IImasterII/mitk-rk-site/assets/photos/impeller-02.png

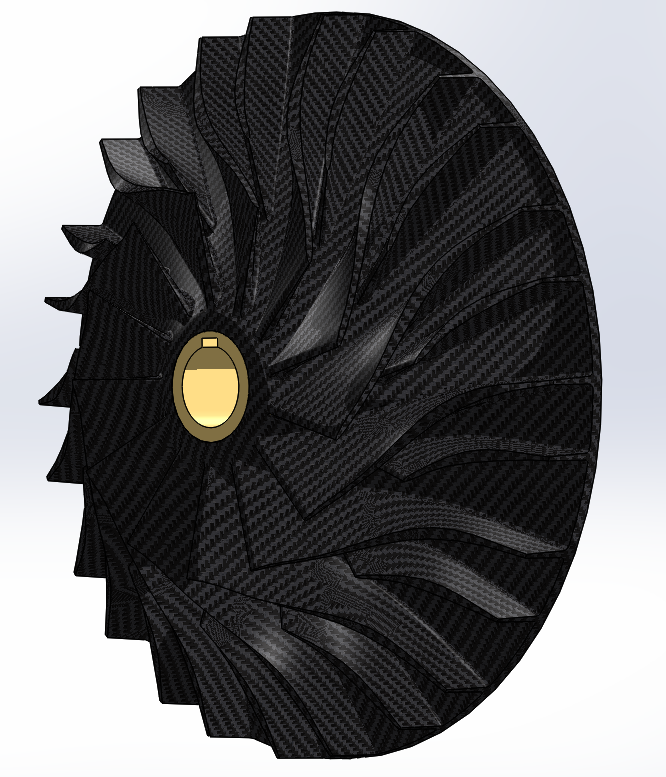
assets/photos/impeller-02.png
