IImasterII/mitk-rk-site/documents/0006_ps_d_.docx

Команда МИТК-РК

СОГЛАСОВАНО __________ | УТВЕРЖДАЮ __________

РАБОЧИЕ КОЛЁСА РК-200-Э И РК-200-Д ДИАМЕТРОМ 200 ММ

ПАСПОРТ РК-200-Д

EMTH.19.01.02.59.00.000.0006 ПС

2026

# 1 Идентификационные данные

Таблица 1 — Идентификация конкретного экземпляра

Поле | Значение
Обозначение | РК-200-Д
Критерий оптимизации | максимальное расчётное давление (одномерная модель)
Материальное исполнение | М1 / М2 (нужное отметить); М2 — 1 наружный слой ткани 0,2 мм (сухая)
Серийный номер
Дата изготовления
Файл модели/версия
Партия PA12-CF10
Ответственный изготовитель

# 2 Основные параметры

Таблица 2 — Номинальные геометрические параметры

Параметр | Значение
D2 | 200 мм
D1s | 105,075 мм
D1h | 40 мм
b2 | 14,242 мм
Основные/сплиттерные лопатки | 13/13
Угол назад от радиального | 5,000°
Задний диск | 3 мм
Втулка | Сталь 40Х; H49,5; Ø30/Ø22; паз 6×6 мм

# 3 Предварительные расчётные ориентиры

Таблица 3 — Предварительные расчётные ориентиры

n, мин⁻¹ | ηₜₜ, % | πₜₜ | Δpₜ, кПа | ṁ, кг/с | P, кВт | M, Н·м
3000 | — | ≈1,0072 | ≈0,727 | ≈0,062 | — | —
12000 | ≈71,23 | ≈1,1193 | ≈12,089 | ≈0,254 | ≈3,615 | ≈2,877

Статус значений. Таблица 3 содержит предварительные расчётные ориентиры, а не подтверждённые характеристики изделия. На 3 000 мин⁻¹ давление и расход оценены масштабированием; КПД, мощность и момент не назначены и определяются на стенде. Данные для 12 000 мин⁻¹ относятся только к расчётной точке и не разрешают разгон. Результаты CFD, FEA, модального анализа и стенда вносят в раздел 7 по подписанным отчётам.

# 4 Данные изготовления

Таблица 4 — Данные изготовления

Параметр | Запись | Параметр | Запись
Принтер/серийный номер | | Сопло
Слайсер/профиль | | Высота слоя | __________ мм
Сушка | 100 °C/10 ч; факт __________ | Отжиг | 100 °C/16 ч; факт __________
Масса после печати | __________ г | Масса готового | __________ г
Клей втулки | | Усилие запрессовки | __________ кН
Для М2 ткань | | Эпоксидная система

# 5 Результаты приёмки

Таблица 5 — Результаты приёмочного контроля

Контроль | Результат | Статус
Наружный диаметр D2 | __________ мм | годно / не годно (нужное отметить)
Радиальное биение | __________ мм | годно / не годно (нужное отметить)
Торцевое биение | __________ мм | годно / не годно (нужное отметить)
Визуальный контроль лопаток | | годно / не годно (нужное отметить)
Втулка и клеевое соединение | | годно / не годно (нужное отметить)
Остаточный дисбаланс | __________ г·мм | годно / не годно (нужное отметить)
Заключение | годно / доработка / брак (нужное отметить)

# 6 История испытаний и осмотров

Таблица 6 — История испытаний и осмотров

Дата | Режим | Наработка | Результат/дефекты | Подпись
| __________ мин⁻¹
| __________ мин⁻¹
| __________ мин⁻¹
| __________ мин⁻¹
| __________ мин⁻¹
| __________ мин⁻¹
| __________ мин⁻¹
| __________ мин⁻¹

# 7 Результаты CAE

Таблица 7 — Контролируемые результаты расчётов

Расчёт | Документ | Ключевые результаты | Статус
ANSYS CFD | № __________
ANSYS Mechanical | № __________
Modal | № __________

Ограничение. Незаполненный паспорт является только формой регистрационного документа и не подтверждает годность конкретного экземпляра. Режим 3 000 мин⁻¹ допускается после заполнения разделов изготовления и приёмки, балансировки и письменного допуска по ПМ. Разгон до 12 000 мин⁻¹ запрещён до закрытия CFD/FEA, модального анализа, проверки втулки и защитного корпуса и выпуска отдельного письменного допуска.

EMTH.19.01.02.59.00.000.0006 ПС Вер. Лист 01 3 Изм. Лист № докум. Подп. Дата Копировал Формат A4

Изм. Лист № докум. Подп. Дата Разраб. EMTH.19.01.02.59.00.000.0006 ПС 01 Пров. Т. контр. Рабочие колёса РК-200-Э и РК-200-Д диаметром 200 мм Лит. Лист Листов Н. контр. 2 1 Утв. Команда МИТК-РК Копировал Формат A4
