IImasterII/mitk-rk-site/documents/0009_tb.docx

Команда МИТК-РК

СОГЛАСОВАНО __________ | УТВЕРЖДАЮ __________

РАБОЧИЕ КОЛЁСА РК-200-Э И РК-200-Д ДИАМЕТРОМ 200 ММ

ТАБЛИЦА. МАТРИЦА ТРЕБОВАНИЙ И ПОДТВЕРЖДЕНИЙ

EMTH.19.01.02.59.00.000.0009 ТБ

2026

# 1 Правила статусов

Таблица 1 — Локальные коды статусов матрицы

Код | Статус | Смысл
П | Подтверждено | Есть объективное доказательство
З | Задано проектом | Требование зафиксировано, подтверждение предстоит
О | Открыто | Нужен расчёт, протокол или файл
Н/П | Не применяется | Не относится к выбранному исполнению

# 2 Матрица

Таблица 2 — Требования, методы и объективные доказательства

ID | Требование | Метод | Доказательство | Статус
G-01 | После удаления припуска заготовки Ø202 мм D2 готового колеса — 200 мм | STEP/чертёж | 0007 Д; размерный протокол | П для Э; О для Д
G-02 | Задний диск 3 мм | STEP/чертёж | 0007 Д | П для Э; О для Д
G-03 | Э: 10+10 лопаток | STEP | 0007 Д | П
G-04 | Д: 13+13 лопаток | STEP | 0007 Д | О до финального STEP
G-05 | Одно допустимое твёрдое тело | STEP-анализ | 0007 Д | П для Э; О для Д
G-06 | Корни лопаток соединены со ступицей | STEP/сечения | 0007 Д | П для Э; О для Д
M-01 | Материал Fiberon PA12-CF10 | Паспорт партии | 0005/0006 ПС | З
M-02 | Сушка 100 °C/10 ч | Журнал | 0004 МК; протокол | З
M-03 | Отжиг 100 °C/16 ч | Термограмма | 0004 МК; протокол | З
M-04 | М2: один наружный слой ткани 0,2 мм (сухая) | Паспорт/измерение | 0011 Д; протокол М2 | З
I-01 | Втулка из стали 40Х: H49,5; Ø30/Ø22 | Чертёж/контроль | 0002 ТУ; 0005/0006 ПС | З
I-02 | Шпоночный паз 6×6 | Калибр/контроль | 0005/0006 ПС | З
I-03 | Накатка, запрессовка и клей | Протокол сборки | 0004 МК; 0005/0006 ПС | З
A-01 | Допуск и безопасная работа на стенде при 3 000 мин⁻¹ | Стенд | 0003 ПМ; протокол | О
A-02 | Расчётная точка 12 000 мин⁻¹; эксплуатация запрещена без отдельного допуска | CFD/Mechanical | отчёты CFD/FEA/Modal; отдельный допуск | О
A-03 | Э: ηₜₜ≈74 % по предварительной одномерной модели | Одномерный расчёт | 0001 ПЗ; машинный протокол | О до протокола расчёта
A-04 | Д: ηₜₜ≈71 % по предварительной одномерной модели | Одномерный расчёт | 0001 ПЗ; машинный протокол | О до протокола расчёта
A-05 | Э: Δpₜ≈10,9 кПа при 12 000 мин⁻¹, предварительно | Одномерный расчёт | 0001 ПЗ; машинный протокол | О до протокола расчёта
A-06 | Д: Δpₜ≈12,1 кПа при 12 000 мин⁻¹, предварительно | Одномерный расчёт | 0001 ПЗ; машинный протокол | О до протокола расчёта
S-01 | Коэффициент запаса по Mechanical | ANSYS | отчёт FEA | О
S-02 | Отсутствие опасного резонанса | Modal/Campbell | отчёт Modal/Campbell | О
S-03 | Балансировка до стенда | Станок | протокол балансировки | З
Q-01 | Нет трещин и расслоений | 100 % контроль | 0011 Д; карта дефектов | З
Q-02 | Прослеживаемость партии и профиля | Журнал | 0005/0006 ПС | З
Q-03 | Повторяемость стенда не хуже 5 % | Два запуска | 0003 ПМ; протокол | О
DOC-01 | Пояснительная записка выпущена и проверена | Контроль документа | 0001 ПЗ | П
DOC-02 | Маршрутная карта выпущена и проверена | Контроль документа | 0004 МК | П
DOC-03 | ТУ и ПМ выпущены и проверены | Контроль документа | 0002 ТУ; 0003 ПМ | П
DOC-04 | Чертежи выпущены | Нормоконтроль | комплект КД | О
DOC-05 | ANSYS и стендовый отчёт выпущены | Контроль документа | отчёты | О
S-04 | Защитный корпус рассчитан и принят | Расчёт/осмотр | расчёт удержания; акт приёмки | О
S-05 | Блокировка и аварийный останов проверены | Функциональная проверка | 0011 Д; лист готовности | О

# 3 Управление открытыми пунктами

Коды П/З/О/Н/П являются локальными статусами матрицы и не обозначают виды документов ЕСКД. Открытый пункт переводят в статус «П» только после ссылки на конкретный файл, номер протокола, версию модели или отчёт. Матрицу обновляют при каждой значимой редакции CAD, материала, втулки, CAE или программы испытаний.

EMTH.19.01.02.59.00.000.0009 ТБ Вер. Лист 01 3 Изм. Лист № докум. Подп. Дата Копировал Формат A4

Изм. Лист № докум. Подп. Дата Разраб. EMTH.19.01.02.59.00.000.0009 ТБ 01 Пров. Т. контр. Рабочие колёса РК-200-Э и РК-200-Д диаметром 200 мм Лит. Лист Листов Н. контр. 2 1 Утв. Команда МИТК-РК Копировал Формат A4
