IImasterII/mitk-rk-site/documents/0010_sp.docx

Команда МИТК-РК

СОГЛАСОВАНО __________ | УТВЕРЖДАЮ __________

РАБОЧИЕ КОЛЁСА РК-200-Э И РК-200-Д ДИАМЕТРОМ 200 ММ

СПЕЦИФИКАЦИЯ

EMTH.19.01.02.59.00.000.0010 СП

2026

# 1 Правила применения

Спецификация устанавливает состав одного опытного рабочего колеса выбранного исполнения. Для полной матрицы Э/Д × М1/М2 таблицу 1 применяют к каждому из четырёх экземпляров; количество в таблице указано на одно колесо. Марка втулки зафиксирована — сталь 40Х. Внутренние обозначения тел колёс сохраняют предварительный статус до выпуска рабочих чертежей; длину шпонки, марки клея, ткани и смолы и нормы расхода вносят в следующую редакцию по утверждённым чертежам и закупочным данным.

Таблица 1 — Состав одного опытного рабочего колеса

Раздел | Обозначение | Наименование | Кол. на исполнение | Применение
Документация | EMTH.19.01.02.59.00.000.0001 ПЗ | Пояснительная записка | 1 | Общая
Документация | EMTH.19.01.02.59.00.000.0002 ТУ | Технические условия | 1 | Общая
Документация | EMTH.19.01.02.59.00.000.0003 ПМ | Программа и методика испытаний | 1 | Общая
Документация | EMTH.19.01.02.59.00.000.0004 МК | Маршрутная карта изготовления | 1 | Общая
Детали | МИТК-РК.200.Э.001 | Тело колеса РК-200-Э | 1 | Только Э
Детали | МИТК-РК.200.Д.001 | Тело колеса РК-200-Д | 1 | Только Д
Детали | МИТК-РК.200.002 | Втулка из стали 40Х; H49,5; Ø30/Ø22; паз 6×6 мм | 1 | Все
Стандартные | ГОСТ 23360-78 | Шпонка 6×6×______ мм | 1 | Все
Материалы | Fiberon PA12-CF10 | Филамент Ø1,75 мм | по факту | Все
Материалы | ____________________________ | Конструкционный клей PA12-CF10—сталь 40Х | по норме | Все
Материалы | ____________________________ | Углеродная ткань: 1 наружный слой, толщина сухой ткани 0,2 мм | по карте | Только М2
Материалы | ____________________________ | Эпоксидная система | по карте | Только М2
Комплект | EMTH.19.01.02.59.00.000.0005 ПС / EMTH.19.01.02.59.00.000.0006 ПС | Паспорт экземпляра | 1 | Все

# 2 Матрица исполнений

Таблица 2 — Применяемость компонентов по исполнениям

Исполнение | Геометрия | Матрица | Втулка | Наружный слой
РК-200-Э-М1 | Э | PA12-CF10 | Сталь 40Х | Нет
РК-200-Д-М1 | Д | PA12-CF10 | Сталь 40Х | Нет
РК-200-Э-М2 | Э | PA12-CF10 | Сталь 40Х | 1 наружный слой, 0,2 мм (сухая)
РК-200-Д-М2 | Д | PA12-CF10 | Сталь 40Х | 1 наружный слой, 0,2 мм (сухая)

# 3 Данные для заполнения

- состояние поставки и термообработка втулки из стали 40Х — по рабочему чертежу;
- длина и материал шпонки;
- марка клея и норма расхода;
- марка, переплетение и поверхностная плотность углеродной ткани;
- марка эпоксидной системы и массовое соотношение компонентов;
- фактическая масса PA12-CF10 по отчёту слайсера и взвешиванию;
- обозначения выпущенных чертежей.

EMTH.19.01.02.59.00.000.0010 СП Вер. Лист 01 3 Изм. Лист № докум. Подп. Дата Копировал Формат A4

Изм. Лист № докум. Подп. Дата Разраб. EMTH.19.01.02.59.00.000.0010 СП 01 Пров. Т. контр. Рабочие колёса РК-200-Э и РК-200-Д диаметром 200 мм Лит. Лист Листов Н. контр. 2 1 Утв. Команда МИТК-РК Копировал Формат A4
