IImasterII/mitk-rk-site/documents/0011_d_forms.docx

Команда МИТК-РК

СОГЛАСОВАНО __________ | УТВЕРЖДАЮ __________

РАБОЧИЕ КОЛЁСА РК-200-Э И РК-200-Д ДИАМЕТРОМ 200 ММ

ФОРМЫ ПРОТОКОЛОВ

EMTH.19.01.02.59.00.000.0011 Д

2026

Формы являются контролируемыми приложениями к EMTH.19.01.02.59.00.000.0003 ПМ. Их распечатывают, заполняют фактическими данными без исправления установленных требований, подписывают и связывают с серийным номером образца и файлами измерений.

# 1 Протокол входного контроля

Таблица 1 — Входной контроль экземпляра

Контроль | Запись
Модель/исполнение | ________________
STEP/версия/SHA-256 | ________________
Партия PA12-CF10 | ________________
Состояние упаковки | ________________
Втулка/марка/партия | ________________
Клей/срок годности | ________________
Ткань и смола М2 | ________________
Заключение | годно / не годно (нужное отметить)

# 2 Журнал печати и отжига

Таблица 2 — Журнал печати и отжига

Параметр | Запись | Параметр | Запись
Принтер/сопло | ________________ | Слайсер/профиль | ________________
Сушка | 100 °C/10 ч; факт __________ | RH подачи | ________________ %
Сопло | ________________ °C | Стол | ________________ °C
Обдув | ________________ % | Заполнение | ________________ %
Начало/конец печати | ________________/________________ | Масса | ________________ г
Отжиг | 100 °C/16 ч; факт __________ | Термограмма | ____________________________
Дефекты | ____________________________ | Решение | ________________

# 3 Протокол геометрического контроля

Таблица 3 — Геометрический контроль

Параметр | Требование | Факт | Средство | Статус
D2 | 200 мм; допуск по чертежу | ________________ | ________________ | ________________
Полная высота | по рабочему чертежу | ________________ | ________________ | ________________
Ø отверстия | Ø30 мм | ________________ | ________________ | ________________
Плоскостность диска | по рабочему чертежу | ________________ | ________________ | ________________
Радиальное биение | по рабочему чертежу/ПМ | ________________ | ________________ | ________________
Торцевое биение | по рабочему чертежу/ПМ | ________________ | ________________ | ________________
Количество лопаток | Э: 10+10; Д: 13+13 | ________________ | ________________ | ________________
Минимальная толщина кромки | по рабочему чертежу | ________________ | ________________ | ________________
Целостность корней | трещины и щели не допускаются | ________________ | ________________ | ________________

# 4 Протокол сборки втулки

Таблица 4 — Сборка втулки из стали 40Х

Параметр втулки из стали 40Х, H49,5 мм | Запись
Ø отверстия после отжига | __________ мм
Ø втулки по накатке | __________ мм
Фактический натяг | __________ мм
Клей/партия | ________________
Подготовка поверхности | ____________________________
Максимальное усилие запрессовки | __________ кН
Осевое положение втулки | по сборочному чертежу; факт __________ мм
Режим отверждения | ________________
Осмотр ступицы | ________________
Заключение | годно / не годно (нужное отметить)

# 5 Протокол армирования М2

Таблица 5 — Армирование исполнения М2

Параметр | Запись
Ткань/партия/поверхностная плотность | ________________
Число слоёв и сухая толщина | 1 наружный слой; 0,2 мм
Масса сухого раскроя | __________ г
Эпоксидная система/партия | ________________
Масса смолы/отвердителя | __________ г / __________ г
Вакуум/давление | ________________
Цикл отверждения | ________________
Прирост массы | __________ г
Дефекты слоя | ________________
Заключение | годно / не годно (нужное отметить)

# 6 Протокол балансировки

Таблица 6 — Балансировка

Параметр | Запись
Модель/серийный номер | ________________
Масса | __________ г
Оправка/станок | ________________
Частота балансировки | __________ мин⁻¹
Исходный дисбаланс, плоскость 1 | __________ г·мм / __________ °
Плоскость 2 | __________ г·мм / __________ °
Способ коррекции | ________________
Остаточный дисбаланс | __________ г·мм
Критерий | ________________
Заключение | годно / не годно (нужное отметить)

# 7 Протокол стендового испытания

Модель __________; исполнение __________; серийный номер __________; дата __________; оператор __________; приборы/каналы ______________________________.

Таблица 7 — Ступенчатый разгон до 3 000 мин⁻¹

nзад, мин⁻¹ | nфакт, мин⁻¹ | Δpₜ, Па | Q, м³/с | T, °C | Вибрация RMS/1× | Примечание
500 | ________________ | ________________ | ________________ | ________________ | ________________ | ________________
1000 | ________________ | ________________ | ________________ | ________________ | ________________ | ________________
1500 | ________________ | ________________ | ________________ | ________________ | ________________ | ________________
2000 | ________________ | ________________ | ________________ | ________________ | ________________ | ________________
2500 | ________________ | ________________ | ________________ | ________________ | ________________ | ________________
3000 | ________________ | ________________ | ________________ | ________________ | ________________ | ________________

Таблица 8 — Повторяемость на режиме 3 000 мин⁻¹

Серия | Δpₜ при 3 000, Па | Q, м³/с | ηₜₜ при наличии Pвала | Вибрация RMS/1×
Запуск 1 | ________________ | ________________ | ________________ | ________________
Запуск 2 | ________________ | ________________ | ________________ | ________________
Среднее | ________________ | ________________ | ________________ | ________________

# 8 Акт осмотра после испытания

Таблица 9 — Осмотр до и после испытания

Объект | До | После | Изменение | Решение
Трещины/расслоения | ________________ | ________________ | ________________ | ________________
Кромки лопаток | ________________ | ________________ | ________________ | ________________
Корни лопаток | ________________ | ________________ | ________________ | ________________
Ступица | ________________ | ________________ | ________________ | ________________
Втулка/клей | ________________ | ________________ | ________________ | ________________
Наружный слой М2 | ________________ | ________________ | ________________ | ________________
Радиальное биение | ________________ | ________________ | ________________ | ________________
Торцевое биение | ________________ | ________________ | ________________ | ________________

Общее заключение: работоспособно / требуется доработка / испытания прекращены (нужное отметить). Подписи комиссии: ______________________________.

EMTH.19.01.02.59.00.000.0011 Д Вер. Лист 01 3 Изм. Лист № докум. Подп. Дата Копировал Формат A4

Изм. Лист № докум. Подп. Дата Разраб. EMTH.19.01.02.59.00.000.0011 Д 01 Пров. Т. контр. Рабочие колёса РК-200-Э и РК-200-Д диаметром 200 мм Лит. Лист Листов Н. контр. 2 1 Утв. Команда МИТК-РК Копировал Формат A4
