IImasterII/mitk-rk-site/documents/0012_tp.docx

Команда МИТК-РК

СОГЛАСОВАНО __________ | УТВЕРЖДАЮ __________

РАБОЧИЕ КОЛЁСА РК-200-Э И РК-200-Д ДИАМЕТРОМ 200 ММ

ВЕДОМОСТЬ ТЕХНИЧЕСКОГО ПРОЕКТА

EMTH.19.01.02.59.00.000.0012 ТП

2026

# 1 Назначение

Ведомость устанавливает фактический состав технической документации проекта гибридных полуоткрытых рабочих колёс РК-200-Э и РК-200-Д диаметром 200 мм. В перечень включены только файлы, находящиеся в комплекте на дату выпуска настоящей редакции.

Обозначения приведены в принятой системе проекта. Сокращение вида документа отделено от базового обозначения пробелом; латинские внутренние сокращения вместо видов документов ЕСКД не применяются.

Таблица 1 — Состав технической документации

№ | Обозначение | Документ | Статус
1 | EMTH.19.01.02.59.00.000.0001 ПЗ | Пояснительная записка | Проверен
2 | EMTH.19.01.02.59.00.000.0002 ТУ | Технические условия | Проверен
3 | EMTH.19.01.02.59.00.000.0003 ПМ | Программа и методика испытаний | Проверен
4 | EMTH.19.01.02.59.00.000.0004 МК | Маршрутная карта изготовления | Проверен
5 | EMTH.19.01.02.59.00.000.0005 ПС | Паспорт РК-200-Э | Проверен
6 | EMTH.19.01.02.59.00.000.0006 ПС | Паспорт РК-200-Д | Проверен
7 | EMTH.19.01.02.59.00.000.0007 Д | Отчёт верификации 3D-моделей | Проверен
8 | EMTH.19.01.02.59.00.000.0008 Д | Анализ видов и последствий отказов (FMEA) | Проверен
9 | EMTH.19.01.02.59.00.000.0009 ТБ | Таблица. Матрица требований и подтверждений | Проверен
10 | EMTH.19.01.02.59.00.000.0010 СП | Спецификация | Проверен
11 | EMTH.19.01.02.59.00.000.0011 Д | Формы протоколов | Проверен
12 | EMTH.19.01.02.59.00.000.0012 ТП | Ведомость технического проекта | Проверен
13 | EMTH.19.01.02.59.00.000.0013 Д | Отчёт о патентных исследованиях | Проверен
14 | EMTH.19.01.02.59.00.000.0014 ПЗ | Пояснительная записка. Технико-экономическое обоснование | Проверен
15 | EMTH.19.01.02.59.00.000.0015 ПЗ | Пояснительная записка. Обоснование выбора привода | Проверен
16 | EMTH.19.01.02.59.00.000.0016 Э3 | Схема электрическая принципиальная | Проверен
17 | EMTH.19.01.02.59.00.000.0017 С2 | Схема комбинированная функциональная стенда | Проверен

# 2 Управление версиями

— Статус «Проверен» означает, что содержание, обозначение и вёрстка текущей редакции прошли аудит.

— Статус «Аудит ожидается» означает наличие файла в комплекте без подтверждения его окончательной редакции.

— После исправления документа ведомость пересобирают, статус изменяют на «Проверен», а прежнюю редакцию сохраняют в архиве.

— Изменение геометрии, материала, втулки или режима испытаний требует проверки всех связанных документов.

EMTH.19.01.02.59.00.000.0012 ТП Вер. Лист 01 3 Изм. Лист № докум. Подп. Дата Копировал Формат A4

Изм. Лист № докум. Подп. Дата Разраб. EMTH.19.01.02.59.00.000.0012 ТП 01 Пров. Т. контр. Рабочие колёса РК-200-Э и РК-200-Д диаметром 200 мм Лит. Лист Листов Н. контр. 2 1 Утв. Команда МИТК-РК Копировал Формат A4
