IImasterII/mitk-rk-site/documents/presentation.pdf

# ГИБРИДНОЕ РАБОЧЕЕ КОЛЕСО

# Композитно-металлическая архитектура для высоконапорных центробежных компрессоров

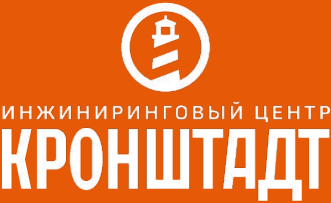
[picture p63: figure]
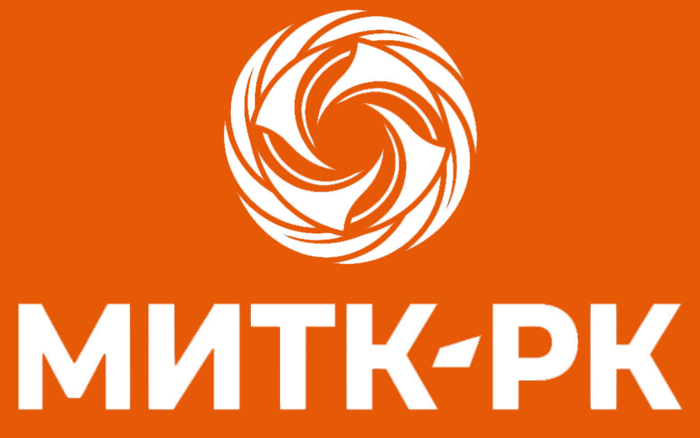
[picture p64: figure]

31.07.2026

# Эксперт: Неватус Иван Беседин Станислав

# Разработчики: Сивуда Максим Ягофаров Тимур Аюпов Камиль Бардашкин Даниил Котельников Игорь Фефелов Данил Ярушин Денис

# СОСТАВ КОМАНДЫ

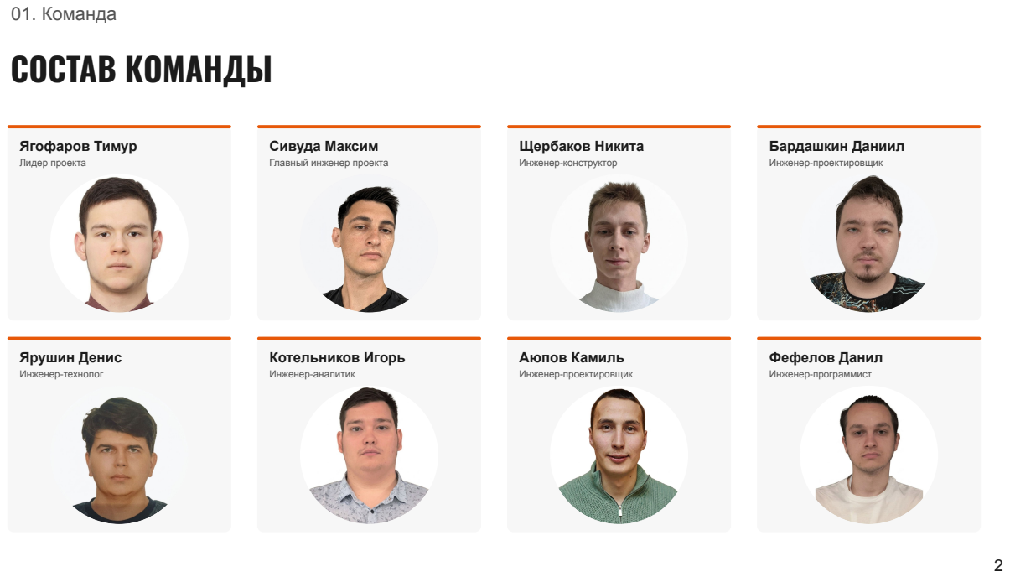
[picture p65: page 2]
Ягофаров Тимур; Лидер проекта; Сивуда Максим; Щербаков Никита; Инженер-конструктор; Бардашкин Даниил; Инженер-проектировщик; Ярушин Денис; Инженер-технолог; Котельников Игорь; Инженер-аналитик; Аюпов Камиль; Фефелов Данил; Инженер-программист; 01. Команда

Главный инженер проекта

02. Постановка задачи

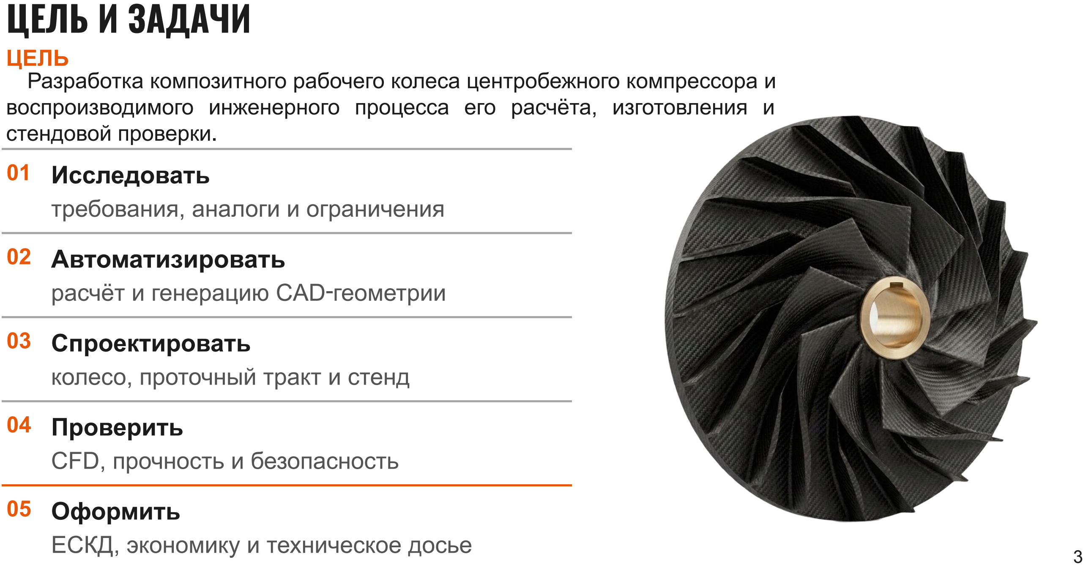
[picture p66: figure]
ЦЕЛЬ И ЗАДАЧИ; ЦЕЛЬ; 02 Автоматизировать расчёт и генерацию CAD‑геометрии; 03 Спроектировать; колесо, проточный тракт и стенд; 04 Проверить; CFD, прочность и безопасность; 05 Оформить; ЕСКД, экономику и техническое досье; 01 Исследовать; требования, аналоги и ограничения; стендовой проверки.

Разработка композитного рабочего колеса центробежного компрессора и воспроизводимого инженерного процесса его расчёта, изготовления и

# ИННОВАЦИОННОСТЬ И ТЕХНИЧЕСКИЕ РЕШЕНИЯ

02. Постановка задачи

# Автоматизация проектирования

Программный комплекс
Параметрическая генерация
CAD-геометрии. Автономная
создание модели рабочего
колеса с незначительной
доработкой в CAD системе.

# Доступность материалов

Рабочее колесо
Возможность быстро
разработать и протестировать рабочее колесо

# Импортозамещение

Независимость проекта
Полная | независимость | от
зарубежных игроков.
01 | 02 | 03

# ОРГАНИЗАЦИЯ ПРОЦЕССА РАЗРАБОТКИ

### 8 участников · 5 инженерных направлений · единый комплект результатов

01
Требования

02
Цифровая модель

03
Конструкция

04
Проверка

05
Выпуск

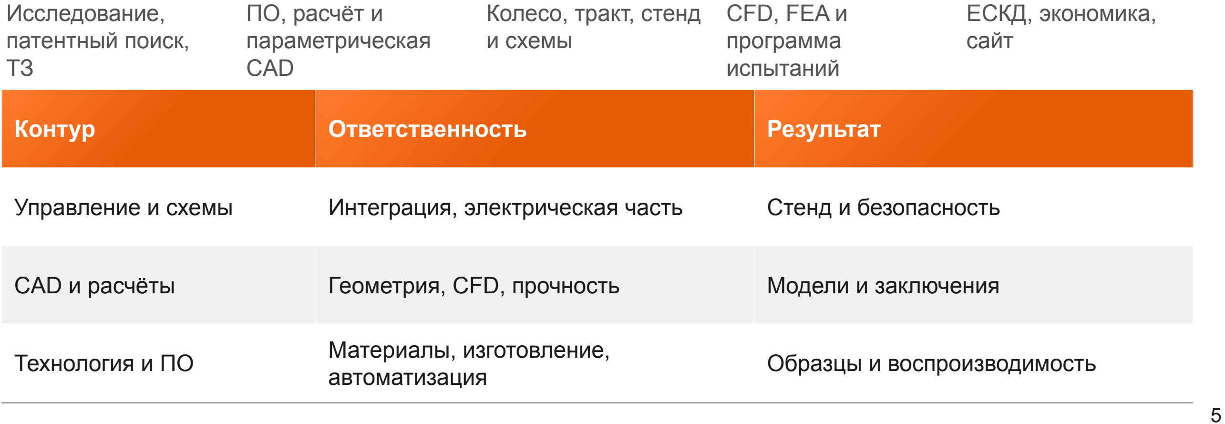
[picture p67: figure]
Исследование, патентный поиск, ТЗ; ПО, расчёт и параметрическая CAD; Колесо, тракт, стенд и схемы; CFD, FEA и программа испытаний; ЕСКД, экономика, сайт; Контур; Ответственность; Результат; автоматизация; Образцы и воспроизводимость

Управление и схемы | Интеграция, электрическая часть | Стенд и безопасность
CAD и расчёты | Геометрия, CFD, прочность | Модели и заключения
Технология и ПО | Материалы, изготовление,
03. Организация работ

# ДОРОЖНАЯ КАРТА

04. Планирование
Этап | 22-28 июня | 29 июня - 5 июля | 6 - 12 июля | 13 - 19 июля | 20 -26 июля | 27 - 31 июля

Исследование

Программное обеспечение

Разработка рабочего колеса

Разработка воздуховода

Разработка стэнда

Документация

Сборка стэнда

Проверка работоспособности

Создание сайта

Презентация

# РАЗРАБОТКА ИЗДЕЛИЯ И СТЕНДА

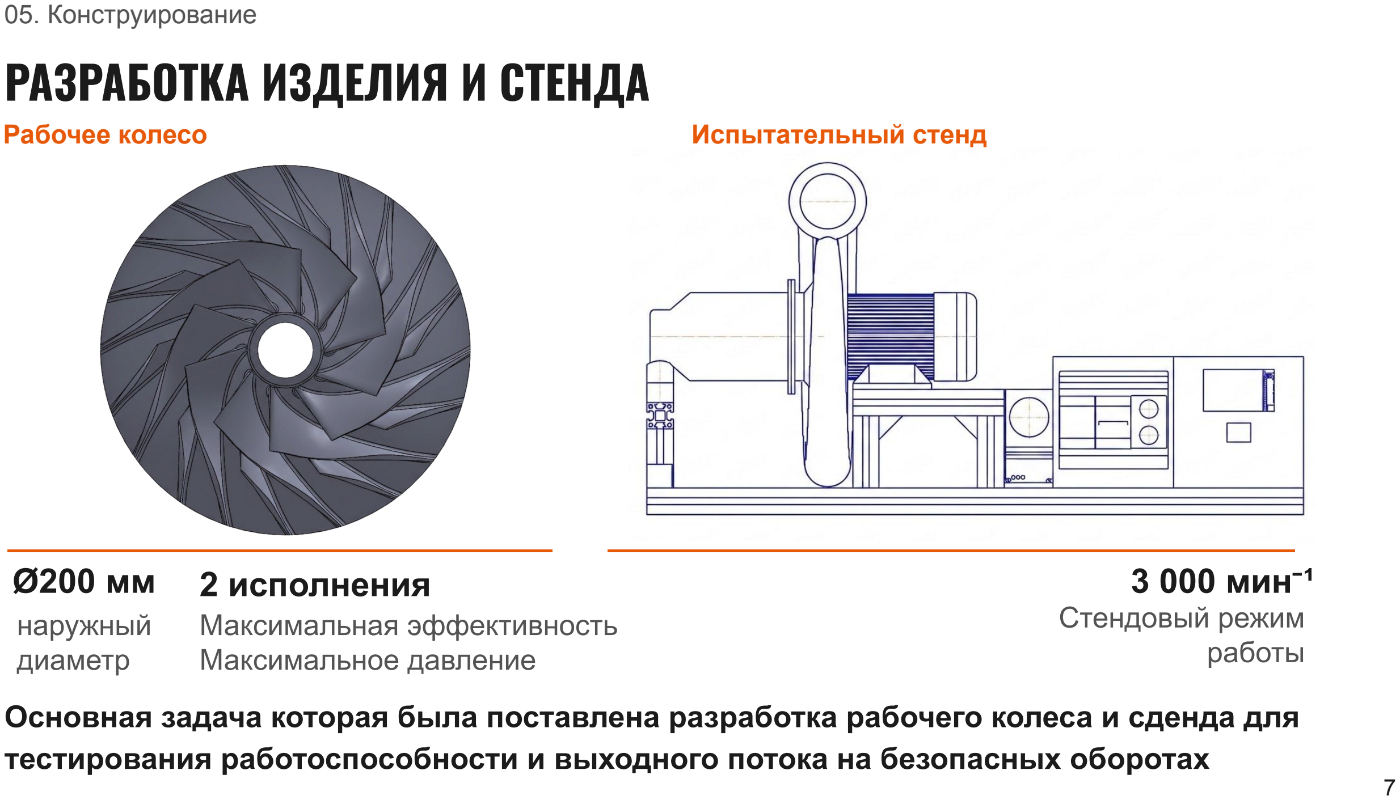
[picture p68: page 7]

Рабочее колесо

## Ø200 мм

наружный
диаметр

## 2 исполнения

Максимальная эффективность Максимальное давление

Испытательный стенд

## 3 000 мин⁻¹

Стендовый режим
работы

Основная задача которая была поставлена разработка рабочего колеса и сденда для тестирования работоспособности и выходного потока на безопасных оборотах

05. Конструирование

# ПРОГРАММНЫЙ КОМПЛЕКС АВТОМАТИЗИРОВАННОГО СОЗДАНИЯ КОЛЕСА

06. Программный комплекс

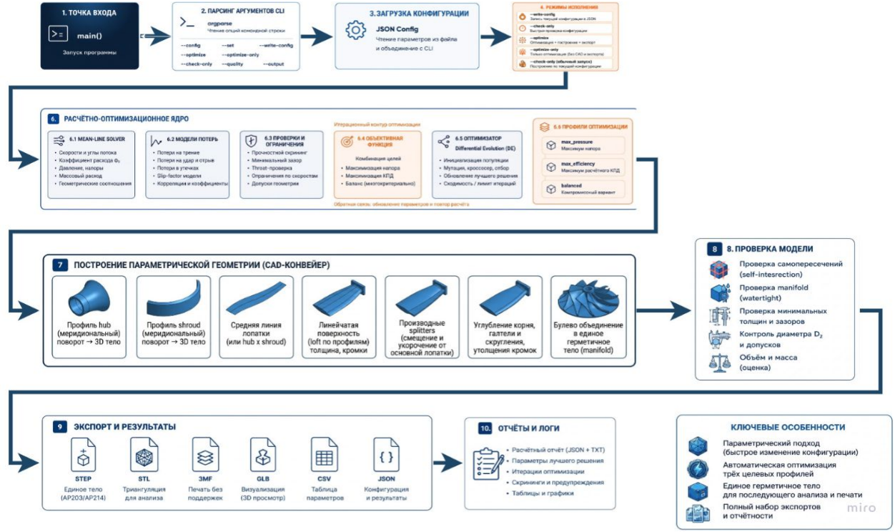
[picture p69: figure]

# ГЕОМЕТРИЯ И ВЫПУСК ЧЕРТЕЖЕЙ

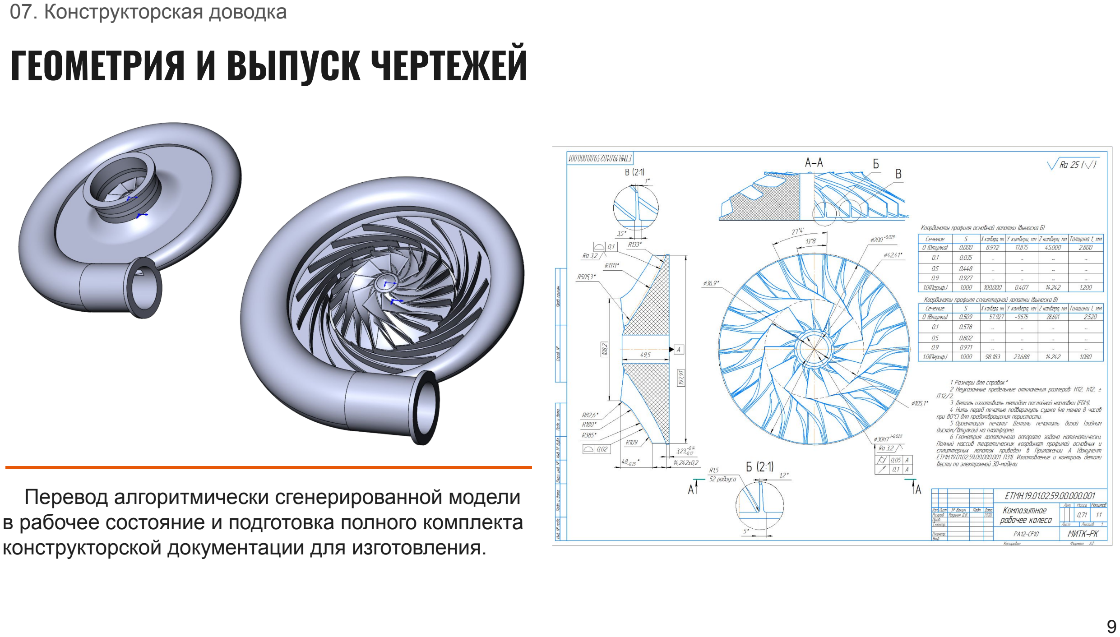
[picture p70: page 9]

07. Конструкторская доводка

Перевод алгоритмически сгенерированной модели в рабочее состояние и подготовка полного комплекта конструкторской документации для изготовления.

# ПРОФИЛИРОВАНИЕ ДИФФУЗОРА И ВОЗДУХОВОДА

01

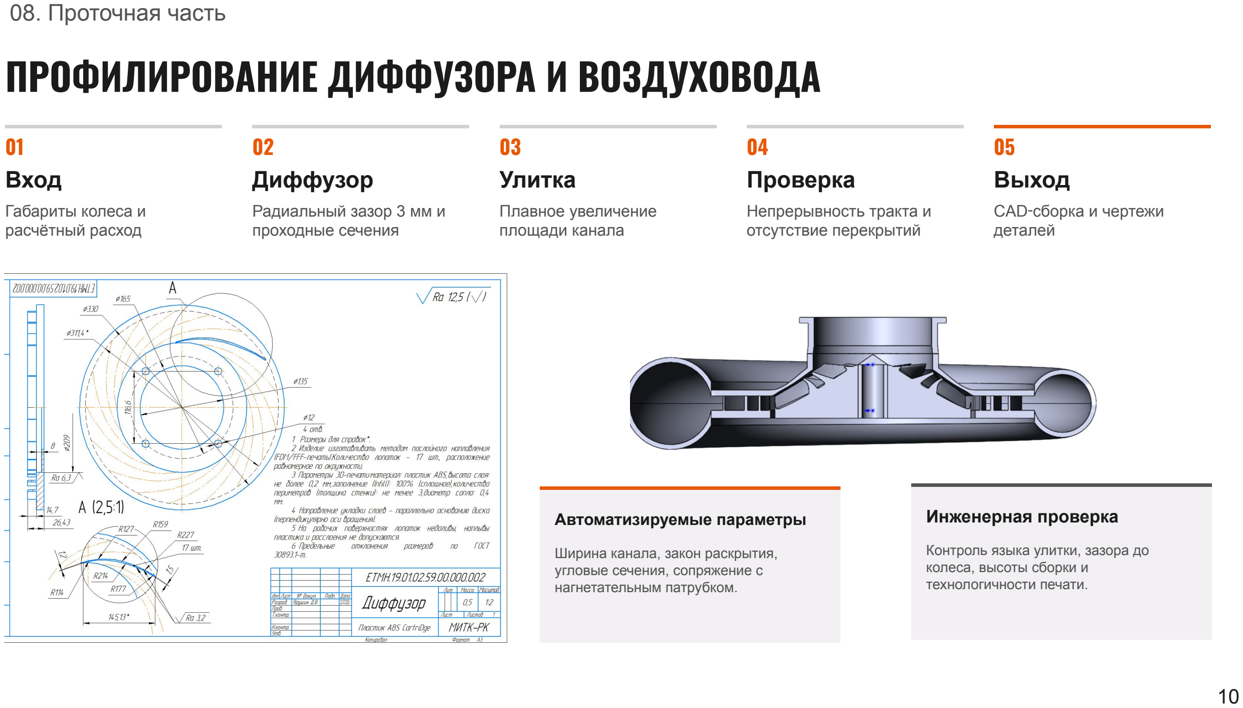
[picture p71: page 10]

08. Проточная часть

Вход

Габариты колеса и
расчётный расход

02

Диффузор

Радиальный зазор 3 мм и
проходные сечения

03

Улитка

Плавное увеличение
площади канала

04

Проверка

Непрерывность тракта и
отсутствие перекрытий

05

Выход

CAD‑сборка и чертежи
деталей

Автоматизируемые параметры

Ширина канала, закон раскрытия, угловые сечения, сопряжение с нагнетательным патрубком.

Инженерная проверка

Контроль языка улитки, зазора до колеса, высоты сборки и
технологичности печати.

09. Испытательный стенд

# ПОДБОР КОМПОНЕНТОВ

Подсистема | Выбранные элементы | Основание выбора
Привод | 5АИ80А2 · 1,5 кВт · 3 000 мин⁻¹ | Стендовый режим и доступный момент
Регулирование | ПЧ STV050U22M2 · 2,2 кВт | Плавный разгон и ограничение частоты
Измерения | | Расход, давление, температура, вибрация, обороты
Управление | STM32F411CEU6 · Raspberry Pi 4 | Сбор каналов, логика допуска и регистрация
Механика | Профиль 40×40 · виброопоры · кожух | Жёсткость, монтаж и безопасность

FT, PT, TT, VT, ST.

09. Испытательный стенд

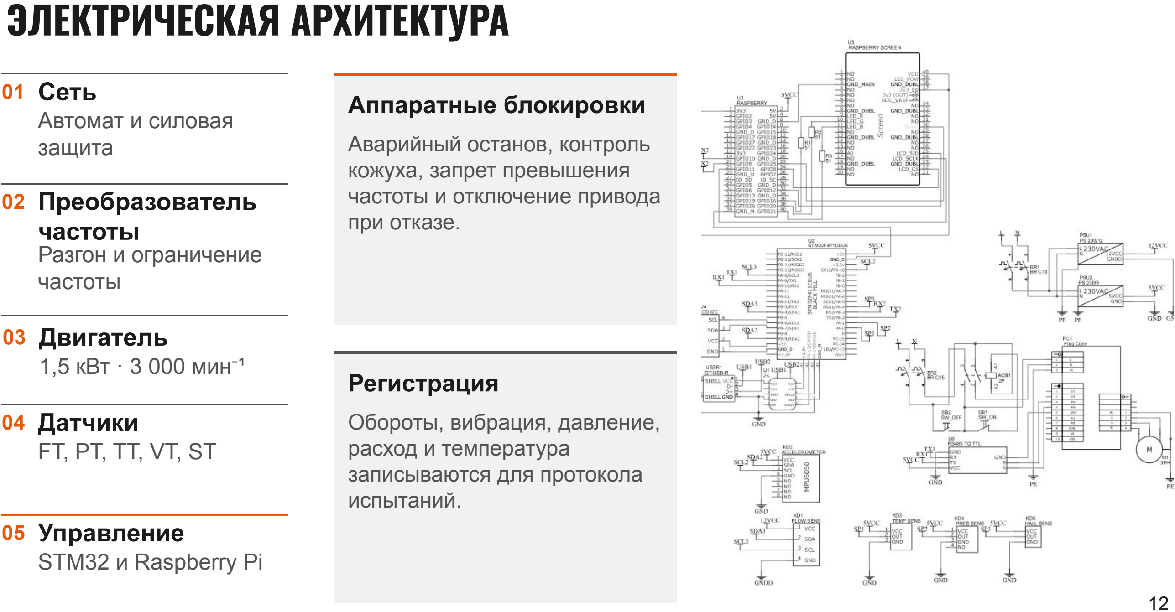
[picture p72: figure]
ЭЛЕКТРИЧЕСКАЯ АРХИТЕКТУРА; 01 Сеть Автомат и силовая защита; 02 Преобразователь частоты Разгон и ограничение частоты; 03 Двигатель 1,5 кВт · 3 000 мин; 04 Датчики FT, PT, TT, VT, ST; 05 Управление STM32 и Raspberry Pi; Аппаратные блокировки; Аварийный останов, контроль кожуха, запрет превышения частоты и отключение привода при отказе.; Регистрация; Обороты, вибрация, давление, расход и температура записываются для протокола испытаний.

# ЧЕРТЁЖ КОМПОНОВКИ СТЕНДА

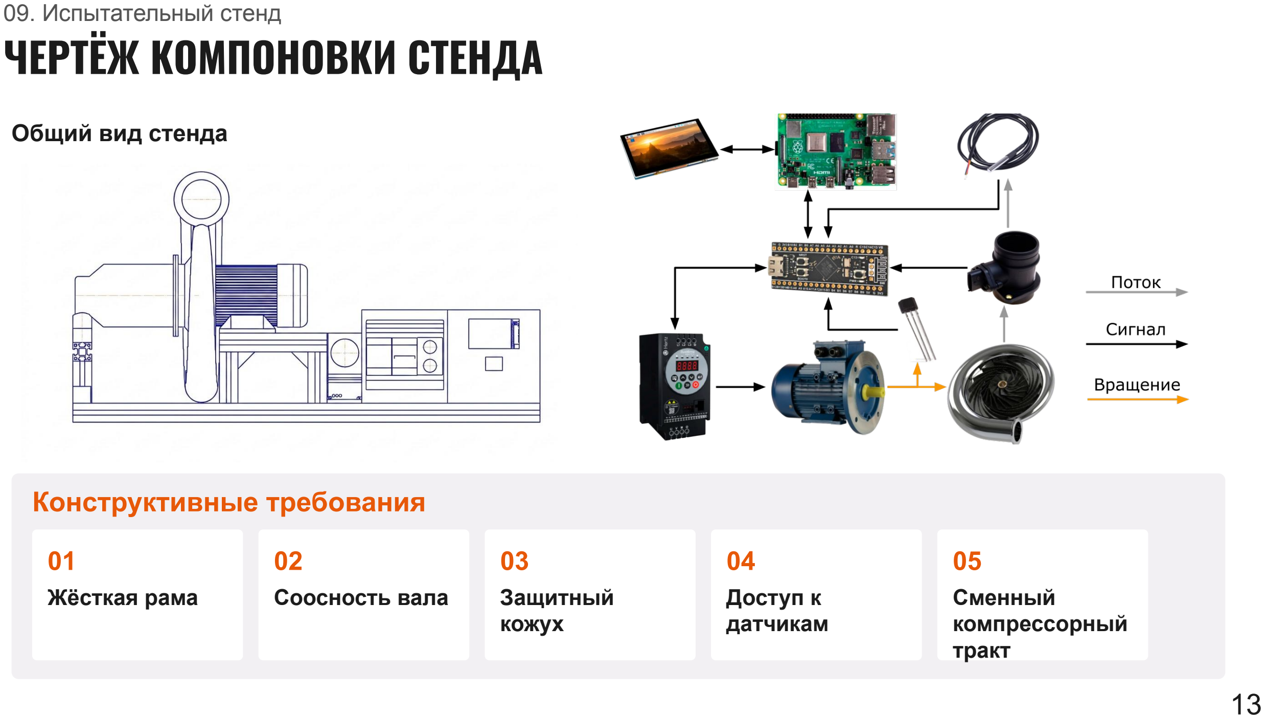
[picture p73: page 13]

09. Испытательный стенд

Общий вид стенда

Конструктивные требования

01

Жёсткая рама

02

Соосность вала

03

Защитный
кожух

04

Доступ к
датчикам

05

Сменный
компрессорный
тракт

# ПРОЧНОСТНОЙ ДОПУСК

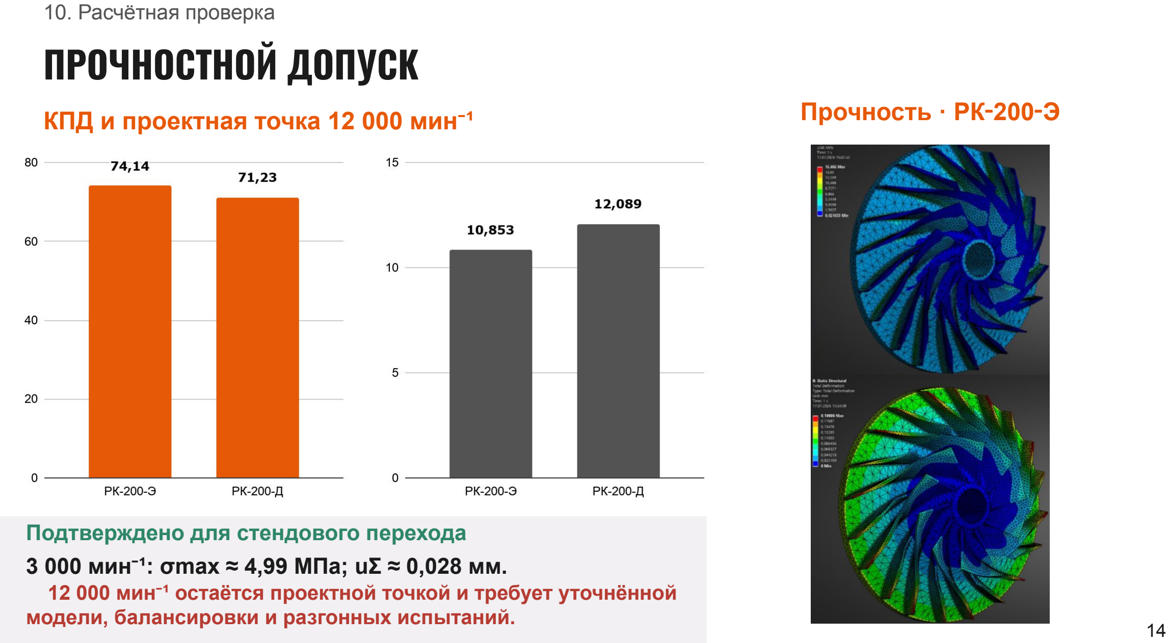
[picture p74: page 14]

10. Расчётная проверка
КПД и проектная точка 12 000 мин⁻¹ | Прочность · РК‑200‑Э

Подтверждено для стендового перехода
3 000 мин⁻¹: σmax ≈ 4,99 МПа; uΣ ≈ 0,028 мм.
12 000 мин⁻¹ остаётся проектной точкой и требует уточнённой
модели, балансировки и разгонных испытаний. | 14

11. Материалы и технология

# ВЫБОР МАТЕРИАЛОВ

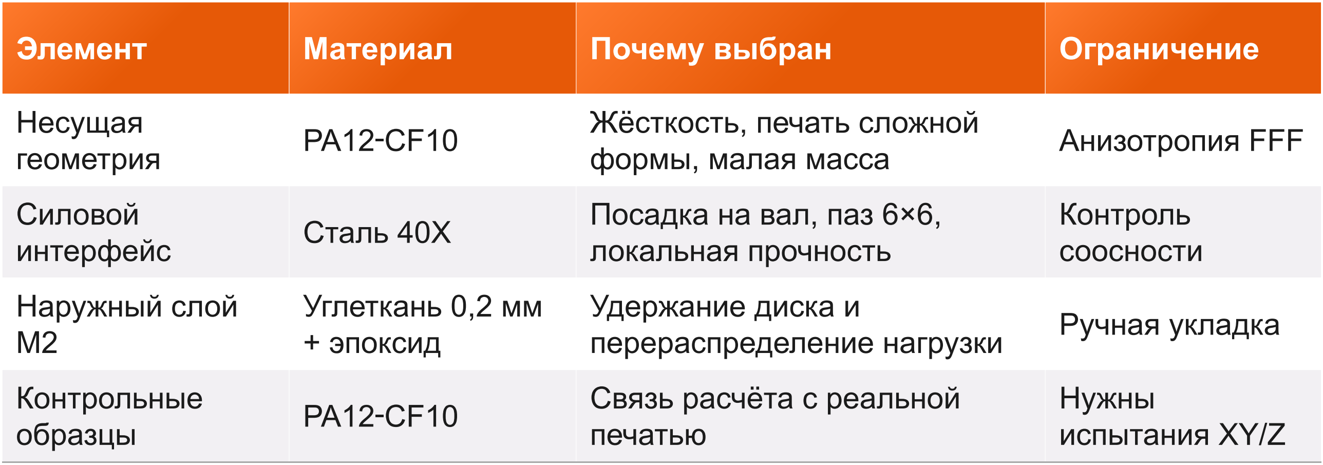
[picture p75: figure]
Несущая геометрия; Жёсткость, печать сложной; формы, малая масса; Анизотропия FFF; Силовой; локальная прочность; Контроль соосности; Наружный слой М2; Углеткань 0,2 мм + эпоксид; Удержание диска и перераспределение нагрузки; Ручная укладка; Контрольные; печатью; Нужны испытания XY/Z

Элемент | Материал | Почему выбран | Ограничение
интерфейс | Сталь 40Х | Посадка на вал, паз 6×6,
образцы | PA12‑CF10 | Связь расчёта с реальной

## Исполнение М1

PA12‑CF10 + металлическая втулка. Базовый стендовый образец.

## Исполнение М2

М1 + наружное углеродное армирование. Опытная доводка несущей способности.

11. Материалы и технология

# УГЛЕРОДНЫЙ СЛОЙ

+22,2%

расчётный прирост несущей способности армированного участка

≈ +9,5%

теоретический прирост частоты при неизменной схеме нагружения

### Расчёт совмещённого сечения

Karm = 1 + (150 МПа × 0,2 мм) /

### / (45 МПа × 3 мм) = 1,222

Для консервативного проектного вывода в отчёте принят
округлённый коэффициент 1,20.

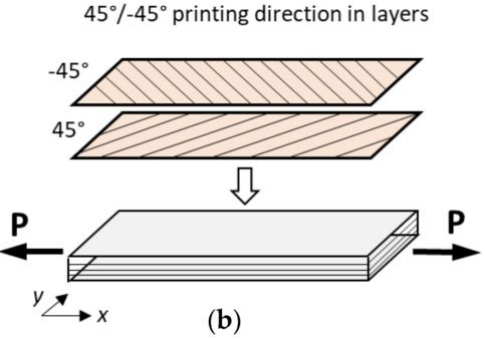
[picture p76: figure]

### Статус показателя

### Проектная расчётная гипотеза. Эффект подтверждается контрольными образцами, адгезионной проверкой и

разгонным испытанием.

12. Экономика

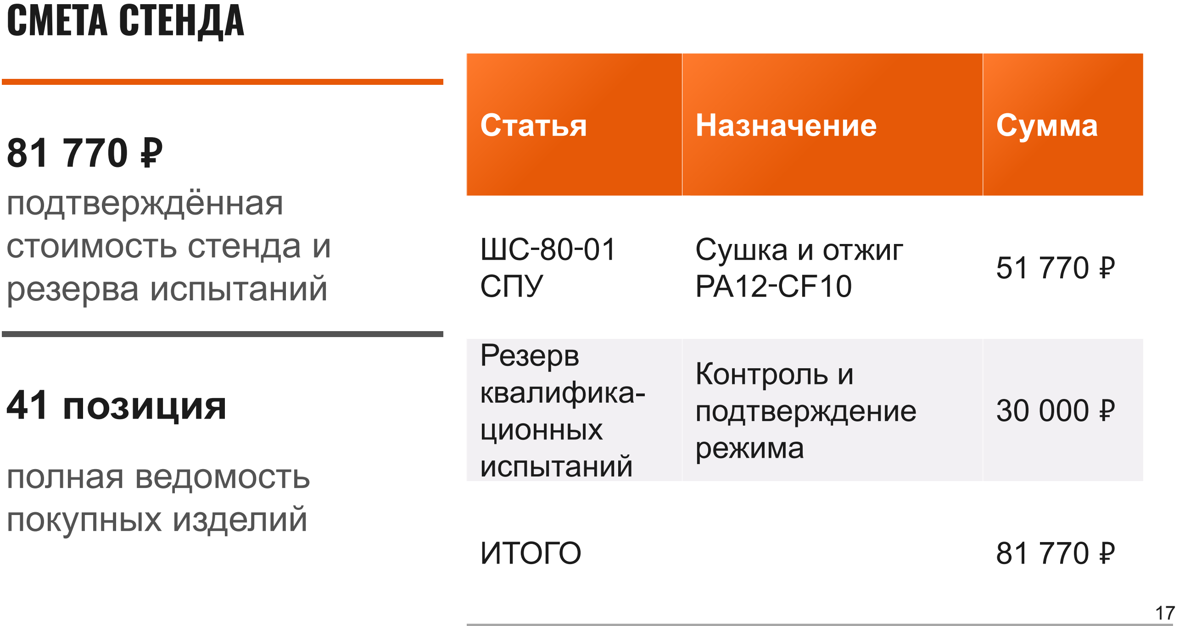
[picture p77: figure]
СМЕТА СТЕНДА; подтверждённая стоимость стенда и резерва испытаний; 41 позиция; полная ведомость покупных изделий; Статья; Назначение; Сумма; ШС‑80‑01 СПУ; Сушка и отжиг PA12‑CF10; Резерв квалифика- ционных испытаний; Контроль и подтверждение режима; ИТОГО

12. Экономика

# ЭКОНОМИКА ПРОЕКТА

Показатель | М1 | М2
Полная себестоимость изделия | 18 105 ₽ | 26 124 ₽
Цена единичного НИОКР‑заказа | 150 000 ₽ | 165 000 ₽
Полные затраты заказа | 58 105 ₽ | 67 324 ₽
Прибыль до налогов | 91 895 ₽ | 97 676 ₽
Маржа | 61,3% | 59,2%

120 → 40 ч

снижение трудоёмкости за
счёт программного
комплекса

88 458 ₽

| себестоимость конкурсной партии: 2×М1 + 2×М2

## 4 заказа

| | управленческий рубеж окупаемости программы

13. Документация

# ОФОРМЛЕНИЕ ЕСКД

## 18 документов

### Этапы оформления

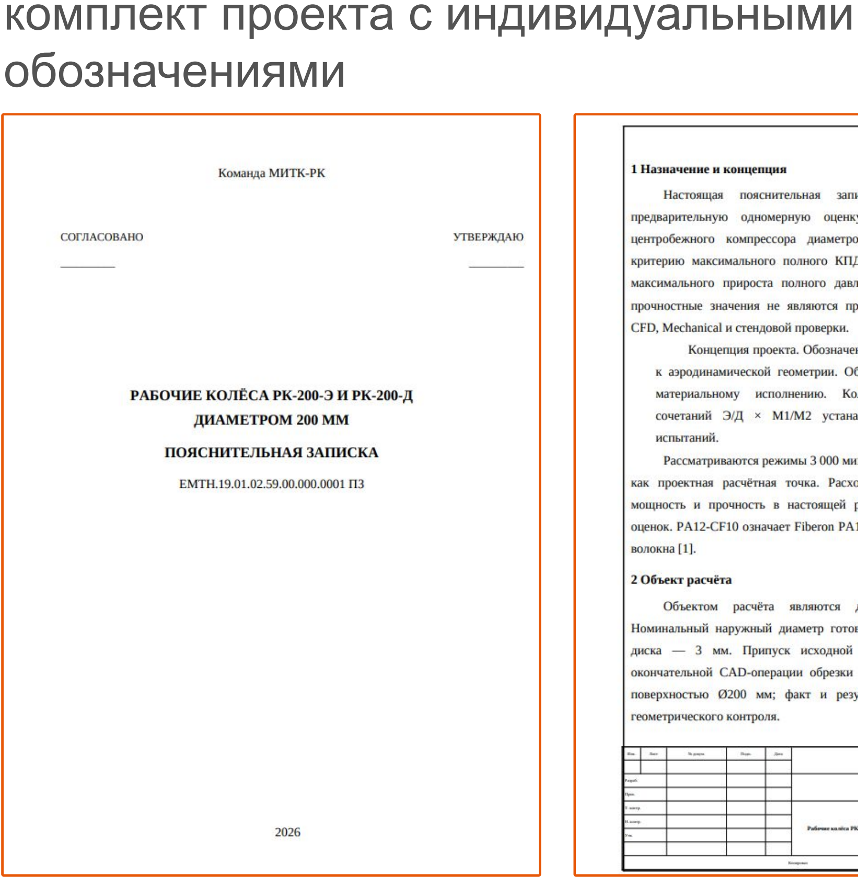
[picture p78: figure]
комплект проекта с индивидуальными обозначениями

### 01 Данные

Название, обозначение и реквизиты

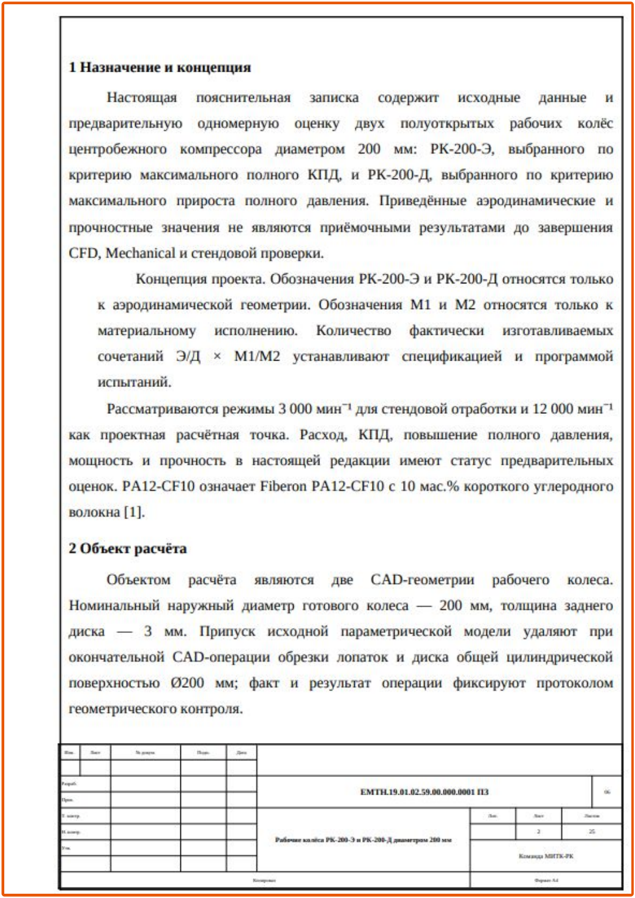
[picture p79: figure]

### 02 Вёрстка

Times New Roman, поля и разделы

### 03 ЕСКД

Рамка, основная надпись, листы

### 04 Экспорт

DOCX и PDF

### 05 QA

Размер страницы, рамка и комплектность

14. Представление проекта

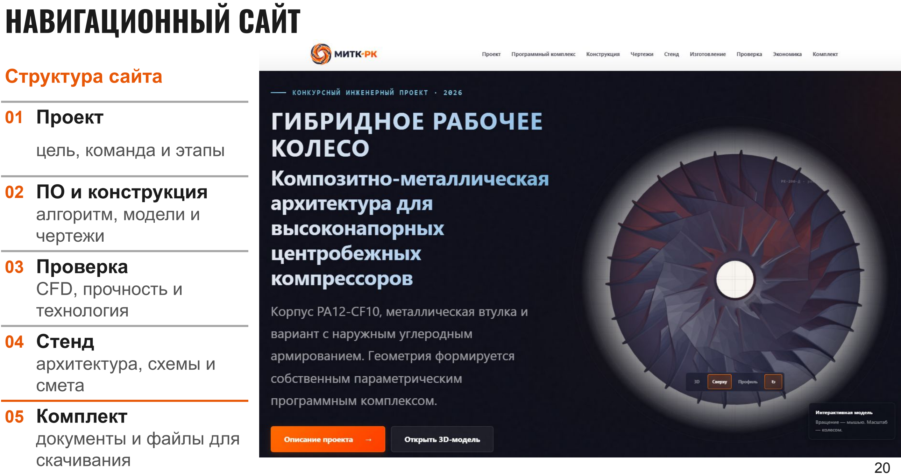
[picture p80: figure]
НАВИГАЦИОННЫЙ САЙТ; Структура сайта; 01 Проект; цель, команда и этапы; 02 ПО и конструкция алгоритм, модели и чертежи; 03 Проверка CFD, прочность и технология; 04 Стенд архитектура, схемы и смета; 05 Комплект документы и файлы для; скачивания

# САЙТ — ЭЛЕКТРОННОЕ ТЕХНИЧЕСКОЕ ДОСЬЕ

### На сайте доступны

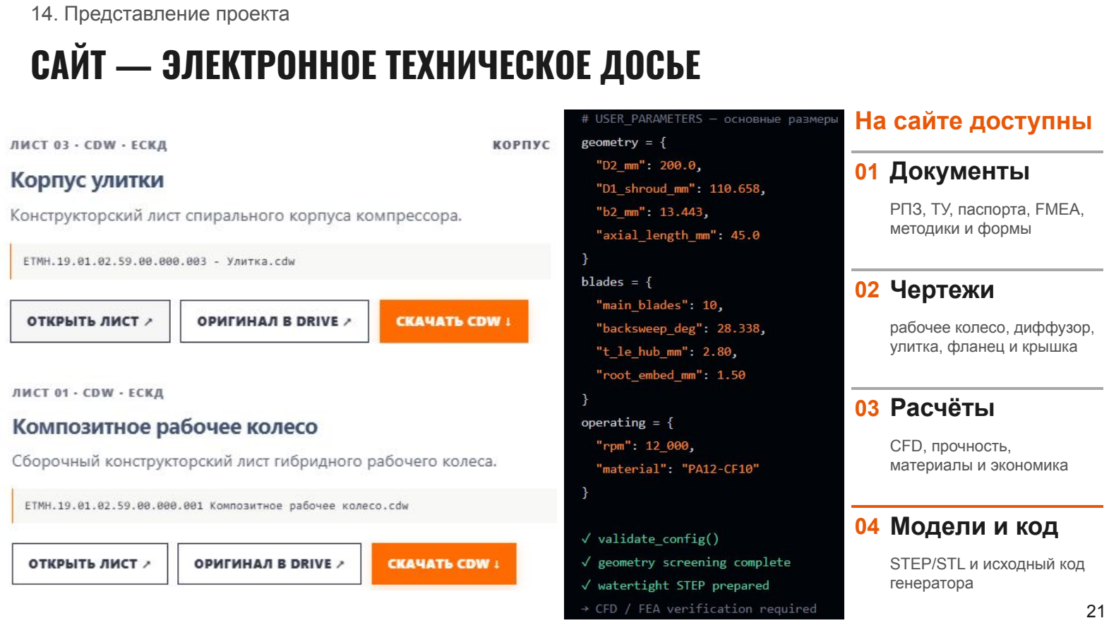
[picture p81: page 21]

14. Представление проекта

### 01 Документы

РПЗ, ТУ, паспорта, FMEA,
методики и формы

### 02 Чертежи

рабочее колесо, диффузор,
улитка, фланец и крышка

### 03 Расчёты

CFD, прочность,
материалы и экономика

### 04 Модели и код

STEP/STL и исходный код
генератора

15. Итоги

# РЕЗУЛЬТАТЫ

### 01 Программный комплекс

### параметрическая генерация, screening и STEP

### 02 Рабочие колёса

### две геометрии и два материальных исполнения

### 03 Расчётная проверка

### CFD, прочность и программа дальнейшей верификации

### 04 Испытательный стенд

конструкция, схемы,

### компоненты и смета

### 05 Технический комплект

18 документов,

### чертежи и электронное досье

Результат

### Команда разработала не отдельную деталь, а связанный процесс: от исходных

параметров до модели, испытания и передачи технического комплекта.

### Сайт МИТК-РК

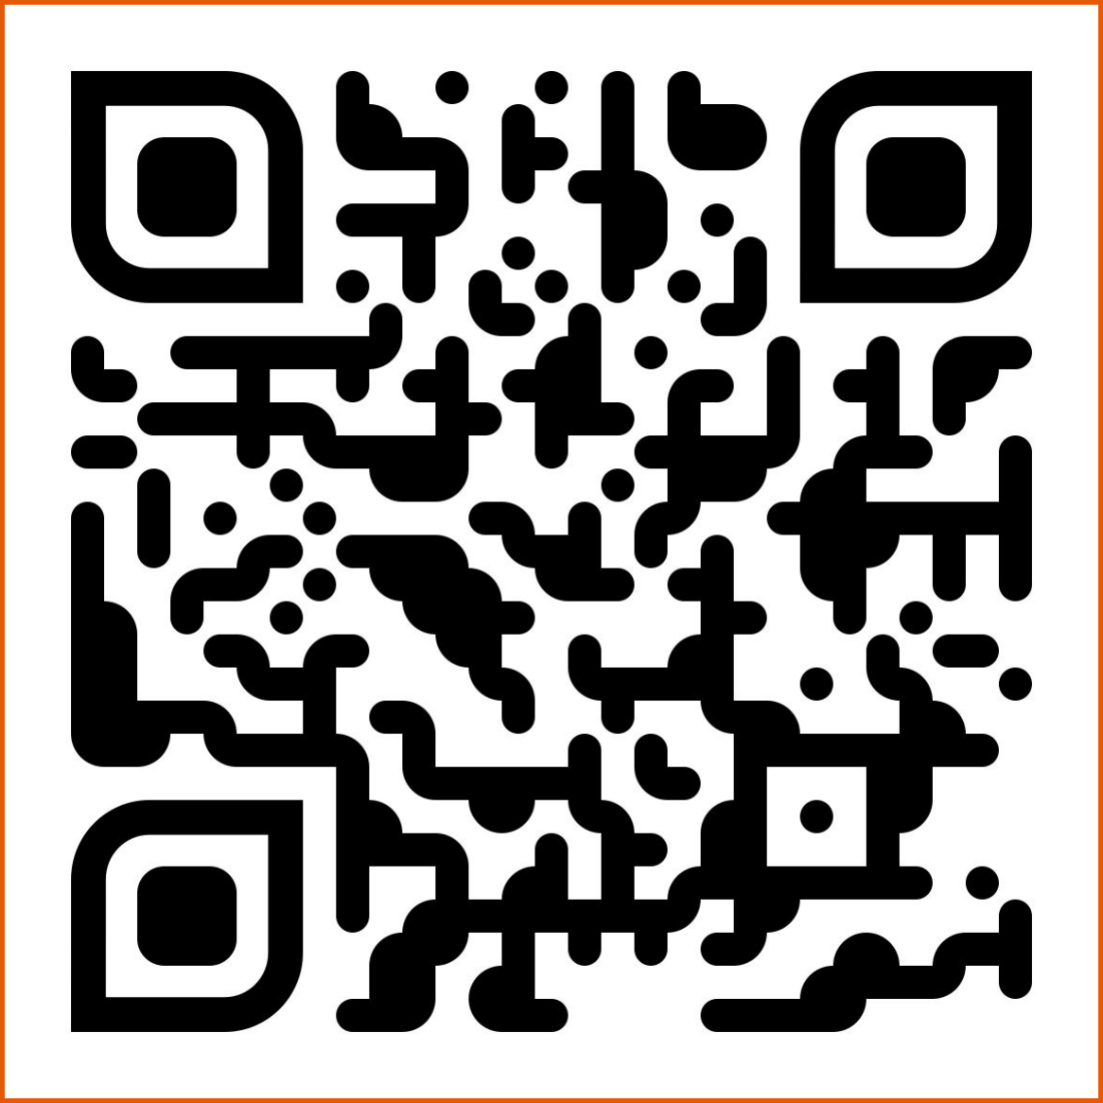
[picture p82: figure]

# Разработчики: Аюпов Камиль Бардашкин Даниил Сивуда Максим Котельников Игорь Фефелов Данил Ягофаров Тимур Ярушин Денис

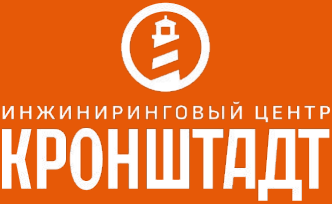
[picture p83: figure]
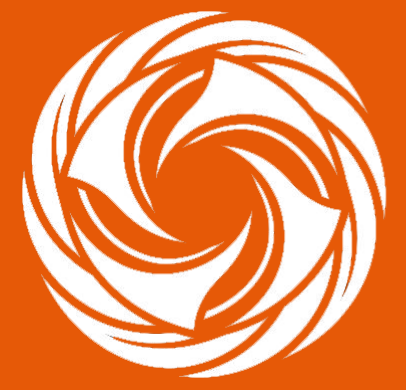
[picture p84: figure]
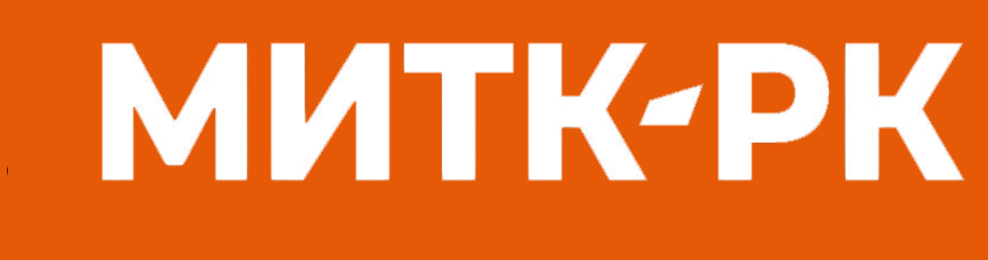
[picture p85: figure]
