IImasterII/mitk-rk-site/documents/0001_pz.pdf

2026

Команда МИТК-РК

СОГЛАСОВАНО

__________

УТВЕРЖДАЮ

__________

РАБОЧИЕ КОЛЁСА РК-200-Э И РК-200-Д ДИАМЕТРОМ 200 ММ

ПОЯСНИТЕЛЬНАЯ ЗАПИСКА

EMTH.19.01.02.59.00.000.0001 ПЗ

Изм. | Лист | № докум. | Подп. | Дата
Разраб. | EMTH.19.01.02.59.00.000.0001 ПЗ | 06

Пров.

Т. контр. | Рабочие колёса РК-200-Э и РК-200-Д диаметром 200 мм | Лит. | Лист | Листов
Н. контр. | | | 2 | 25
Утв. | | Команда МИТК-РК
Копировал | Формат A4

### 1 Назначение и концепция

Настоящая пояснительная записка содержит исходные данные и предварительную одномерную оценку двух полуоткрытых рабочих колёс центробежного компрессора диаметром 200 мм: РК-200-Э, выбранного по критерию максимального полного КПД, и РК-200-Д, выбранного по критерию максимального прироста полного давления. Приведённые аэродинамические и прочностные значения не являются приёмочными результатами до завершения CFD, Mechanical и стендовой проверки.
Концепция проекта. Обозначения РК-200-Э и РК-200-Д относятся только к аэродинамической геометрии. Обозначения М1 и М2 относятся только к материальному исполнению. Количество фактически изготавливаемых сочетаний Э/Д × М1/М2 устанавливают спецификацией и программой испытаний.
Рассматриваются режимы 3 000 мин ¹ для стендовой отработки и 12 000 мин ¹ ⁻ | ⁻
как проектная расчётная точка. Расход, КПД, повышение полного давления, мощность и прочность в настоящей редакции имеют статус предварительных оценок. PA12-CF10 означает Fiberon PA12-CF10 с 10 мас.% короткого углеродного волокна [1].

### 2 Объект расчёта

Объектом расчёта являются две CAD-геометрии рабочего колеса. Номинальный наружный диаметр готового колеса — 200 мм, толщина заднего диска — 3 мм. Припуск исходной параметрической модели удаляют при окончательной CAD-операции обрезки лопаток и диска общей цилиндрической поверхностью Ø200 мм; факт и результат операции фиксируют протоколом геометрического контроля.

EMTH.19.01.02.59.00.000.0001 ПЗ

Вер. | Лист
Изм. | Лист | № докум. | Подп. | Дата

РК-200-Э содержит 10 основных и 10 сплиттерных лопаток; финальная STEP-модель проверена как единое твёрдое тело. РК-200-Д содержит 13 основных и 13 сплиттерных лопаток и является конфигурацией второго печатного колеса. Проточная часть и диффузор относятся к последующему уровню расчёта компрессорной ступени и в настоящую записку не входят.
Гибридная архитектура реализует функциональное разделение: композитная часть формирует диск, ступицу и лопаточный аппарат; металлическая втулка обеспечивает посадку на вал и передачу момента. Материальное исполнение М1 — PA12-CF10 с металлической втулкой; М2 — PA12-CF10 с наружным слоем углеродной ткани в эпоксидной матрице и той же втулкой.

### 3 Система инженерной верификации

Таблица 1

Класс | Статус | Правило применения
И | Исходные данные | Параметр принят в CAD-модели или технологической схеме проекта
Р | Предварительны й расчёт | Значение получено по приведённой формуле либо импортировано из протокола [13]
П | Подтверждение | Значение подтверждено CFD, Mechanical, контролем изготовления или стендом

### 4 Исходные данные

Таблица 2
Параметр | РК-200-Э | РК-200-Д | Класс
Критерий оптимизации | максимум ηtt | максимум Δpt | И
D2, мм | 200 | 200 | И
D1s, мм | 110,658 | 105,075 | И
D1h, мм | 40 | 40 | И
b2, мм | 13,443 | 14,242 | И
Основные + сплиттерные лопатки | 10+10 | 13+13 | И
Угол назад от радиального, ° | 28,338 | 5,000 | И
β2 от касательной, ° | 61,662 | 85,000 | И
Начало сплиттера, доля длины | 0,350 | 0,350 | И
Смещение сплиттера, доля шага | 0,550 | 0,573 | И

Параметр | РК-200-Э | РК-200-Д | Класс
Задний диск, мм | 3 | 3 | И
Режимы, мин ¹⁻ | 3 000; 12 000 | 3 000; 12 000 | И

Таблица 3
Исполнение | Общая конструктивная база
М1 | PA12-CF10 + металлическая втулка
М2 | PA12-CF10 + углеродная ткань 0,2 мм/эпоксидная матрица + металлическая втулка
Втулка | Сталь 40Х; H = 49,5 мм; Ø30/Ø22 мм; сквозной паз 6×6 мм; запрессовка, накатка, клей

### 5 Допущения одномерного расчёта

1) рабочая среда — сухой воздух как идеальный газ при p01 = 101 325 Па и T01 = 293,15 К;
2) R = 287,05 Дж/(кг·К), γ = 1,4, cp = 1005 Дж/(кг·К), динамическая вязкость μ = 1,81·10 ⁵ Па·с; ⁻
3) на входе отсутствует предварительная закрутка: Cu1 = 0;
4) поток | на | расчётной | линии | считается | стационарным | и
осесимметричным;
5) коэффициент расхода φ2, коэффициент скольжения σ, открытая доля выхода kA2 и полный КПД ηtt рассчитываются отдельно для каждой геометрии;
6) механический КПД передачи ηm = 0,95 принят для определения мощности и момента.

Таблица 4
Модель | φ2, вход [13] | σ, вход [13] | kA2, вход [13] | ηtt, %, оценка [13]
РК-200-Э | 0,2169 | 0,8591 | 0,8800 | 74,14
РК-200-Д | 0,2093 | 0,8752 | 0,8800 | 71,23

Статус расчёта. Значения φ2, σ, kA2 и ηtt перенесены из внутренней программы [13]. До приложения версии программы, входного файла, диапазонов оптимизации, формул и машинного протокола они считаются исходными предположениями, а не независимо воспроизводимыми результатами. Сравнительный вывод подлежит подтверждению CFD и стендом [5], [6].

### 6 Геометрические параметры проточной части колеса

r2=

D2
2

(1)

где r2 — наружный радиус, м; D2 — наружный диаметр, м. Подстановка: r2 = 0,200 / 2
Результат. r2 = 0,100 м.

A1=

π ( D1 s
2 − D1h

2

)
4

(2)

где A1 — геометрическая площадь кольцевого входа, м². Подстановка: для РК-200-Э: A1 = π(0,110658² - 0,040²) / 4
Результат. A1 = 0,008361 м².
A2=2 π r2 b2 | (3)
где A2 — геометрическая площадь цилиндрического выхода колеса, м². Подстановка: для РК-200-Э: A2 = 2π·0,100·0,013443
Результат. A2 = 0,008447 м².
A2, e f f =k A 2 A2 | (4)
где A2,eff — эффективная площадь выхода; kA2 — коэффициент блокировки. Подстановка: A2,eff = 0,880·0,008447
Результат. A2,eff = 0,007433 м².

Таблица 5
Модель | A1, м² | A2, м² | A2,eff, м² | Мин. проход CAD, мм*
РК-200-Э | 0,008361 | 0,008447 | 0,007433 | 10,692
РК-200-Д | 0,007415 | 0,008949 | 0,007875 | 7,142

Для РК-200-Э заявлен STEP-контроль наружного диаметра, толщины диска, единого твёрдого тела и периодичности 10+10 лопаток [11]. К записке следует приложить протокол измерений с именем и контрольной суммой файла. Для РК-200-Д аналогичный протокол обязателен до передачи модели в производство [12]. Значения минимального прохода подтверждают сечением CAD с указанием положения измерения.

### 7 Кинематика вращения

ω=

2 π n
60 | (5)

где ω — угловая скорость, рад/с; n — частота вращения, мин ¹. ⁻ Подстановка: для 12 000 мин ¹: ω = 2π·12 000 / 60 ⁻
Результат. ω = 1256,637 рад/с.

U2=ωr2=

π D2 n
60 | (6)

где U2 — окружная скорость наружной кромки, м/с. Подстановка: U2 = π·0,200·12 000 / 60
Результат. U2 = 125,664 м/с.

ar=ω

2
r2 | (7)
где ar — центростремительное ускорение на наружном радиусе, м/с². Подстановка: ar = 1256,637²·0,100
Результат. ar/g = 16103.
a=√γ RT01 | (8)
где a — скорость звука во входных условиях, м/с. Подстановка: a = √(1,4·287,05·293,15) Результат. a = 343,232 м/с.

Mt i p=

U2
a

(9)

где Mtip — окружное число Маха. Подстановка: Mtip = 125,664 / 343,232 Результат. Mtip = 0,366.

Таблица 6
n, мин ¹⁻ | ω, рад/с | U2, м/с | Mtip | ar/g
3000 | 314,159 | 31,416 | 0,092 | 1006
12000 | 1256,637 | 125,664 | 0,366 | 16103

### 8 Входной треугольник скоростей

ρ01=

p01
RT01

(10)

где ρ01 — плотность воздуха во входных условиях, кг/м³. Подстановка: ρ01 = 101 325 / (287,05·293,15)
Результат. ρ01 = 1,204 кг/м³.

Cm1=

m˙

ρ01 k A 1 A1

(11)

где Cm1 — средняя меридиональная скорость на входе; kA1 = 0,95. Подстановка: для 12 000 мин ¹: Cm1 = 0,250/(1,204·0,95·0,008361) ⁻ Результат. Cm1 = 26,200 м/с.

W1=√Cm1
2
+U1

2
(12)
где W1 — относительная скорость при Cu1 = 0. Подстановка: по покрывающей: W1s = √(26,200² + 69,528²) Результат. W1s = 74,301 м/с; Mrel,1s = 0,216.

β1, f l ow =arctan(
Cm1
U1 ) | (13)

где β1,flow — угол относительного потока от касательного направления. Подстановка: β1s = arctan(26,200/69,528); β1h = arctan(26,200/25,133) Результат. β1s = 20,647°; β1h = 46,191°.

Таблица 7
Модель | n | Cm1 | U1s | W1s | Mrel,1s | β1s | β1h
РК-200-Э | 3000 | 6,387 | 17,382 | 18,518 | 0,054 | 20,176 | 45,469
РК-200-Э | 12000 | 26,200 | 69,528 | 74,301 | 0,216 | 20,647 | 46,191
РК-200-Д | 3000 | 7,361 | 16,505 | 18,072 | 0,053 | 24,036 | 49,517
РК-200-Д | 12000 | 30,039 | 66,021 | 72,533 | 0,211 | 24,465 | 50,082

Интерпретация. Полученные β1s и β1h задают расчётное направление относительного потока. Их сопоставление с контрольными сечениями CAD и полем скоростей CFD является частью аэродинамической верификации профиля.

### 9 Расход через колесо

Cm2=φ2U2 | (14)
где Cm2 — меридиональная скорость на выходе; φ2 рассчитывается для каждой геометрии.
Подстановка: для РК-200-Э: Cm2 = 0,2169·125,664
Результат. Cm2 = 27,255 м/с.
A2, e f f =k A 2 2 π r2 b2 | (15)
где A2,eff — эффективная площадь цилиндрического выхода. Подстановка: для РК-200-Э: A2,eff = 0,8800·2π·0,100·0,013443
Результат. A2,eff = 0,007433 м².
m˙ = ρ2 A2, e f f Cm2 | (16)
где ρ2 — статическая плотность на выходе. Для воспроизводимого расчёта должны быть приведены уравнения связи p2, T2, C2 и ρ2, порядок итерации и критерий сходимости [3], [4].
Подстановка: для РК-200-Э при 12 000 мин ¹: ṁ = ρ2·0,007433·27,255. В ⁻ текущем наборе данных ρ2 отдельно не приведена, поэтому результат не воспроизводится независимо от программы [13].
Результат. ṁ = 0,250 кг/с; Q01 = 0,207 м³/с.

Таблица 8
Модель | n, мин ¹⁻ | Cm2, м/с | Q01, м³/с | ṁ, кг/с
РК-200-Э | 3000 | 6,814 | 0,051 | 0,061
РК-200-Э | 12000 | 27,255 | 0,207 | 0,250
РК-200-Д | 3000 | 6,576 | 0,052 | 0,062
РК-200-Д | 12000 | 26,305 | 0,211 | 0,254

Приведённый расход является предварительной расчётной точкой, зависящей от φ2, kA2 и замыкания по ρ2. Использовать его как производительность изделия допускается только после приложения протокола расчёта и построения характеристики CFD или стенда.

### 10 Удельная работа и повышение давления

Δh0 , E =U2Cu2−U1Cu1 | (17)
где Δh0,E — работа Эйлера на единицу массы; Cu — окружная составляющая абсолютной скорости.
При отсутствии предварительной закрутки Cu1 = 0. Для выходного треугольника с учётом конечного числа лопаток используется коэффициент скольжения.

Cu2=σ U2−Cm2

cot β2 | (18)
где σ — коэффициент скольжения; β2 — угол лопатки от касательной. Подстановка: для РК-200-Э: Cu2 = 0,8591·125,664 - 27,255·cot61,662° Результат. Cu2 = 93,255 м/с.
Δh0=U2Cu2 | (19)
где Δh0 — расчётная удельная работа колеса, Дж/кг.
Подстановка: Δh0 = 125,664·93,255
Результат. Δh0 = 11,719 кДж/кг.

ΔT0=

Δh0
c p

(20)

где ΔT0 — повышение полной температуры, К. Подстановка: ΔT0 = 11718,743/1005 Результат. ΔT0 = 11,664 К.

πt t =[
1+

ηt t Δh0

c pT01 )

γ
γ −1
(21)

где πtt — отношение полных давлений; ηtt — расчётный полный КПД. Подстановка: для РК-200-Э: πtt = [1 + 0,7414·11718,743/(1005·293,15)]^(1,4/0,4) [3], [4]

Результат. πtt = 1,1071.

Δ pt = p01 ( πt t−1) | (22)
где Δpt — прирост полного давления, Па. Подстановка: Δpt = 101 325·(1,1071 - 1)
Результат. Δpt = 10,853 кПа.

Таблица 9
Модель | n | η tt, % | Δh0, кДж/кг | πtt | Δp t, кПа, оценка | p02, кПа abs
РК-200-Э | 3000 | — | 0,732 | 1,0065 | 0,655 | 101,980
РК-200-Э | 12000 | 74,14 | 11,719 | 1,1071 | 10,853 | 112,178
РК-200-Д | 3000 | — | 0,846 | 1,0072 | 0,727 | 102,052
РК-200-Д | 12000 | 71,23 | 13,532 | 1,1193 | 12,089 | 113,414

Предварительная оценка. При 12 000 мин ¹ расчёт [13] прогнозирует для ⁻ РК-200-Э ηtt ≈ 74 % и Δpt ≈ 10,9 кПа, для РК-200-Д — ηtt ≈ 71 % и Δpt ≈ 12,1 кПа. Значения при 3 000 мин ¹ получены масштабированием и не ⁻ подтверждают сохранение КПД при изменении числа Рейнольдса.

### 11 Мощность и крутящий момент

Pf l ui d =m˙ Δh0 | (23)
где Pfluid — мощность, переданная воздуху, Вт. Подстановка: Pfluid = 0,250·11718,743 Результат. Pfluid = 2,928 кВт.

Ps h a f t =

Pf l ui d
ηm

(24)

где Pshaft — оценка мощности на валу; ηm = 0,95. Подстановка: Pshaft = 2,928/0,95
Результат. Pshaft = 3,082 кВт.

Ms h a f t =

Ps h a f t
ω

(25)

где Mshaft — крутящий момент, Н·м.

Подстановка: Mshaft = 3081,913/1256,637
Результат. Mshaft = 2,453 Н·м.

Таблица 10
Модель | n, мин ¹⁻ | Pfluid, кВт | Pshaft, кВт | Mshaft, Н·м
РК-200-Э | 3000 | 0,045 | 0,047 | 0,150
РК-200-Э | 12000 | 2,928 | 3,082 | 2,453
РК-200-Д | 3000 | 0,053 | 0,056 | 0,177
РК-200-Д | 12000 | 3,435 | 3,615 | 2,877

На основном режиме РК-200-Э требует около 3,082 кВт и 2,453 Н·м; РК-200-Д — 3,615 кВт и 2,877 Н·м. Для привода и втулки определяющим является вариант максимального давления.

### 12 Законы подобия и интерпретация стенда

Q2
Q1

≈

n2
n1

(26)

где для геометрически подобной машины и сопоставимых коэффициентов режима.

Δ p2
Δ p1

≈(
n2

n1 )

2
(27)

где приближённый закон изменения давления.

P2
P1

≈(
n2

n1 )

3
(28)

где приближённый закон изменения мощности.
Переход от 3 000 к 12 000 мин ¹ означает увеличение частоты в 4 раза. Законы ⁻ подобия дают только первое приближение: Q ~ n, Δp ~ n², P ~ n³. Из-за изменения числа Рейнольдса, утечек, зазоров и шероховатости печати нельзя переносить КПД между режимами без отдельного расчёта или испытания.
Роль стенда. Режим 3 000 мин ¹ демонстрирует устойчивое вращение, ⁻ балансируемость и измеримый компрессорный эффект. Режим 12 000 мин ¹⁻

является основной расчётной точкой архитектуры и верифицируется полной связкой CFD и Mechanical.

### 13 Числа Маха и Рейнольдса

R eb 2=

ρ2Cm2 b2
μ

(29)

где Reb2 — число Рейнольдса по ширине выхода.
Подстановка: для РК-200-Э: Reb2 = ρ2·27,255·0,013443/(1,81·10 ⁵) ⁻ Результат. Reb2 = 24964.

Таблица 11
Модель | n, мин ¹⁻ | Mtip | Mrel,1s | Reb2
РК-200-Э | 3000 | 0,092 | 0,054 | 6103
РК-200-Э | 12000 | 0,366 | 0,216 | 24964
РК-200-Д | 3000 | 0,092 | 0,053 | 6237
РК-200-Д | 12000 | 0,366 | 0,211 | 25361

При 12 000 мин ¹ окружное число Маха составляет около 0,366; течение на ⁻ наружном диаметре остаётся дозвуковым. На стендовом режиме относительное влияние вязкости и шероховатости выше, что учитывается при сопоставлении результатов.

### 14 Чувствительность оценки давления

Таблица 12
Модель | Сценарий | σ | ηtt, % | πtt | Δpt, кПа
РК-200-Э | Нижняя оценка σ | 0,809 | 74,1 | 1,0997 | 10,097
РК-200-Э | Базовая | 0,859 | 74,1 | 1,1071 | 10,853
РК-200-Э | Верхняя оценка σ | 0,909 | 74,1 | 1,1146 | 11,613
РК-200-Э | Нижняя оценка ηtt | 0,859 | 68,1 | 1,0982 | 9,945
РК-200-Э | Верхняя оценка ηtt | 0,859 | 78,1 | 1,1131 | 11,461
РК-200-Д | Нижняя оценка σ | 0,825 | 71,2 | 1,1121 | 11,357
РК-200-Д | Базовая | 0,875 | 71,2 | 1,1193 | 12,089
РК-200-Д | Верхняя оценка σ | 0,925 | 71,2 | 1,1266 | 12,825
РК-200-Д | Нижняя оценка ηtt | 0,875 | 65,2 | 1,1089 | 11,033
РК-200-Д | Верхняя оценка ηtt | 0,875 | 75,2 | 1,1263 | 12,797

Чувствительность приведена для обеих моделей при 12 000 мин ¹. Основными ⁻ значениями для сравнения являются базовые строки; диапазоны показывают влияние неопределённости коэффициента скольжения и полного КПД до CFD-верификации.

### 15 Аналитическая оценка прочности при вращении

Ниже приведена скрининговая оценка характерного уровня центробежных напряжений. Формула изотропного кольца/диска не описывает анизотропию FFF, корни лопаток, ступицу, отверстие, натяг втулки, дефекты, ползучесть, усталость и влияние влаги. Она не является расчётом допуска к вращению.

σc al c=max {
ρ ω

2

((3+ ν )r2
2
+(1−ν )rb

2

)
4
1
2

ρ Kt ω

2

(r2
2−rh

2

) )
(30)

где ρ = 1060 кг/м³; ν = 0,35 и Kt = 2,0 — принятые для скрининга величины; rb и rh должны быть определены по CAD. До обоснования геометрии и Kt результат имеет только справочный статус.
Подстановка: при 12 000 мин ¹: σcalc = max(14,080; 16,069) ⁻
Результат. σcalc = 16,069 МПа.

Ss c r e e n=

Rall ow

σc al c

(31)

где Sscreen — отношение типового значения прочности TDS к скрининговому напряжению; это не допускаемый коэффициент запаса.
Подстановка: для типового значения wet Z из TDS: Sscreen = 42,1/16,069 [1] Результат. Sscreen = 2,620; для допуска к эксплуатации не применять.

Таблица 13
n | σ, МПа | S dry XY | S dry Z | S wet XY | S wet Z
3000 | 1,004 | 77,066 | 51,975 | 71,391 | 41,918
12000 | 16,069 | 4,817 | 3,248 | 4,462 | 2,620

Fb=mbω

2
r c | (32)
где Fb — центробежная сила одной лопатки; mb и rc должны быть взяты из CAD.
Прочностной вывод. Скрининговая модель даёт 16,1 МПа и отношение Sscreen = 2,62 к типовому значению wet Z. TDS запрещает использовать типовые значения как проектную спецификацию [1]. Допуск к вращению оформляют только после Mechanical с ортотропией и испытаний образцов одной партии; балансировка и защитный кожух обязательны.

### 16 Частоты возбуждения и балансировка

f

1×=

n
60 | (33)

где f1× — частота вращательного возбуждения, Гц.

f B P F =

z n
60 | (34)

где fBPF — частота прохождения венца; z принимается отдельно для основных лопаток и полного числа элементов.

Таблица 14
Модель | n, мин ¹⁻ | 1×, Гц | Основной венец, Гц | Все элементы, Гц
РК-200-Э | 3000 | 50 | 500 | 1000
РК-200-Э | 12000 | 200 | 2000 | 4000
РК-200-Д | 3000 | 50 | 650 | 1300
РК-200-Д | 12000 | 200 | 2600 | 5200

Для РК-200-Э контролируются порядки 10× и 20×, для РК-200-Д — 13× и 26×, а также их гармоники. Класс балансировки и допустимый остаточный дисбаланс назначаются после определения массы, рабочих опор и требований ISO 21940-11.

### 17 Композит PA12-CF10

Матрицей обоих исполнений является Fiberon PA12-CF10 — материал для FFF с 10 мас.% короткого углеродного волокна [1], [2]. Значения TDS являются типовыми справочными данными; расчётные допускаемые характеристики назначают по результатам испытаний образцов той же партии, напечатанных и кондиционированных вместе с колесом.

Таблица 15
Свойство | Типовое значение TDS [1] | Метод | Примечание
Плотность | 1,06 г/см³ | ISO 1183 | Физическое свойство
Модуль Юнга dry XY | 3311,2 ± 134,9 МПа | ISO 527 | После отжига
Модуль Юнга dry Z | 1806,6 ± 145,7 МПа | ISO 527 | После отжига
Прочность dry XY | 77,4 ± 1,1 МПа | ISO 527 | После отжига
Прочность dry Z | 52,2 ± 0,8 МПа | ISO 527 | После отжига
Прочность wet XY | 71,7 ± 0,7 МПа | ISO 527 | TDS: после отжига и кондиционирования
Прочность wet Z | 42,1 ± 1,8 МПа | ISO 527 | Типовое; не допускаемое значение
HDT при 0,45 МПа | 131 °C | ISO 75 | Температурная характеристика
HDT при 1,8 МПа | 105 °C | ISO 75 | Температурная характеристика
Равновесное водопоглощение | около 1,5 % | TDS | Контролировать кондиционирование

### 18 Технология печати PA12-CF10

Таблица 16

Параметр | Требование | Инженерное пояснение
Температура сопла | 280–300 °C | Официальный диапазон; профиль квалифицировать
Температура стола | 40–50 °C | Официальный диапазон
Камера | комнатная температура допускается производителем | Для детали Ø200 обеспечить стабильную среду
Обдув | выключен | По TDS
Сушка перед печатью | 100 °C, 10 ч | Хранить и печатать при RH менее 20 %
Отжиг | 100 °C, 16 ч | После отжига повторно измерить геометрию
Сопло | износостойкое | Закалённая сталь или рубин; латунь быстро изнашивается
Заполнение | 100 % для опытного ротора | Единый плотный силовой объём
Скорость печати | 60 мм/с, базовый профиль проекта | Стабильность экструзии приоритетна
Диаметр сопла | 0,4 мм | Износостойкое сопло
Высота слоя | 0,2 мм | Фиксировать в журнале печати

Параметр | Требование | Инженерное пояснение
Ширина линии | 0,4 мм | Фиксировать в журнале печати
Поддержки | не применять | Подтвердить контрольной нарезкой

Предпочтительная базовая ориентация — ось колеса перпендикулярна столу, диск лежит в плоскости XY. Тогда основные мембранные напряжения диска воспринимаются более прочным направлением XY. При этом корни лопаток и межслойное направление Z остаются критическими и должны быть проверены отдельно.
Для каждой печати регистрируют: производителя и партию, массу и состояние катушки, режим сушки, принтер, сопло и его наработку, высоту слоя, ширину экструзии, число периметров, заполнение, температуры, скорости, обдув, паузы, дефекты, параметры отжига, массу детали и результаты геометрического контроля.
— напечатать вместе с колесом контрольные образцы XY и Z из той же партии и тем же профилем;
— выполнить отжиг до окончательного контроля диаметра и биения;
— после отжига подтвердить готовый наружный диаметр 200 мм и отсутствие коробления;
— любую локальную обработку корней лопаток регистрировать в маршрутной карте;
— до вращения выполнить визуальный контроль, контроль массы, биения и балансировку.

### 19 Исполнение РК-200-М2 с наружным армированием

Материальное исполнение М2 предполагает сердечник PA12-CF10 и наружный слой углеродной ткани в эпоксидной матрице. Толщина 0,2 мм относится к сухой ткани и не задаёт толщину отверждённого ламината. Марка ткани, поверхностная плотность, система смолы и цикл отверждения в текущей редакции не назначены.

Предполагаемый эффект наружного слоя подлежит расчёту и испытанию. До разработки карты укладки нельзя утверждать усиление корней лопаток или распределение нагрузки. Необходимо определить доступные поверхности, раскрой, направления волокон, нахлёсты, баланс масс, подготовку PA12-CF10 и критерии качества интерфейса [7], [8].

ml am = Al am ( μf + μr) | (35)
где mlam — добавленная масса; Alam — площадь укладки; μf и μr — поверхностные массы сухой ткани и отверждённой смолы.

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
(36)

где Ni — доля мембранной нагрузки слоя i при совместной деформации; E и t — модуль и толщина слоя.
В Mechanical сердечник моделируют объёмными элементами, ткань — ортотропными оболочками, интерфейс — контактной или когезионной моделью по подтверждённым данным. Способ обеспечения Ø200 мм после отверждения, допустимость механической обработки и контроль аэродинамического профиля должны быть заданы технологической документацией.

Таблица 17
Параметр | Что определить | Статус
Материал ткани | углеродная ткань, сухая толщина 0,2 мм | Требует задания и подтверждения
Эпоксидная система | структурная смола с контролируемым циклом отверждения | Требует задания и подтверждения
Карта укладки | диск, ступица, переходы и доступные поверхности лопаток | Требует задания и подтверждения
Симметрия | равная масса и одинаковое направление секторов | Требует задания и подтверждения
Адгезия | подготовка PA12-CF10, пропитка и прикатка | Требует задания и подтверждения
Геометрия | готовый D2 = 200 мм с учётом отверждённого слоя | Требует задания и подтверждения
Качество слоя | сплошность, отсутствие складок и воздушных включений | Требует задания и подтверждения

Статус М2: проектное предложение. Его применение допускается после выпуска спецификации материалов, карты укладки, технологического образца, контроля адгезии, расчёта и балансировки. До этого подтверждённой базой остаётся только геометрия сердечника М1.

### 20 Металлическая посадочная втулка

Предусмотрена втулка из стали 40Х высотой 49,5 мм, Ø30/Ø22 мм со сквозным шпоночным пазом 6×6 мм [10]. До выпуска чертежа необходимо назначить длину шпонки, посадку и допуски, шероховатость, параметры накатки, марку клея, подготовку поверхности и осевую фиксацию. Высоту 49,5 мм сверяют с осевым габаритом финальной CAD-модели.
При диаметре ступицы 40 мм вокруг втулки сохраняется радиальная толщина PA12-CF10 5 мм. Номинальная металлическая стенка втулки без учёта шпоночного паза составляет 4 мм. Втулка расположена близко к оси, поэтому её вклад в центробежную нагрузку наружного венца ограничен.

t

s=

D−d
2

(37)

где ts — номинальная радиальная толщина металлической втулки; D = 30 мм; d = 22 мм.
Подстановка: ts = (30 - 22)/2
Результат. ts = 4 мм без учёта зоны шпоночного паза.
Md e si g n=k M Ms h a f t ,ma x | (38)
где Mdesign — проектный момент; kM = 2 — коэффициент пуска и динамики; Mshaft,max выбирается из двух геометрий.
Подстановка: Mdesign = 2·2,877
Результат. Mdesign = 5,754 Н·м; определяет РК-200-Д.

τ a v g=

2 Md e si g n
π D

2
L

(39)

где D = 0,030 м — наружный диаметр втулки; L = 0,0495 м — длина цилиндрического интерфейса.
Подстановка: τavg = 2·5,754/(π·0,030²·0,0495)

Результат. τavg = 0,082 МПа.
τavg характеризует только среднее напряжение условного цилиндрического интерфейса и не подтверждает соединение. Требуются расчёты шпонки на срез и смятие, втулки по ослабленному сечению, натяга и кольцевых напряжений PA12-CF10, контактного давления, пиковых напряжений клея и осевого удержания [8], [10].

### 21 Программа расчёта ANSYS CFD

— выполнить отдельные расчёты РК-200-Э и РК-200-Д при одинаковых граничных условиях;
— использовать финальные геометрии D2 = 200 мм после SolidWorks-обрезки; — построить расчётные области входа, колеса, зазора, безлопаточного/лопаточного диффузора и выхода;
— выполнить расчёты на 3 000 и 12 000 мин ¹ по нескольким значениям ⁻ массового расхода;
— получить характеристику давления и КПД серией расчётных точек по массовому расходу;
— контролировать y+, сеточную сходимость и независимость от длины входа/выхода;
— вывести полные и статические давления, температуру, момент, массовый расход, КПД, Мах, зоны отрыва и энтропию;
— отдельно оценить влияние сплиттеров, радиального зазора и шероховатости печати;
— сопоставить момент CFD с формулой Эйлера и сформировать итоговую характеристику колеса.

### 22 Программа расчёта ANSYS Mechanical

— импортировать обе финальные геометрии без дефектов и нулевых толщин;
— задать ортотропные или экспериментально эквивалентные свойства PA12-CF10 для XY/Z и dry/wet;

— смоделировать металлическую втулку Ø30/Ø22, запрессовку, накатку и клеевой контакт;
— приложить вращение 3 000 и 12 000 мин ¹ с последовательным нагружением; ⁻ — проверить максимальные главные, эквивалентные и межслойные напряжения, особенно в корне основных лопаток;
— выполнить исследование сеточной сходимости в корнях и у отверстия;
— выполнить модальный анализ с учётом предварительного напряжения;
— сопоставить собственные частоты РК-200-Э с 1×, 10×, 20×, а РК-200-Д — с 1×, 13×, 26× и гармониками;
— для исполнения РК-200-М2 применить ортотропные оболочки и модель клеевого интерфейса;
— оформить таблицу коэффициентов запаса по выбранному критерию разрушения.

### 23 План стендовой валидации

Таблица 18
Этап | Измерения | Условие
Входной контроль | масса, D2, биение, лопатки, дефекты | До установки
Балансировка | остаточный дисбаланс и плоскости коррекции | До вращения
Холостой разгон | 500–3 000 мин ¹ ступенями ⁻ | В защитном кожухе
Аэродинамика | p01, p02, статические давления, T, расход | Стабилизированные точки
Вибрация | 1×, гармоники, тренд | Непрерывная запись
Останов | выбег, осмотр, повторное биение | После каждого режима

Ориентировочный прирост давления на 3 000 мин ¹ составляет около 0,66– ⁻ 0,73 кПа. Диапазон и класс точности датчика выбирают по требуемой неопределённости. До испытаний устанавливают поверку, частоту регистрации, число повторов, критерии стабилизации и аварийные пределы вибрации, температуры и биения.

### 24 Сводные результаты

Таблица 19
Предварительная оценка при 12 000 мин ¹⁻ | РК-200-Э | РК-200-Д | Сравнение
Критерий | максимум КПД | максимум давления | —
ηtt, % | ≈74 | ≈71 | Э: +2,91 п.п.
Δh0, кДж/кг | 11,719 | 13,532 | 15,5 % у Д
Δpt, кПа | 10,853 | 12,089 | 11,4 % у Д
πtt | 1,1071 | 1,1193 | —
p02, кПа abs | 112,178 | 113,414 | —
ṁ, кг/с | 0,250 | 0,254 | —
Pshaft, кВт | 3,082 | 3,615 | выше у Д
Mshaft, Н·м | 2,453 | 2,877 | определяет Д
Мин. проход CAD, мм* | 10,692 | 7,142 | больше у Э
σcalc, МПа | 16,069 | 16,069 | одинаковая база
Sscreen wet Z (не допуск) | 2,620 | 2,620 | одинаковая база

Таблица 20
Оценка при 3 000 мин ¹⁻ | РК-200-Э | РК-200-Д
ηtt, % | не определён | не определён
Δpt, кПа | ≈0,66 | ≈0,73
ṁ, кг/с | 0,061 | 0,062
Pshaft, Вт | 47,086 | 55,570
Mshaft, Н·м | 0,150 | 0,177

Предварительное сравнение по программе [13] указывает на преимущество РК-200-Э по расчётному КПД и РК-200-Д по расчётному давлению. Разность не считается подтверждённой до расчёта обеих моделей при одинаковых граничных условиях и повторяемых стендовых испытаний.

### 25 Итоговое заключение

При одинаковых D2=200 мм и n=12 000 мин ¹ одномерная программа [13] ⁻ прогнозирует для РК-200-Э ηtt≈74 %, πtt≈1,107 и Δpt≈10,9 кПа, для РК-200-Д —

ηtt≈71 %, πtt≈1,119 и Δpt≈12,1 кПа. Это расчётная гипотеза, а не паспортная характеристика.
На режиме 3 000 мин ¹ масштабированная оценка даёт Δpt≈0,66 кПа для ⁻ РК-200-Э и ≈0,73 кПа для РК-200-Д. Фактические значения и КПД определяют
стендовым | испытанием; | состав | изготовленных | образцов | устанавливают
спецификацией.
Скрининговая кольцевая модель даёт характерное напряжение 16,1 МПа и отношение 2,62 к типовому значению wet Z. Этот показатель не является коэффициентом запаса. Допуск к вращению требует Mechanical, испытаний образцов партии, проверки втулки, балансировки и защитного кожуха. Обозначения Э/Д и М1/М2 сохраняют раздельно. Для прослеживаемости каждому изготовленному сочетанию присваивают серийный номер и связывают его с CAD-файлом, версией расчёта, партией материала, маршрутной картой и протоколом испытаний.

### 26 Программа расчётного подтверждения

Таблица 21
Источник | Необходимые результаты | Действие
CFD двух моделей | ṁ, πtt, Δpt, ηtt, момент, поля Маха | Сравнение Э/Д
Static Structural | напряжения, деформации, реакции втулки, коэффициенты | Прочностная карта
Modal | собственные частоты и формы | Частотное разделение
Контакт втулки | контактное давление и касательные реакции | Подтверждение запрессовки
Материал | образцы XY/Z dry/wet | Паспорт партии и печати
Стенд двух моделей | давление, расход, вибрация | Сравнение Э/Д при 3 000 мин ¹⁻

### 27 Перечень обозначений

Таблица 22
Символ | Определение | Единица
D, r | диаметр и радиус | м
b | ширина канала | м
n | частота вращения | мин ¹⁻

Символ | Определение | Единица
ω | угловая скорость | рад/с
U | окружная скорость | м/с
C, W | абсолютная и относительная скорости | м/с
Cm, Cu | меридиональная и окружная составляющие | м/с
Q, ṁ | объёмный и массовый расход | м³/с; кг/с
Δh0 | удельная работа колеса | Дж/кг
πtt | отношение полных давлений | —
ηtt, ηm | полный и механический КПД | —
σ | коэффициент скольжения | —
φ2 | коэффициент расхода | —
ρ, μ | плотность и динамическая вязкость | кг/м³; Па·с
Ma, Re | числа Маха и Рейнольдса | —
Sscreen | отношение типовой прочности к скрининговому напряжению | —

### 28 Нормативные ссылки и правила применения

Для документации рабочего колеса применён следующий нормативный каркас.

Таблица 23

Документ | Наименование / предмет | Применение
ГОСТ Р 2.001-2023 | ЕСКД. Общие положения | Общие принципы КД
ГОСТ Р 2.102-2023 | ЕСКД. Виды и комплектность конструкторских документов | Состав комплекта и коды документов
ГОСТ 2.103-2013 | ЕСКД. Стадии разработки | Статус технического проекта и опытного образца
ГОСТ Р 2.104-2023 | ЕСКД. Основные надписи | Рамки и основные надписи форм 2 и 2а
ГОСТ Р 2.105-2019 | ЕСКД. Общие требования к текстовым документам | Структура и оформление текста
ГОСТ Р 2.106-2019 | ЕСКД. Текстовые документы | Спецификация и текстовые КД
ГОСТ Р 2.109-2023 | ЕСКД. Основные требования к чертежам | Полнота данных изготовления и контроля
ГОСТ Р 2.201-2023 | ЕСКД. Обозначение изделий и конструкторских документов | Присвоение обозначений организацией
ГОСТ Р 2.051-2023 | ЕСКД. Электронные документы. Общие положения | Управление электронными КД

Документ | Наименование / предмет | Применение
ГОСТ 2.052-2015 | ЕСКД. Электронная модель изделия. Общие положения | Статус и атрибуты CAD-модели
ГОСТ Р 2.053-2023 | ЕСКД. Электронная структура изделия. Общие положения | Гибридная сборочная единица
ГОСТ Р 2.503-2023 | ЕСКД. Правила внесения изменений | Изменения моделей и КД
ГОСТ 2.301-68; 2.302-68; 2.303-68; 2.304-81 | Форматы, масштабы, линии, шрифты | Будущие чертежи
ГОСТ 2.305-2008; 2.307-2011 | Изображения; размеры и предельные отклонения | Будущие чертежи
ГОСТ 2.308-2011; 2.309-73; 2.316-2008 | Геометрические допуски; шероховатость; технические требования | Будущие чертежи
ГОСТ 8.417-2002 | Единицы величин | Единицы СИ
ГОСТ 11262-2017 | Пластмассы. Метод испытания на растяжение | Образцы-свидетели PA12-CF10
ГОСТ Р 57558-2017 | Аддитивные технологические процессы. Базовые принципы. Часть 1. Термины и определения | Терминология аддитивного изготовления
ISO/ASTM 52900:2021 | Additive manufacturing — Fundamentals and vocabulary | Актуальная международная терминология
ISO 21940-11:2016 | Mechanical vibration — Rotor balancing — Part 11 | Процедуры и допуски балансировки жёстких роторов
ГОСТ 15.309-98 | Испытания и приёмка выпускаемой продукции | Принципы приёмки; применить в согласованном объёме

Важно. Ссылки на стандарты не заменяют нормоконтроль. Стандарты
применяются | в | той | части, | которая | относится | к | опытному
машиностроительному | изделию | и | не | противоречит | утверждённому
техническому заданию.

### 29 Источники расчётных данных

[1] Fiberon / Polymaker. TDS Fiberon PA12-CF10, version 1.1: https://fiberon.polymaker.com/wp-content/uploads/TDS_FIBERON-PA12-CF10_V1.1_EN.pdf
[2] Fiberon / Polymaker. PA12-CF10 product data and printing recommendations: https://fiberon.polymaker.com/product/pa12-cf10/
[3] NASA Glenn Research Center. Compressor Thermodynamics: https://www.grc.nasa.gov/www/k-12/airplane/compth.html
[4] NASA Glenn Research Center. Isentropic Flow Equations: https://www.grc.nasa.gov/www/k-12/airplane/isentrop.html
[5] Jansen W. Impeller Blade Design Method for Centrifugal Compressors, NASA, 1974: https://ntrs.nasa.gov/api/citations/19750003125/downloads/19750003125.pdf
[6] Galvas M.R. Fortran Program for Predicting Off-Design Performance of Centrifugal Compressors, NASA, 1972: https://ntrs.nasa.gov/api/citations/19720020344/downloads/19720020344.pdf

[7] Hexcel. Carbon Fiber Reinforcements: https://www.hexcel.com/Products/Fabrics-Reinforcements/Carbon-Fiber-Reinforcements/
[8] 3M. Surface Preparation and Pretreatment for Structural Adhesives: https://multimedia.3m.com/mws/media/933332O/surface-prep-pretreatment-for-structural-adhesive-techbulletin.pdf
[9] ISO 21940-11:2016. Mechanical vibration — Rotor balancing — Part 11.
[10] ГОСТ 23360-78. Соединения шпоночные с призматическими шпонками. Размеры шпонок и сечений пазов. Допуски и посадки.
[11] Финальная CAD-модель РК-200-Э max_efficiency_ready_.STEP после обрезки в SolidWorks до D2 = 200 мм; геометрический аудит выполнен по STEP.
[12] Параметрическая конфигурация РК-200-Д max_pressure: D2 = 200 мм, D1s = 105,075 мм, b2 = 14,242 мм, 13 основных и 13 сплиттерных лопаток; перед печатью выпускается контрольный STEP.
[13] Программа параметрической оптимизации и одномерного расчёта МИТК-РК. Требуется приложить версию, контрольную сумму, входные данные, диапазоны оптимизации и машинный протокол расчёта РК-200-Э/Д.
