IImasterII/mitk-rk-site/documents/0016_e3.pdf

Разраб.

Пров.

Т.контр.

Н.контр.

Утв.

МИТК-РК | 22.07.26

## EMTH.19.01.02.59.00.000.0016 Э3

## Схема электрическая принципиальная стенда

Лит.

Лист 1 | Листов 1
| Формат A3

Инв. № подл. Подп. и дата Взам. инв. № Инв. № дубл.

# СТЕНД РК-200. СХЕМА ЭЛЕКТРИЧЕСКАЯ ПРИНЦИПИАЛЬНАЯ

X1

~230 В; PE

QF1

2P; по расчёту

K1

контактор ввода

A1

STV050U22M2

M1

5АИ80А2; Δ220 В

1×220 В → 3×220 В; Iвых.ном=9 А

вал Ø22; шпонка 6 мм; скорость ≤3 000 мин⁻¹

PE

## ЦЕПЬ РАЗРЕШЕНИЯ И АВАРИЙНОГО ОСТАНОВА, 24 В DC

PS1

230/24 В DC

S0

АВАР. СТОП NC

SQ1

кожух NC

K2

перескорость NC

S1

СТОП NC

S2

ПУСК/СБРОС NO

K1

катушка 24 В

PS2

24/5 В DC; SELV

A2

STM32 + Raspberry Pi

FT1

расход

PT1

давление вход

PT2

давление выход

TT1

температура

VT1

вибрация

ST1

тахометр

RS-485 / дискретные команды RUN-ENABLE

## ПРИМЕЧАНИЯ

1. QF1, K1, кабели и клеммы назначить расчётом и по руководству STV050.
2. Перед подключением подтвердить шильдик двигателя Δ220/Y380 В.
3. Нормальный останов выполняет ПЧ; K1 служит цепью разрешения/аварийного снятия питания.
4. Коммутация U-V-W при работающем или заряженном ПЧ запрещена.
5. Максимальная скорость 3 000 мин⁻¹ контролируется ST1 и независимым K2.
6. Пуск разрешён только при закрытом защитном корпусе и исправном аварийном останове.
7. Точка 12 000 мин⁻¹ данной схемой не допускается.

Статус: проект для выпуска рабочей КД. Монтаж — только квалифицированным персоналом.
