IImasterII/mitk-rk-site/documents/0017_c2.pdf

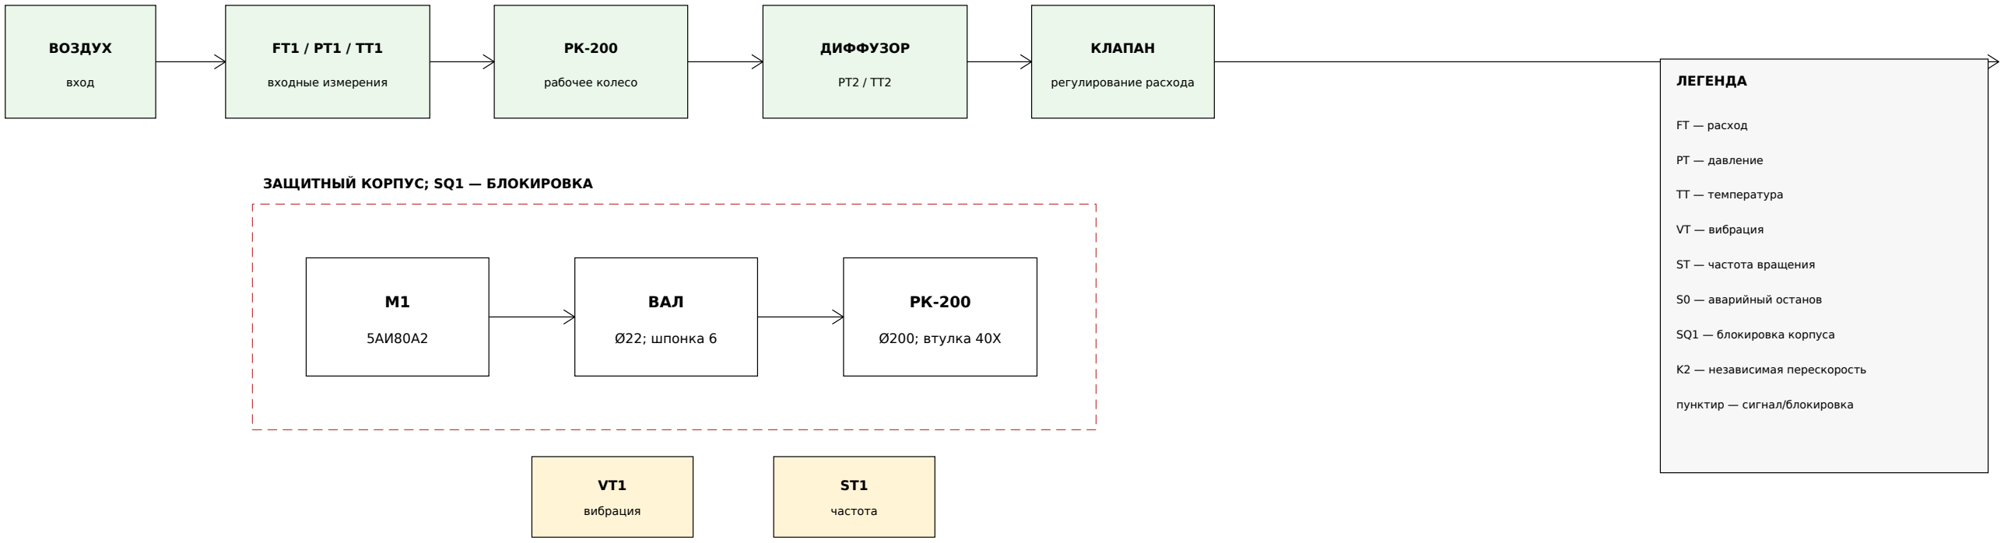
[picture p90: figure]
ВОЗДУХ; вход; входные измерения; рабочее колесо; ДИФФУЗОР; КЛАПАН; регулирование расхода; ВАЛ; Ø22; шпонка 6; Ø200; втулка 40Х; ЗАЩИТНЫЙ КОРПУС; SQ1 — БЛОКИРОВКА; вибрация; частота; ЛЕГЕНДА; FT — расход; PT — давление; TT — температура; VT — вибрация; ST — частота вращения; S0 — аварийный останов; SQ1 — блокировка корпуса; K2 — независимая перескорость; пунктир — сигнал/блокировка

| EMTH.19.01.02.59.00.000.0017 С2 | Лит.
Разраб. | МИТК-РК | 22.07.26 | Схема комбинированная функциональная стенда

Пров.

Т.контр.

Н.контр.
| | | | Лист 1 Листов 1 Формат A3

Утв.

Инв. № подл. Подп. и дата Взам. инв. № Инв. № дубл.

# СТЕНД РК-200. ФУНКЦИОНАЛЬНАЯ СХЕМА

QF1/K1

защита и разрешение

A1

STV050U22M2

M1

двигатель

A2

контроллер/регистратор

H1

экран/архив

ЦЕПЬ БЕЗОПАСНОСТИ:
S0

авар. стоп

SQ1

кожух

K2

>3 000 мин⁻¹

K1

снятие разрешения

Разрешённый режим: ≤3 000 мин⁻¹. Точка 12 000 мин⁻¹ данной схемой не допускается.
