IImasterII/mitk-rk-site/calculations/ReportANSYS_pressure_12000_bonded_without_vtulka(1).pdf

# Project*

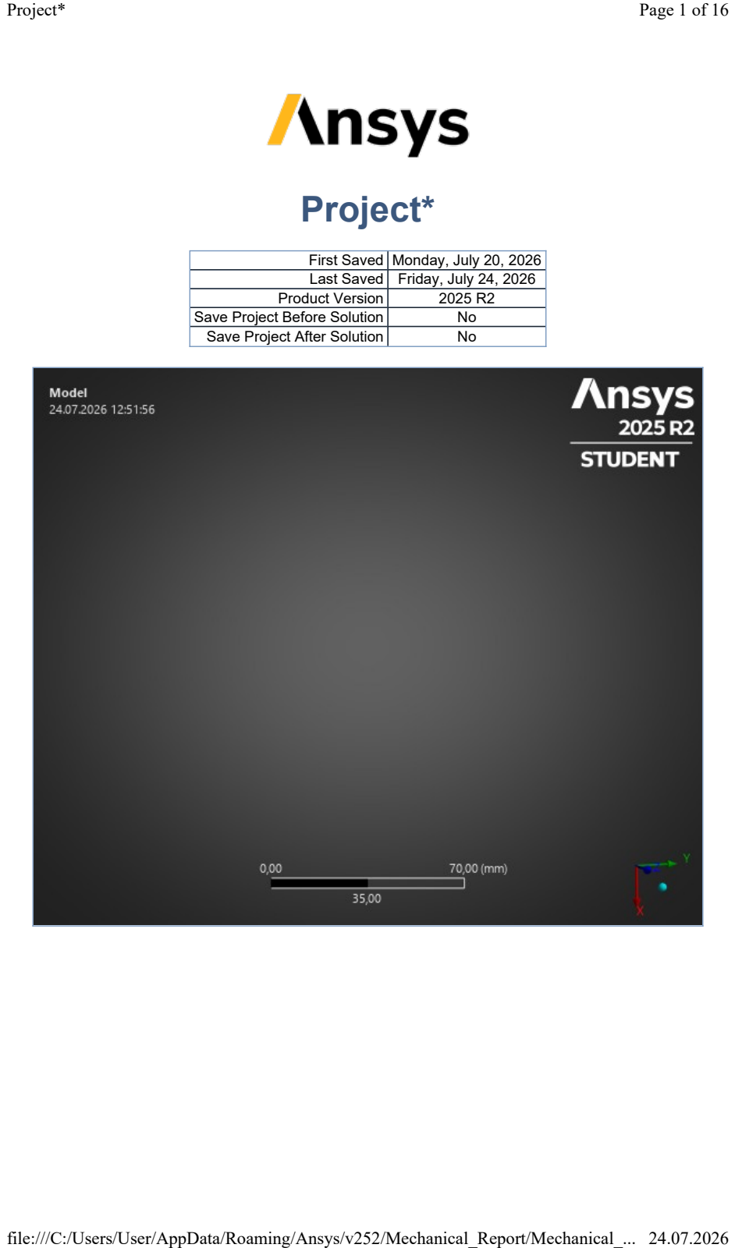
[picture p92: page 1]

First Saved | Monday, July 20, 2026
Last Saved | Friday, July 24, 2026
Product Version | 2025 R2
Save Project Before Solution | No
Save Project After Solution | No
Project* | Page 1 of 16

file:///C:/Users/User/AppData/Roaming/Ansys/v252/Mechanical_Report/Mechanical_... 24.07.2026

# Contents

l Units

l Model (B4)
¡ Geometry Imports
n Geometry Import (B3)
¡ Geometry
n max_pressure|Вырез-Вытянуть2 ¡ Materials
¡ Coordinate Systems
¡ Connections
¡ Mesh
n Face Sizing
¡ Named Selections
¡ Static Structural (B5)
n Analysis Settings
n Rotational Velocity
n Loads
n Solution (B6)
n Solution Information
n Results
n Stress Tool
n Safety Factor

l Material Data
¡ Steel 35L Gost

# Units

TABLE 1

# Model (B4)

TABLE 2
Model (B4) > Geometry Imports

TABLE 3
Model (B4) > Geometry Imports > Geometry Import (B3)
Unit System | Metric (mm, kg, N, s, mV, mA) Degrees rad/s Celsius
Angle | Degrees
Rotational Velocity | rad/s
Temperature | Celsius
Object Name | Geometry Imports
State | Solved
Object Name | Geometry Import (B3)
State | Solved
Definition
Source | C:\Users\User\Desktop\Прочностные характеристики\max_pressure\max_pressure.step
Type | Step
Basic Geometry Options
Solid Bodies | Yes
Surface Bodies | Yes
Project* | Page 2 of 16

Line Bodies | No
Parameters | Independent
Parameter Key | ANS;DS
Attributes | No
Named Selections | No
Material Properties | No
Advanced Geometry Options
Use Associativity | Yes
Coordinate Systems | No
Reader Mode Saves Updated File | No
Use Instances | Yes
Smart CAD Update | Yes
Compare Parts On Update | No
Analysis Type | 3-D
Mixed Import Resolution | None
Import Facet Quality | Source
Clean Bodies On Import | No
Stitch Surfaces On Import | None
Decompose Disjoint Geometry | Yes
Enclosure and Symmetry Processing | Yes

## Geometry

TABLE 4
Model (B4) > Geometry
Object Name | Geometry
State | Fully Defined
Definition
Source | C:\Users\User\Desktop\Прочностные характеристики\max_pressure\max_pressure.step
Type | Step
Length Unit | Millimeters
Element Control | Program Controlled
Display Style | Body Color
Bounding Box
Length X | 200, mm
Length Y | 200, mm
Length Z | 51,025 mm
Properties
Volume | 6,9549e+005 mm³
Mass | 5,4248 kg
Scale Factor Value | 1,
Statistics
Bodies | 1
Active Bodies | 1
Nodes | 127598
Elements | 72770
Mesh Metric | None
Update Options
Assign Default Material | No
Basic Geometry Options
Solid Bodies | Yes
Surface Bodies | Yes
Line Bodies | No
Project* | Page 3 of 16

TABLE 5
Model (B4) > Geometry > Parts
Parameters | Independent
Parameter Key | ANS;DS
Attributes | No
Named Selections | No
Material Properties | No
Advanced Geometry Options
Use Associativity | Yes
Coordinate Systems | No
Reader Mode Saves Updated File | No
Use Instances | Yes
Smart CAD Update | Yes
Compare Parts On Update | No
Analysis Type | 3-D
Mixed Import Resolution | None
Import Facet Quality | Source
Clean Bodies On Import | No
Stitch Surfaces On Import | None
Decompose Disjoint Geometry | Yes
ID_GeometryPrefProcessPhysicsDefinition | No
Enclosure and Symmetry Processing | Yes
Object Name | max_pressure|Вырез-Вытянуть2
State | Meshed
Graphics Properties
Visible | Yes
Transparency | 1
Definition
Suppressed | No
Stiffness Behavior | Flexible
Coordinate System | Default Coordinate System
Reference Temperature | By Environment
Treatment | None
Material
Assignment | Steel 35L Gost
Nonlinear Effects | Yes
Thermal Strain Effects | Yes
Bounding Box
Length X | 200, mm
Length Y | 200, mm
Length Z | 51,025 mm
Properties
Volume | 6,9549e+005 mm³
Mass | 5,4248 kg
Centroid X | -4,5014e-003 mm
Centroid Y | 9,8156e-004 mm
Centroid Z | 13,043 mm
Moment of Inertia Ip1 | 10211 kg·mm²
Moment of Inertia Ip2 | 10207 kg·mm²
Moment of Inertia Ip3 | 18849 kg·mm²
Statistics
Nodes | 127598
Elements | 72770
Mesh Metric | None
Project* | Page 4 of 16

TABLE 6
Model (B4) > Materials
Object Name | Materials
State | Fully Defined
Statistics
Materials | 5
Material Assignments | 0

## Coordinate Systems

TABLE 7
Model (B4) > Coordinate Systems > Coordinate System
Object Name | Global Coordinate System
State | Fully Defined
Definition
Type | Cartesian
Coordinate System ID | 0,
Origin
Origin X | 0, mm
Origin Y | 0, mm
Origin Z | 0, mm
Directional Vectors
X Axis Data | [ 1, 0, 0, ]
Y Axis Data | [ 0, 1, 0, ]
Z Axis Data | [ 0, 0, 1, ]
Transfer Properties
Source
Read Only | No

## Connections

TABLE 8
Model (B4) > Connections
Object Name | Connections
State | Fully Defined
Auto Detection
Generate Automatic Connection On Refresh Yes Transparency
Enabled Yes
Statistics
Contacts | 0
Active Contacts | 0
Joints | 0
Active Joints | 0
Beams | 0
Active Beams | 0
Bearings | 0
Active Bearings | 0
Springs | 0
Active Springs | 0
Body Interactions | 0
Active Body Interactions | 0

## Mesh

TABLE 9

Project* | Page 5 of 16

Model (B4) > Mesh

TABLE 10
Model (B4) > Mesh > Mesh Controls
Object Name | Mesh
State | Solved
Display
Display Style Use Geometry Setting Defaults
Physics Preference | Mechanical
Element Order | Program Controlled
Element Size | 3,39 mm
Sizing
Use Adaptive Sizing | Yes
Resolution | Default (2)
Mesh Defeaturing | Yes
Defeature Size | Default
Transition | Fast
Span Angle Center | Coarse
Initial Size Seed | Assembly
Bounding Box Diagonal | 287,41 mm
Average Surface Area | 531,5 mm²
Minimum Edge Length | 7,3636e-004 mm
Quality
Check Mesh Quality | Yes, Errors
Error Limits | Aggressive Mechanical
Target Element Quality | Default (5,e-002)
Smoothing | Medium
Mesh Metric | None
Inflation
Use Automatic Inflation | None
Inflation Option | Smooth Transition
Transition Ratio | 0,272
Maximum Layers | 5
Growth Rate | 1,2
Inflation Algorithm | Pre
Inflation Element Type | Wedges
View Advanced Options | No
Advanced
Number of CPUs for Parallel Part Meshing | Program Controlled
Straight Sided Elements | No
Rigid Body Behavior | Dimensionally Reduced
Triangle Surface Mesher | Program Controlled
Topology Checking | Yes
Pinch Tolerance | Please Define
Generate Pinch on Refresh | No
Auto-Map Fillets | No
Automatic Methods
Sheet Body Method | Prime Quad Dominant
Sweepable Body Method | Sweep
Statistics
Nodes | 127598
Elements | 72770
Show Detailed Statistics | No
Object Name | Face Sizing
State | Fully Defined
Scope
Project* | Page 6 of 16

Scoping Method | Geometry Selection
Geometry | 78 Faces
Definition
Suppressed | No
Type | Element Size
Element Size | 2,8 mm
Advanced
Defeature Size | Default
Influence Volume | No
Behavior | Soft

## Named Selections

# Static Structural (B5)

TABLE 11
Model (B4) > Analysis

TABLE 12
Model (B4) > Static Structural (B5) > Analysis Settings
Object Name | Static Structural (B5)
State | Solved
Definition
Physics Type | Structural
Analysis Type | Static Structural
Solver Target | Mechanical APDL
Options
Environment Temperature | 22, °C
Generate Input Only | No
Object Name | Analysis Settings
State | Fully Defined
Step Controls
Number Of Steps | 1,
Current Step Number | 1,
Step End Time | 1, s
Auto Time Stepping | On
Define By | Substeps
Initial Substeps | 20,
Minimum Substeps | 10,
Maximum Substeps | 100,
Solver Controls
Solver Type | Program Controlled
Weak Springs | Program Controlled
Solver Pivot Checking | Program Controlled
Large Deflection | On
Inertia Relief | Off
Quasi-Static Solution | On
Rotordynamics Controls
Coriolis Effect | Off
Restart Controls
Generate Restart Points | Program Controlled
Retain Files After Full Solve | No
Combine Restart Files | Program Controlled
Nonlinear Controls
Newton-Raphson Option | Program Controlled
Project* | Page 7 of 16

TABLE 13
Model (B4) > Static Structural (B5) > Rotations
Force Convergence | Program Controlled
Moment Convergence | Program Controlled
Displacement Convergence | Program Controlled
Rotation Convergence | Program Controlled
Line Search | Program Controlled
Stabilization | Constant
--Method | Energy
--Energy Dissipation Ratio | 1,e-004
--Activation For First Substep | No
--Stabilization Force Limit | 0,2

Advanced
Inverse Option | No
Contact Split (DMP) | Program Controlled
Output Controls
Output Selection | None
Stress | Yes
Back Stress | No
Strain | Yes
Contact Data | Yes
Nonlinear Data | No
Nodal Forces | No
Volume and Energy | Yes
Euler Angles | Yes
General Miscellaneous | No
Contact Miscellaneous | No
Store Results At | All Time Points
Result File Compression | Program Controlled
Analysis Data Management
Solver Files Directory | C:\Users\User\Desktop\Прочностные характеристики\All_work_pressure_files\dp0\SYS-1\MECH\
Future Analysis | None
Scratch Solver Files Directory
Save MAPDL db | No
Contact Summary | Program Controlled
Delete Unneeded Files | Yes
Nonlinear Solution | Yes
Solver Units | Active System
Solver Unit System | nmm
Object Name | Rotational Velocity
State | Fully Defined
Scope
Scoping Method | Geometry Selection
Geometry | All Bodies
Definition
Define By | Components
Coordinate System | Global Coordinate System
X Component | 0, rad/s (ramped)
Y Component | 0, rad/s (ramped)
Z Component | -1256,6 rad/s (ramped)
Project* | Page 8 of 16

FIGURE 1
Model (B4) > Static Structural (B5) > Rotational Velocity


TABLE 14
Model (B4) > Static Structural (B5) > Loads
X Coordinate | 5,e-004 mm
Y Coordinate | -6,1961e-004 mm
Z Coordinate | 4,65e-002 mm
Suppressed | No
Object Name | Condition Thermal | Pressure | Cylindrical Support | Remote Displacement
State | Fully Defined | | | Suppressed
Scope
Scoping Method | Geometry Selection
Geometry | 1 Body | 78 Faces | 2 Faces
Coordinate System | | Global Coordinate System
X Coordinate | | 2,7818e-016 mm
Y Coordinate | | 2,6427e-016 mm
Z Coordinate | | 21,75 mm
Location | | Defined
Definition
Type | Condition Thermal | Pressure | Cylindrical Support | Remote Displacement
Magnitude | 22, °C (ramped) | 0,10132 MPa (ramped)
Suppressed | No | | | Yes
Define By | | Normal To
Applied By | | Surface Effect
Loaded Area | | Deformed
Radial | | | Fixed
Axial | | | Fixed
Tangential | | | Free
Project* | Page 9 of 16

FIGURE 2
Model (B4) > Static Structural (B5) > Thermal Condition


FIGURE 3
Model (B4) > Static Structural (B5) > Pressure
X Component | 0, mm (ramped)
Y Component | 0, mm (ramped)
Z Component | 0, mm (ramped)
Rotation X | 0, ° (ramped)
Rotation Y | 0, ° (ramped)
Rotation Z | 0, ° (ramped)
Behavior | Deformable
Advanced
Pinball Region | All
Project* | Page 10 of 16


FIGURE 4
Model (B4) > Static Structural (B5) > Remote Displacement

## Solution (B6)

TABLE 15
Model (B4) > Static Structural (B5) > Solution
Object Name | Solution (B6)
State | Solved
Project* | Page 11 of 16

TABLE 16
Model (B4) > Static Structural (B5) > Solution (B6) > Solution Information

TABLE 17
Model (B4) > Static Structural (B5) > Solution (B6) > Results

Adaptive Mesh Refinement
Max Refinement Loops | 1,
Refinement Depth | 2,
Information
Status | Done
MAPDL Elapsed Time | 5 m 16 s
MAPDL Memory Used | 938, MB
MAPDL Result File Size | 580,56 MB
Post Processing
Beam Section Results | No
On Demand Stress/Strain | No
Object Name | Solution Information
State | Solved
Solution Information
Solution Output | Solver Output
Newton-Raphson Residuals | 0
Identify Element Violations | 5
Update Interval | 2,5 s
Display Points | All
FE Connection Visibility
Activate Visibility | Yes
Display | All FE Connectors
Draw Connections Attached To | All Nodes
Line Color | Connection Type
Visible on Results | No
Line Thickness | Single
Display Type | Lines
Object Name | Total Deformation | Equivalent Stress
State | Solved
Scope
Scoping Method | Geometry Selection
Geometry | All Bodies
Definition
Type | Total Deformation | Equivalent (von-Mises) Stress
By | Time
Display Time | Last
Separate Data by Entity | No
Calculate Time History | Yes
Identifier
Suppressed | No
Results
Minimum | 0,36838 mm | 8,2323e-002 MPa
Maximum | 2,4617 mm | 81,168 MPa
Average | 1,5583 mm | 16,88 MPa
Minimum Occurs On | max_pressure|Вырез-Вытянуть2
Maximum Occurs On | max_pressure|Вырез-Вытянуть2
Minimum Value Over Time
Minimum | 5,8514e-002 mm | 3,8595e-004 MPa
Maximum | 0,36838 mm | 8,2323e-002 MPa
Maximum Value Over Time
Project* | Page 12 of 16

FIGURE 5
Model (B4) > Static Structural (B5) > Solution (B6) > Total Deformation

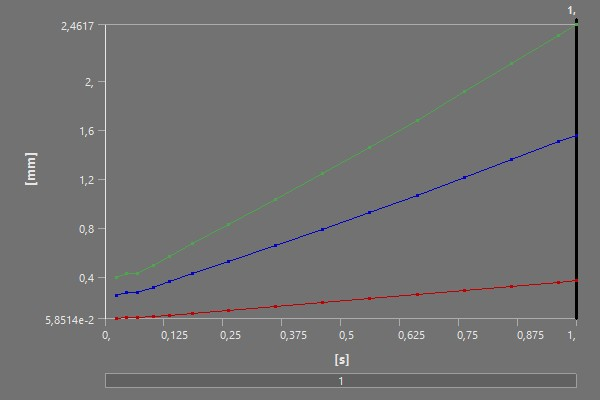
[picture p93: figure]

TABLE 18
Model (B4) > Static Structural (B5) > Solution (B6) > Total Deformation
Minimum | 0,3901 mm | 2,0461 MPa
Maximum | 2,4617 mm | 81,168 MPa
| Information
Time | 1, s
Load Step | 1
Substep | 15
Iteration Number | 30
Integration Point Results
Display Option | Averaged
Average Across Bodies | No
Time [s] | Minimum [mm] | Maximum [mm] | Average [mm]
2,25e-002 | 5,8514e-002 | 0,3901 | 0,24736
4,5e-002 | 6,3481e-002 | 0,42322 | 0,26836
6,75e-002 | 6,3422e-002 | 0,42285 | 0,26812
0,10125 | 7,366e-002 | 0,49114 | 0,3114
0,135 | 8,4601e-002 | 0,56413 | 0,35766
0,18563 | 0,10069 | 0,67147 | 0,42569
0,26156 | 0,1242 | 0,82841 | 0,52511
0,36156 | 0,15486 | 1,0333 | 0,65483
0,46156 | 0,18597 | 1,2411 | 0,78641
0,56156 | 0,21824 | 1,4568 | 0,92294
0,66156 | 0,25173 | 1,6809 | 1,0647
0,76156 | 0,28598 | 1,91 | 1,2096
0,86156 | 0,32049 | 2,141 | 1,3556
0,96156 | 0,35506 | 2,3725 | 1,5019
1, | 0,36838 | 2,4617 | 1,5583
Project* | Page 13 of 16

FIGURE 6
Model (B4) > Static Structural (B5) > Solution (B6) > Equivalent Stress

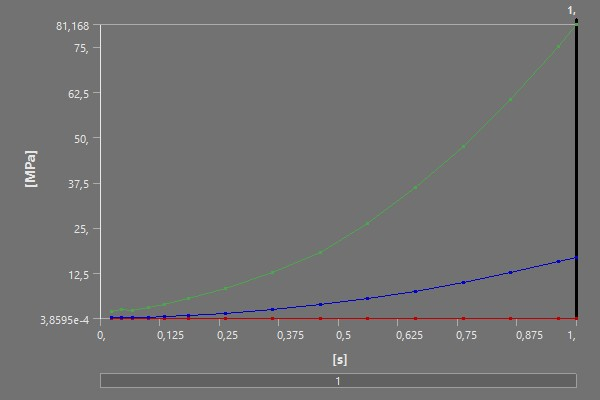
[picture p94: figure]

TABLE 19
Model (B4) > Static Structural (B5) > Solution (B6) > Equivalent Stress

TABLE 20
Model (B4) > Static Structural (B5) > Solution (B6) > Stress Safety Tools

TABLE 21
Model (B4) > Static Structural (B5) > Solution (B6) > Stress Tool > Results
Time [s] | Minimum [MPa] | Maximum [MPa] | Average [MPa]
2,25e-002 | 3,8595e-004 | 2,0461 | 0,15682
4,5e-002 | 4,5556e-004 | 2,3742 | 0,19489
6,75e-002 | 4,4095e-004 | 2,309 | 0,21756
0,10125 | 1,5921e-003 | 3,0506 | 0,33512
0,135 | 2,2727e-003 | 3,9765 | 0,49242
0,18563 | 3,498e-003 | 5,5485 | 0,7929
0,26156 | 6,3244e-003 | 8,2909 | 1,3877
0,36156 | 1,1324e-002 | 12,73 | 2,4393
0,46156 | 1,7945e-002 | 18,348 | 3,8049
0,56156 | 2,6339e-002 | 26,36 | 5,4995
0,66156 | 3,6346e-002 | 36,081 | 7,5321
0,76156 | 4,7937e-002 | 47,471 | 9,9012
0,86156 | 6,1223e-002 | 60,488 | 12,601
0,96156 | 7,6139e-002 | 75,114 | 15,628
1, | 8,2323e-002 | 81,168 | 16,88
Object Name | Stress Tool
State | Solved
Definition
Theory | Max Equivalent Stress
Stress Limit Type | Tensile Yield Per Material
Object Name | Safety Factor
State | Solved
Project* | Page 14 of 16

FIGURE 7
Model (B4) > Static Structural (B5) > Solution (B6) > Stress Tool > Safety Factor

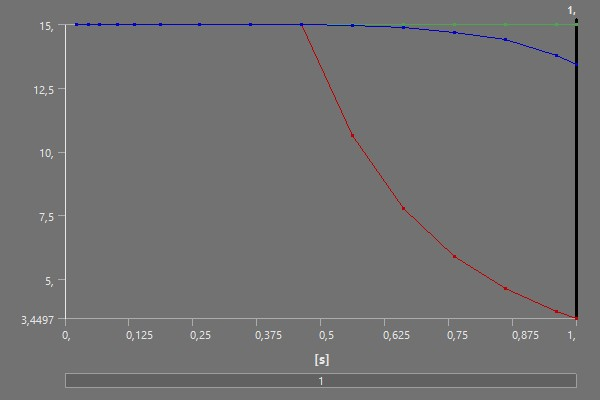
[picture p95: figure]

TABLE 22

Scope
Scoping Method | Geometry Selection
Geometry | All Bodies
Definition
Type | Safety Factor
By | Time
Display Time | Last
Separate Data by Entity | No
Calculate Time History | Yes
Identifier
Suppressed | No
Integration Point Results
Display Option | Averaged
Average Across Bodies | No
Results
Minimum | 3,4497
Minimum Occurs On | max_pressure|Вырез-Вытянуть2
Minimum Value Over Time
Minimum | 3,4497
Maximum | 15,
Maximum Value Over Time
Minimum | 15,
Maximum | 15,
Information
Time | 1, s
Load Step | 1
Substep | 15
Iteration Number | 30
Project* | Page 15 of 16

Model (B4) > Static Structural (B5) > Solution (B6) > Stress Tool > Safety Factor

# Material Data

Time [s] | Minimum | Maximum | Average
2,25e-002 | 15, | 15, | 15,
4,5e-002
6,75e-002
0,10125
0,135
0,18563
0,26156
0,36156
0,46156
0,56156 | 10,622 | 14,965
0,66156 | 7,7602 | 14,869
0,76156 | 5,8983 | 14,696
0,86156 | 4,629 | 14,409
0,96156 | 3,7277 | 13,786
1, | 3,4497 | 13,447

## Steel 35L Gost

TABLE 23
Steel 35L Gost > Constants

TABLE 24
Steel 35L Gost > Color

TABLE 25
Steel 35L Gost > Isotropic Elasticity

TABLE 26
Steel 35L Gost > Tensile Yield Strength

TABLE 27
Steel 35L Gost > Compressive Yield Strength

TABLE 28
Steel 35L Gost > Tensile Ultimate Strength
Density | 7,8e-006 kg mm^-3
Coefficient of Thermal Expansion | 1,2e-005 K^-1
Red | Green | Blue
109, | 157, | 209,
Young's Modulus MPa | Poisson's Ratio | Bulk Modulus MPa | Shear Modulus MPa | Temperature K
2,e+005 | 0,3 | 1,6667e+005 | 76923 | 295,15

Tensile Yield Strength MPa 280,

Compressive Yield Strength MPa 280,

Tensile Ultimate Strength MPa 500,

Project* | Page 16 of 16
