IImasterII/mitk-rk-site/assets/brand/МИТК-РК лого.png

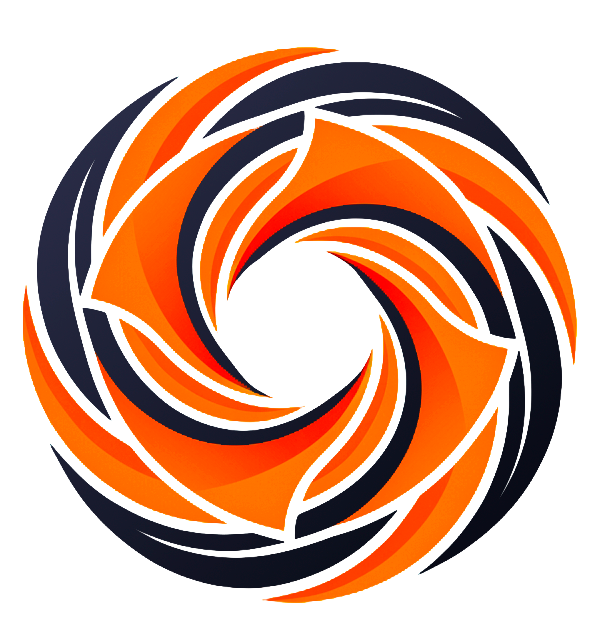
assets/brand/МИТК-РК лого.png
