IImasterII/mitk-rk-site/assets/business-cards/participant_01_back_preview.png

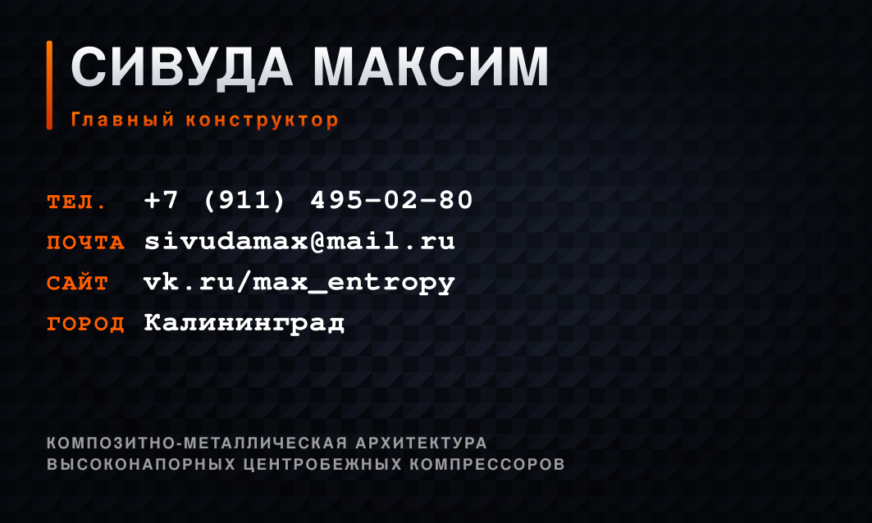
assets/business-cards/participant_01_back_preview.png
