IImasterII/mitk-rk-site/assets/business-cards/participant_02_back_preview.png

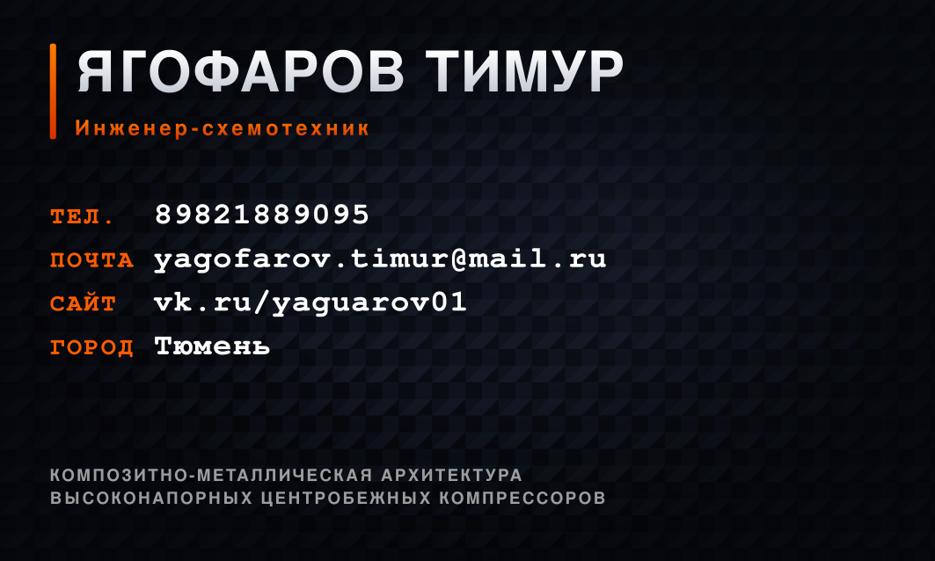
assets/business-cards/participant_02_back_preview.png
