IImasterII/mitk-rk-site/assets/business-cards/participant_03_back_preview.png

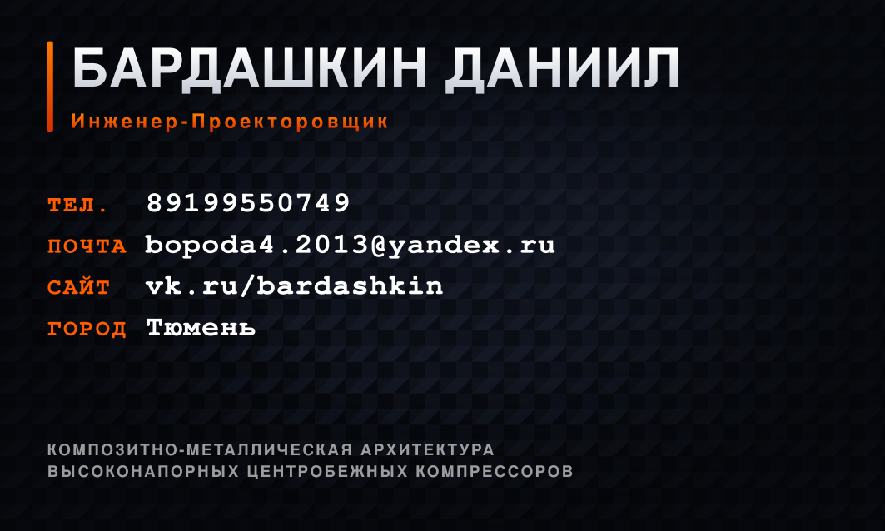
assets/business-cards/participant_03_back_preview.png
