IImasterII/mitk-rk-site/assets/business-cards/participant_04_back_preview.png

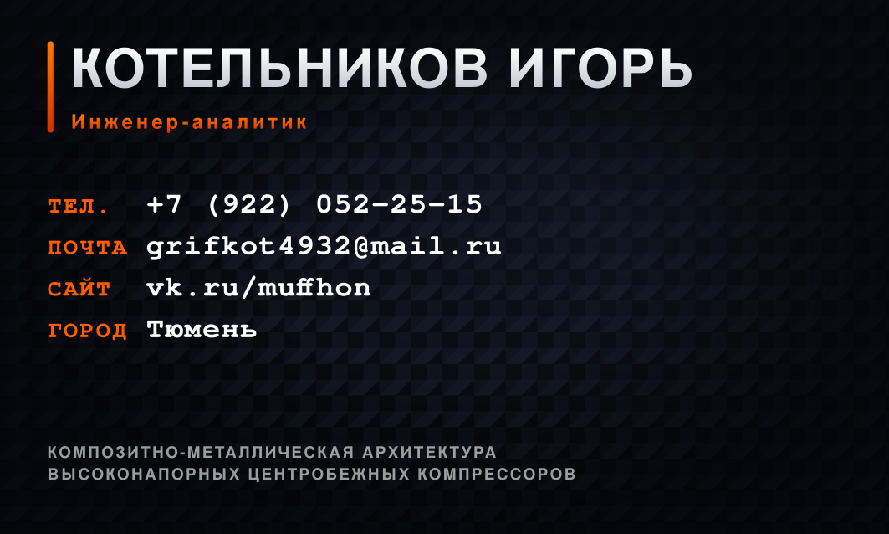
assets/business-cards/participant_04_back_preview.png
