IImasterII/mitk-rk-site/assets/business-cards/participant_05_back_preview.png

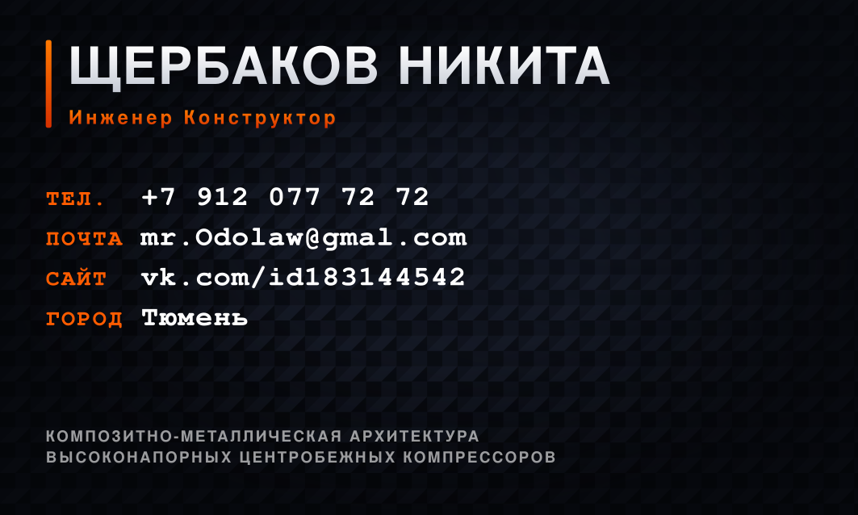
assets/business-cards/participant_05_back_preview.png
