IImasterII/mitk-rk-site/assets/business-cards/participant_07_back_preview.png

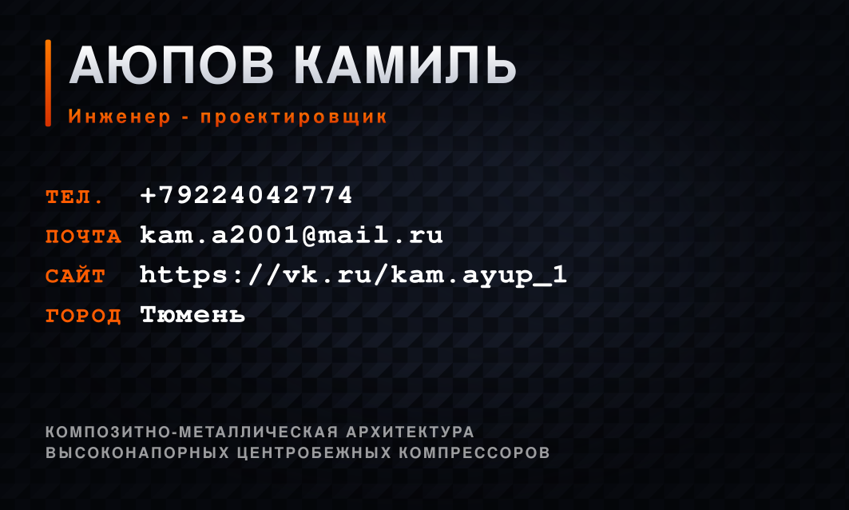
assets/business-cards/participant_07_back_preview.png
