IImasterII/mitk-rk-site/assets/business-cards/participant_08_back_preview.png

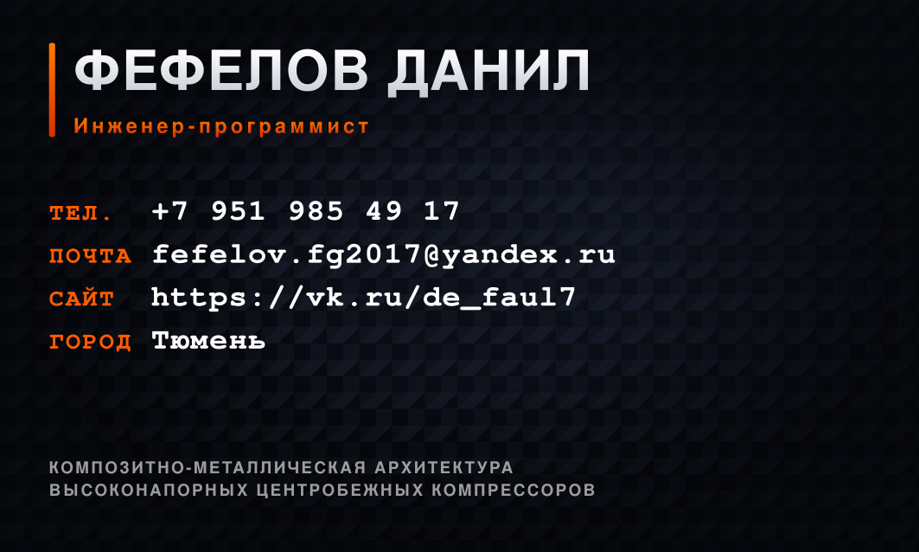
assets/business-cards/participant_08_back_preview.png
