IImasterII/mitk-rk-site/assets/business-cards/template_front_preview.png

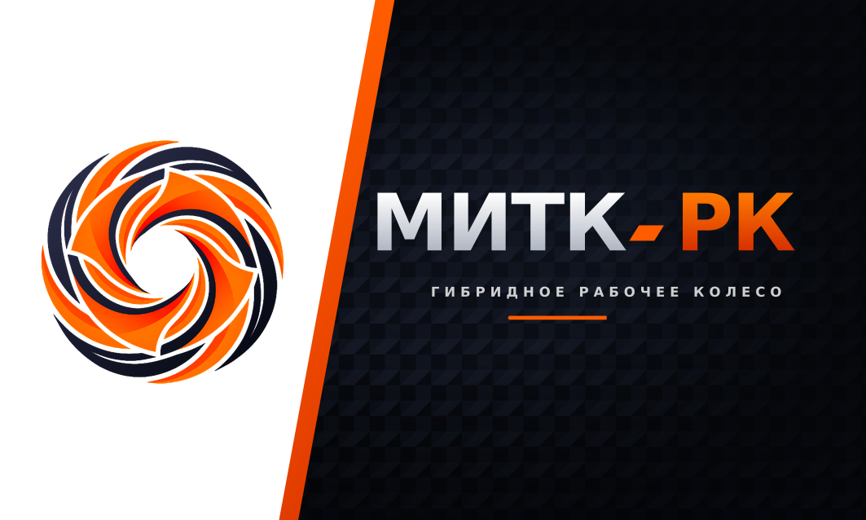
assets/business-cards/template_front_preview.png
