IImasterII/mitk-rk-site/assets/drawing-previews/cdw-cover.png

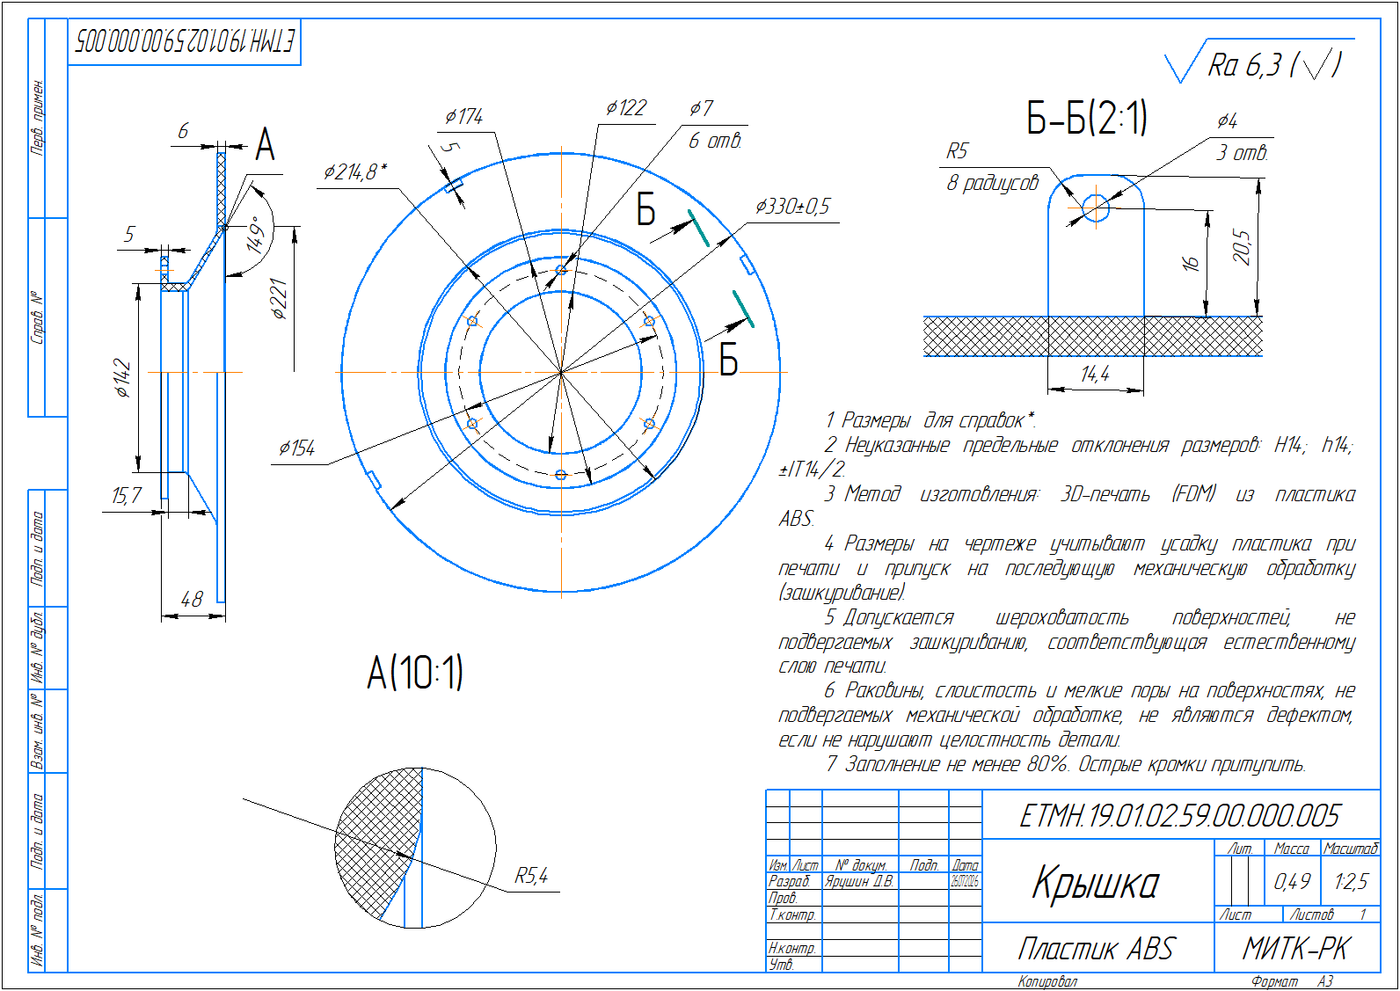
assets/drawing-previews/cdw-cover.png
