IImasterII/mitk-rk-site/assets/drawing-previews/cdw-flange.png

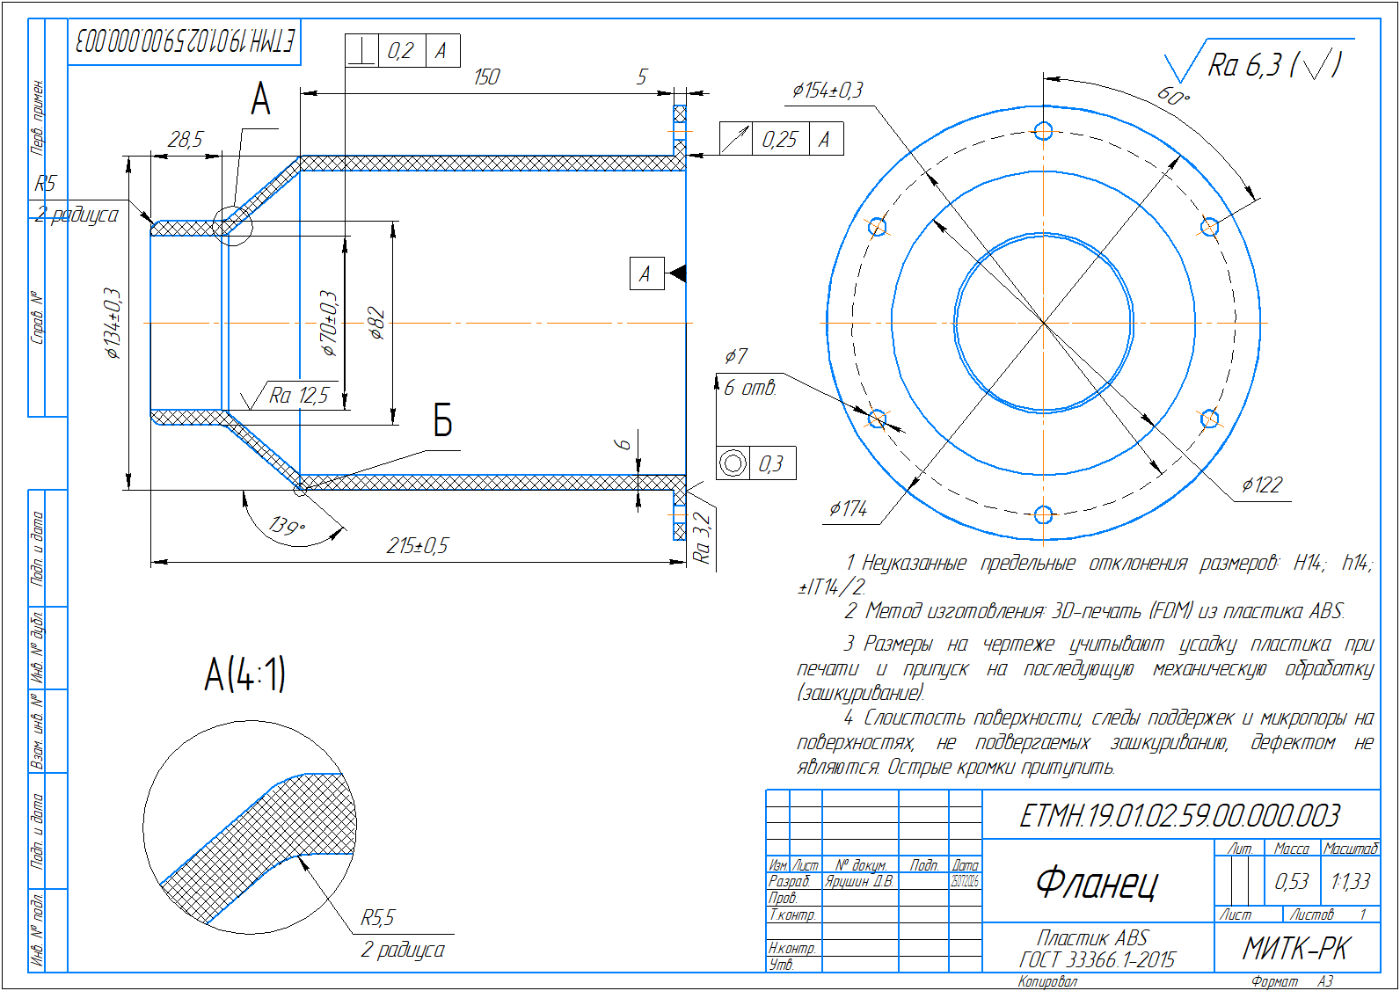
assets/drawing-previews/cdw-flange.png
