IImasterII/mitk-rk-site/assets/drawing-previews/cdw-functional-scheme.png

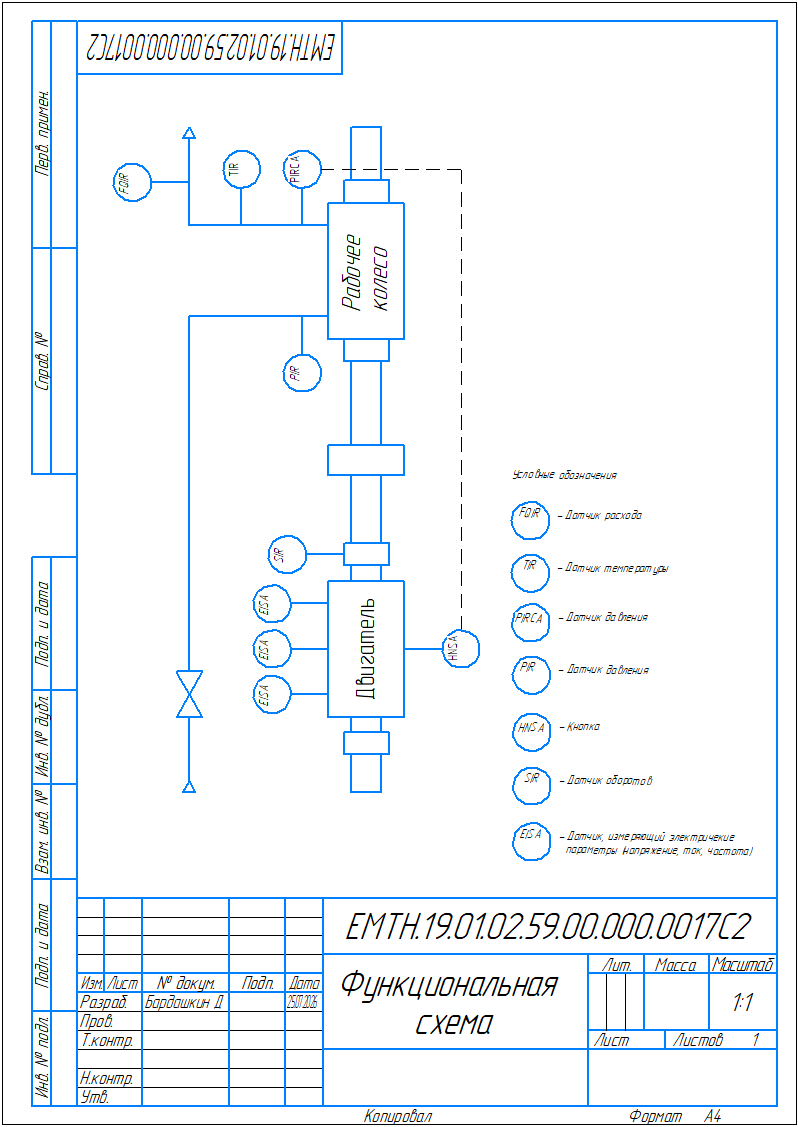
assets/drawing-previews/cdw-functional-scheme.png
