IImasterII/mitk-rk-site/assets/drawing-previews/cdw-impeller-2.png

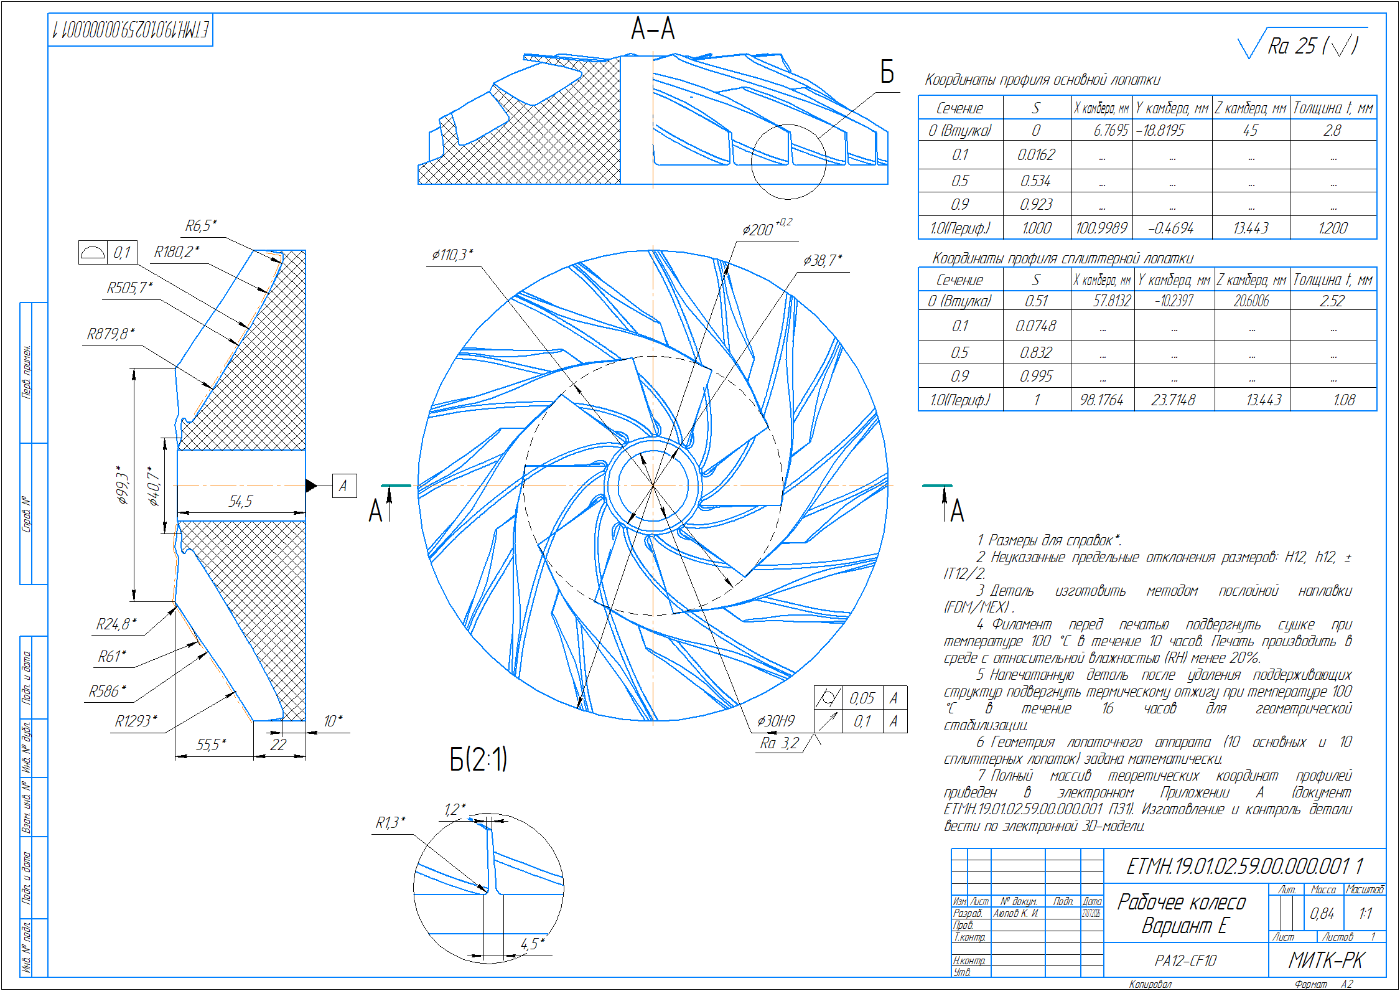
assets/drawing-previews/cdw-impeller-2.png
