IImasterII/mitk-rk-site/assets/drawing-previews/cdw-impeller.png

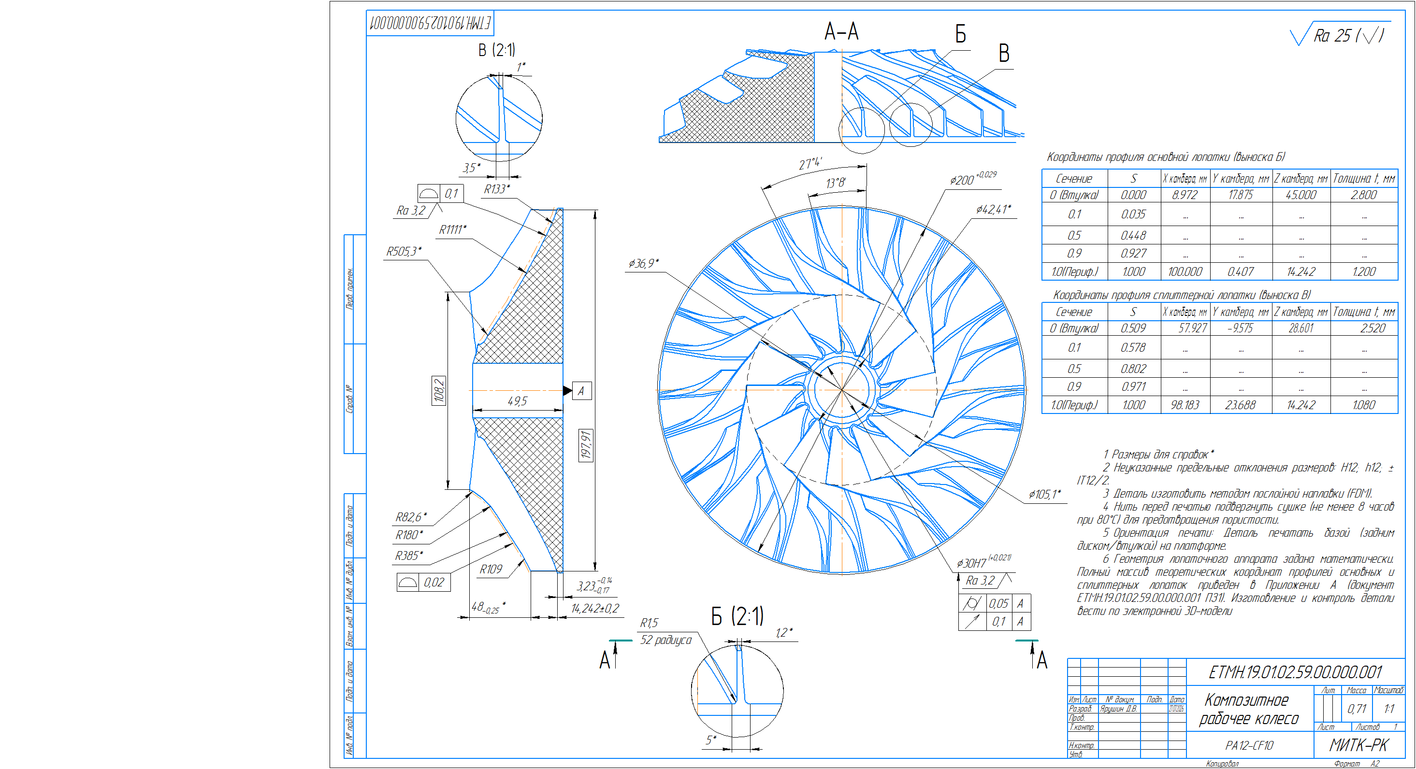
assets/drawing-previews/cdw-impeller.png
