IImasterII/mitk-rk-site/assets/drawing-previews/cdw-stand-1.png

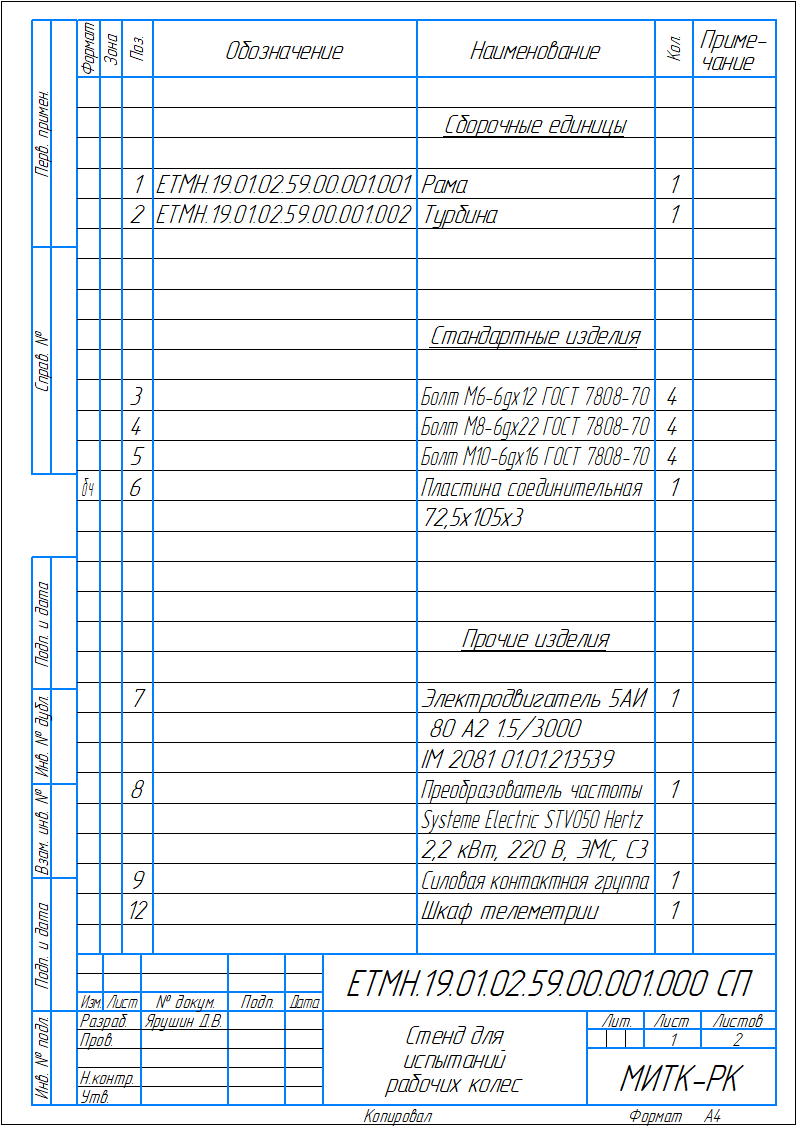
assets/drawing-previews/cdw-stand-1.png
