IImasterII/mitk-rk-site/assets/drawing-previews/cdw-stand-2.png

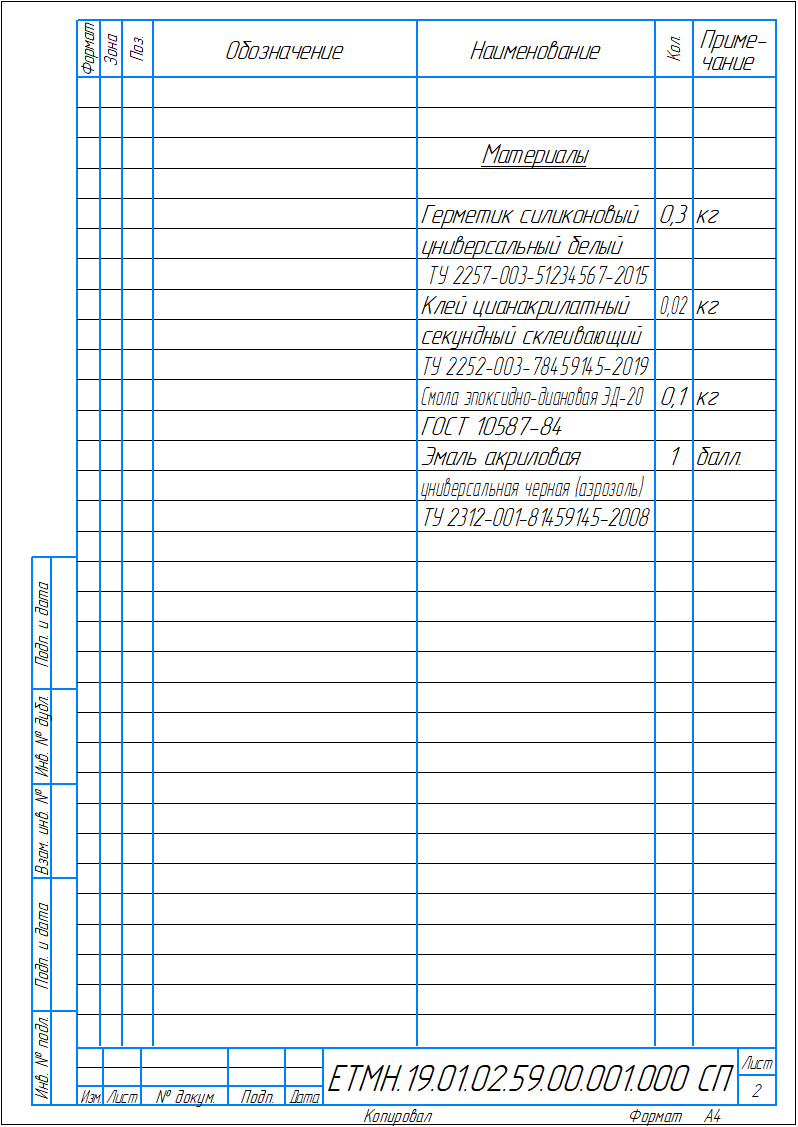
assets/drawing-previews/cdw-stand-2.png
