IImasterII/mitk-rk-site/assets/drawing-previews/cdw-stand.png

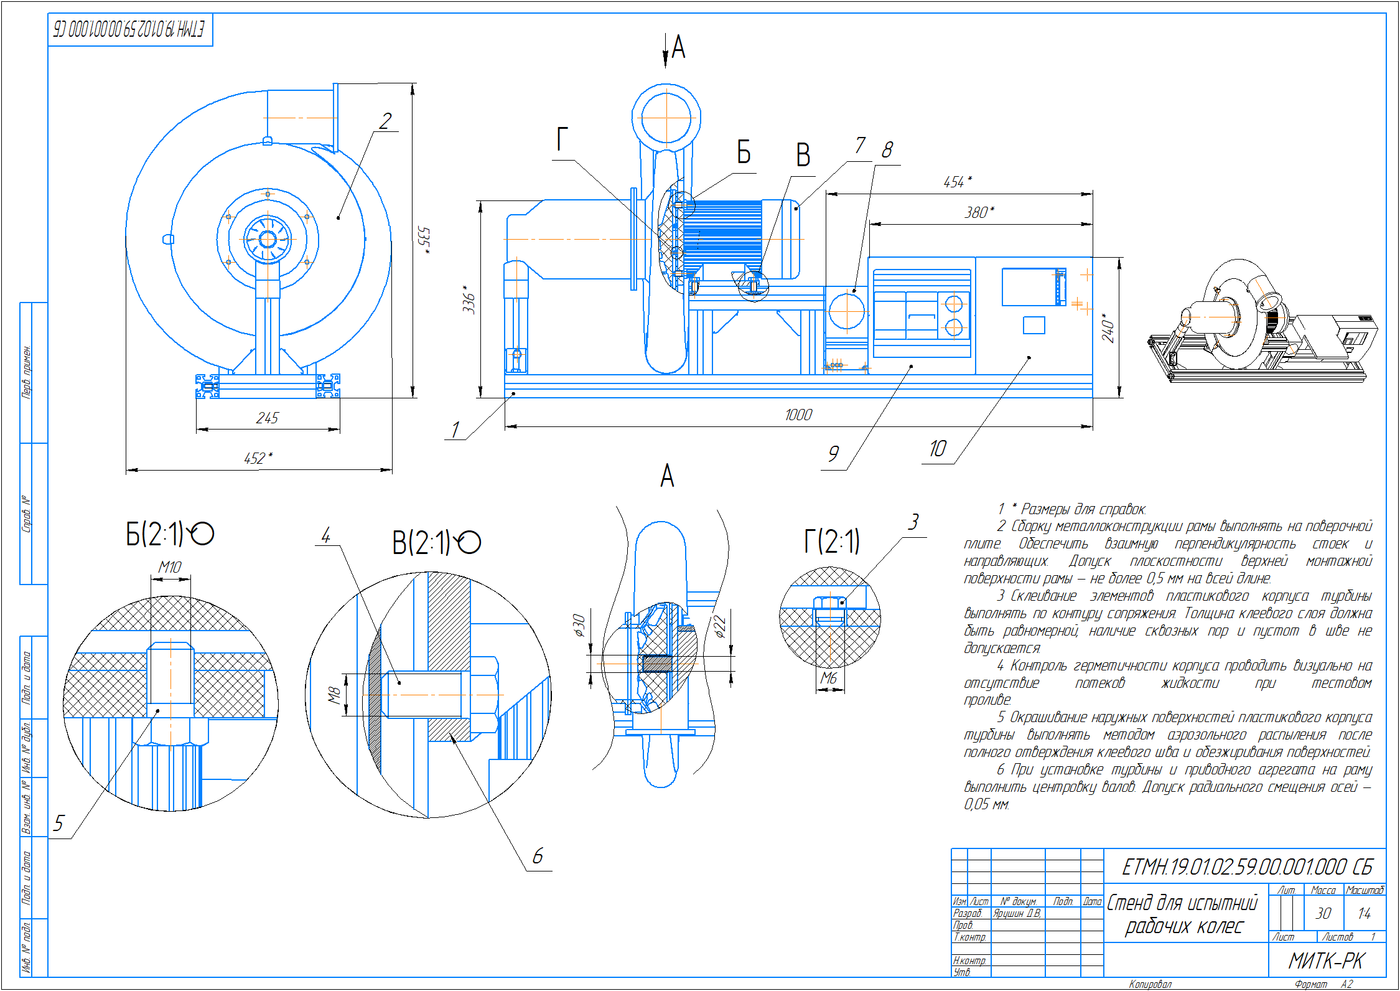
assets/drawing-previews/cdw-stand.png
