IImasterII/mitk-rk-site/assets/drawing-previews/cdw-turbine.png

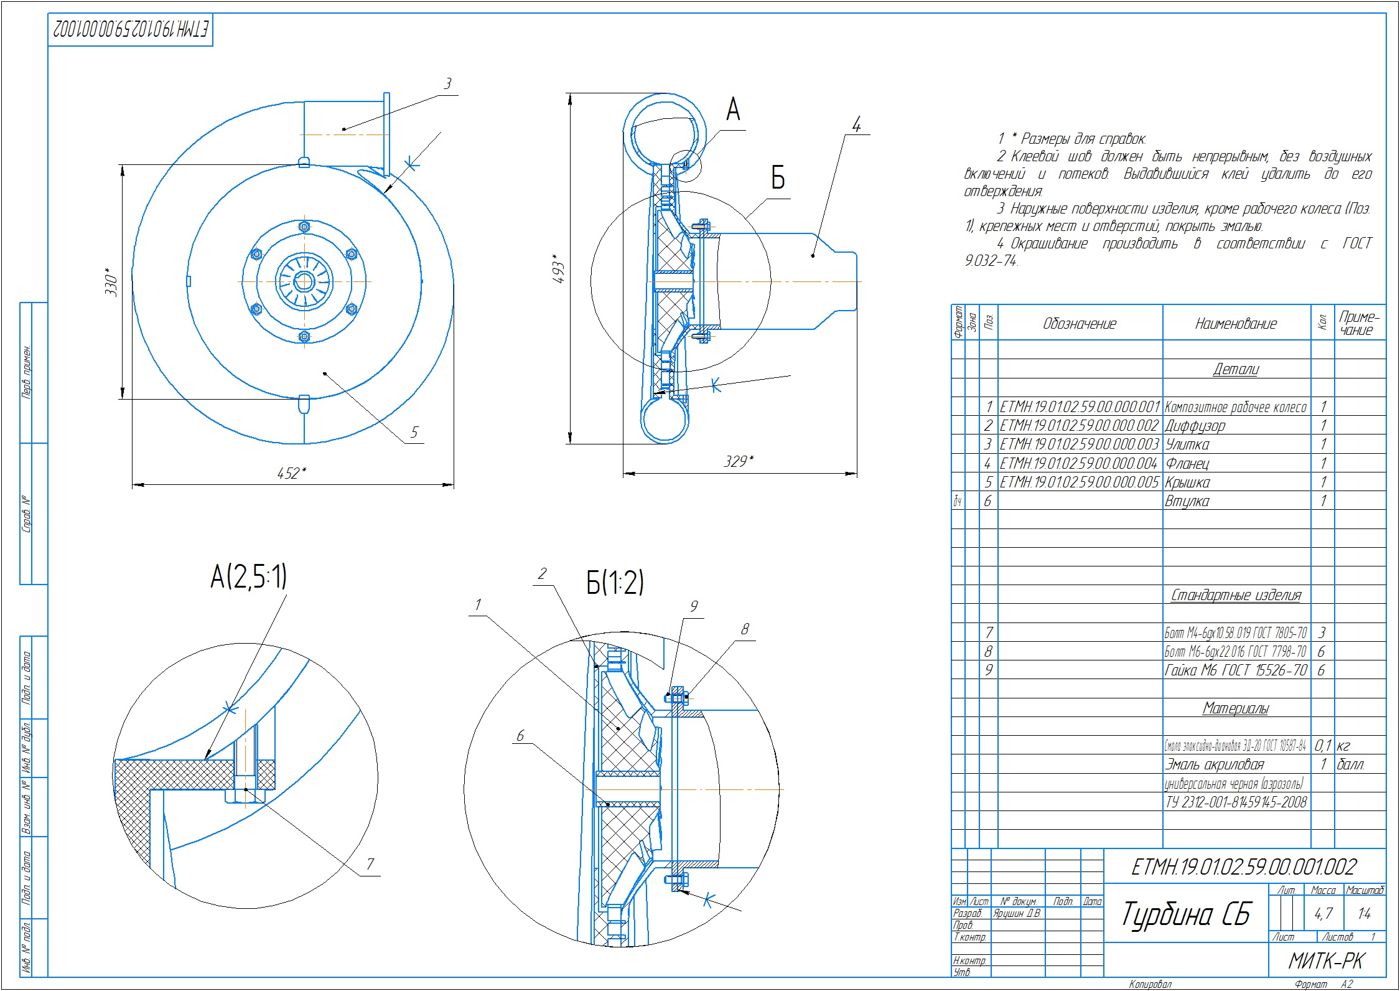
assets/drawing-previews/cdw-turbine.png
