IImasterII/mitk-rk-site/assets/photos/cfd-01.png

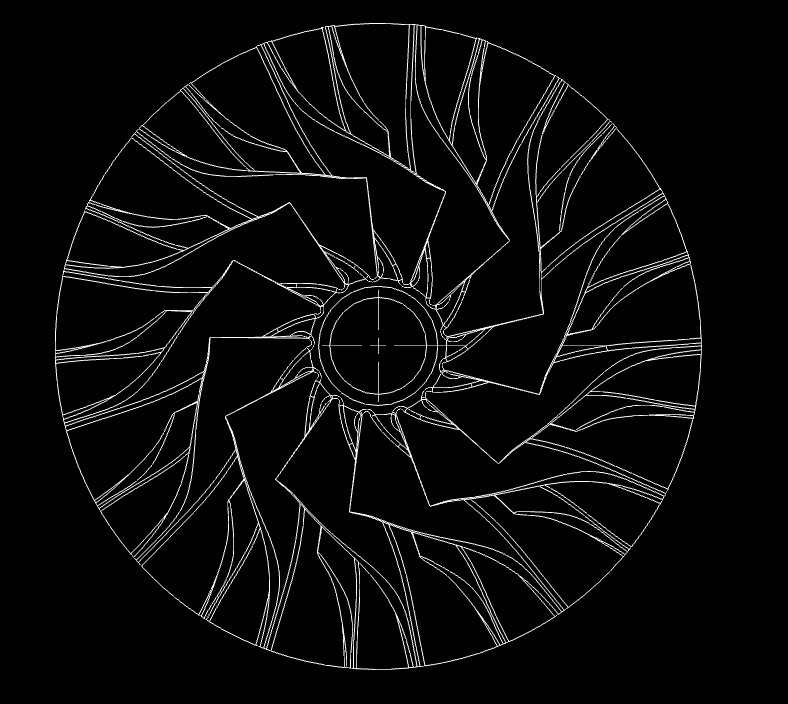
assets/photos/cfd-01.png
