IImasterII/mitk-rk-site/assets/photos/cfd-02.png

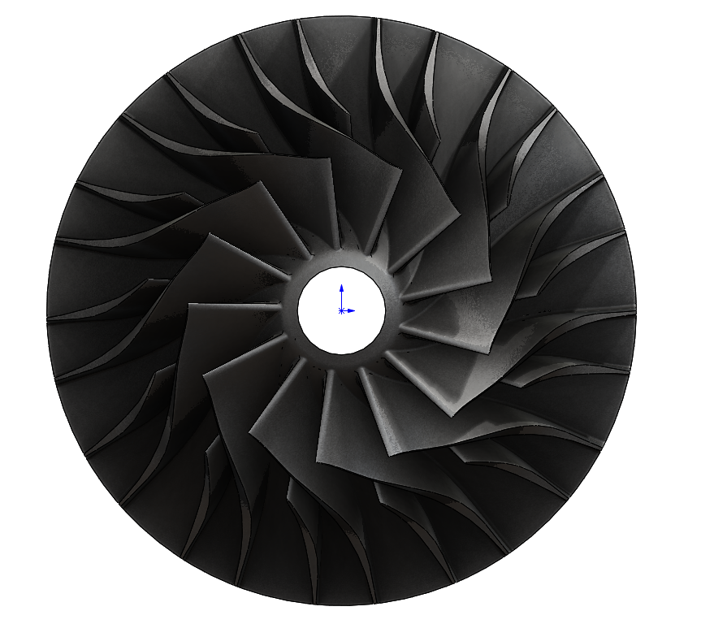
assets/photos/cfd-02.png
