IImasterII/mitk-rk-site/assets/photos/cfd-07.png

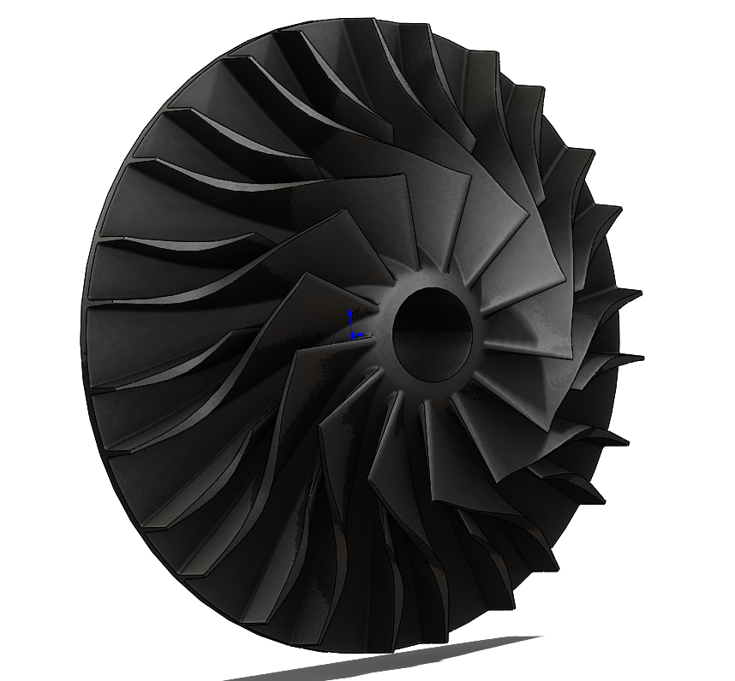
assets/photos/cfd-07.png
