IImasterII/mitk-rk-site/assets/photos/impeller-01.png

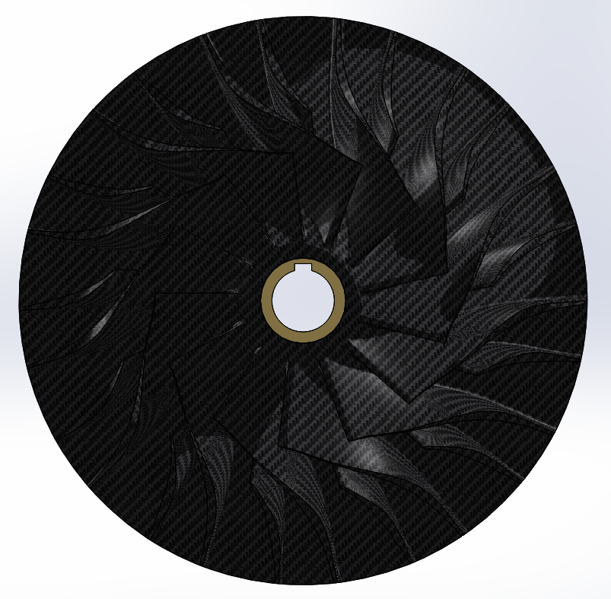
assets/photos/impeller-01.png
