IImasterII/mitk-rk-site/assets/photos/impeller-03.png

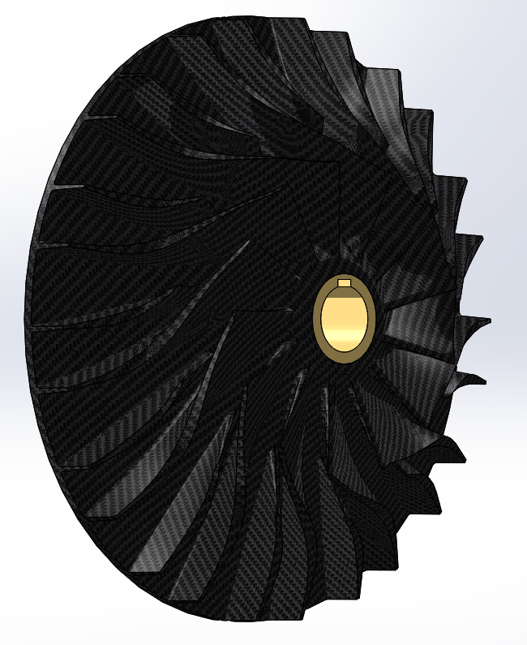
assets/photos/impeller-03.png
