IImasterII/mitk-rk-site/Дополнительное/Чертежи/Фото чертежи/ЕТМН.19.01.02.59.00.000.002 Диффузор.png

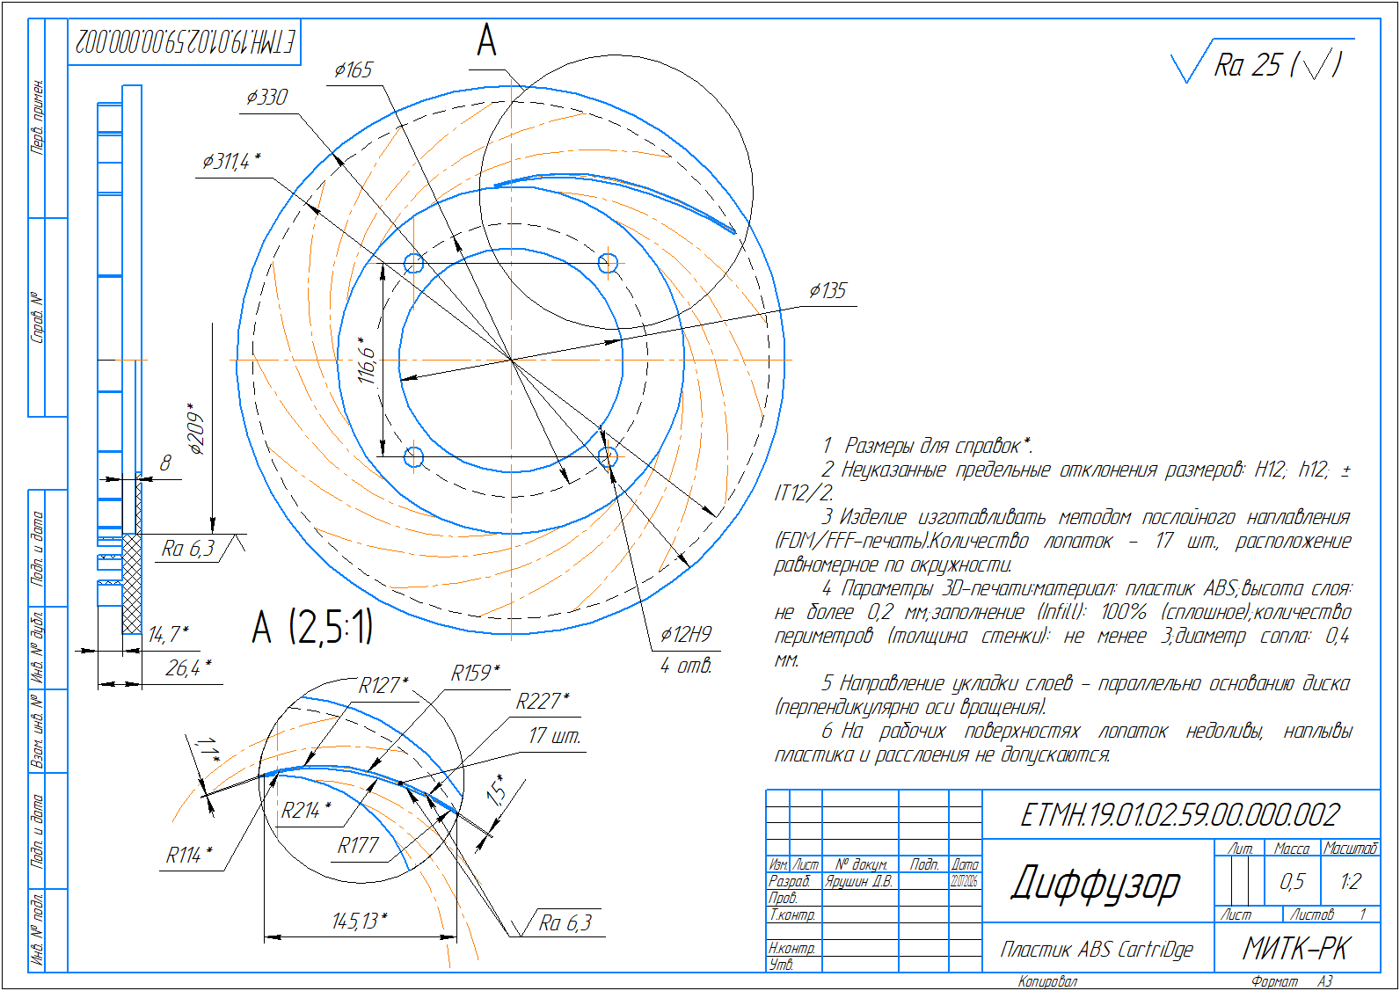
Дополнительное/Чертежи/Фото чертежи/ЕТМН.19.01.02.59.00.000.002 Диффузор.png
