IImasterII/mitk-rk-site/assets/stand/bom-preview.png

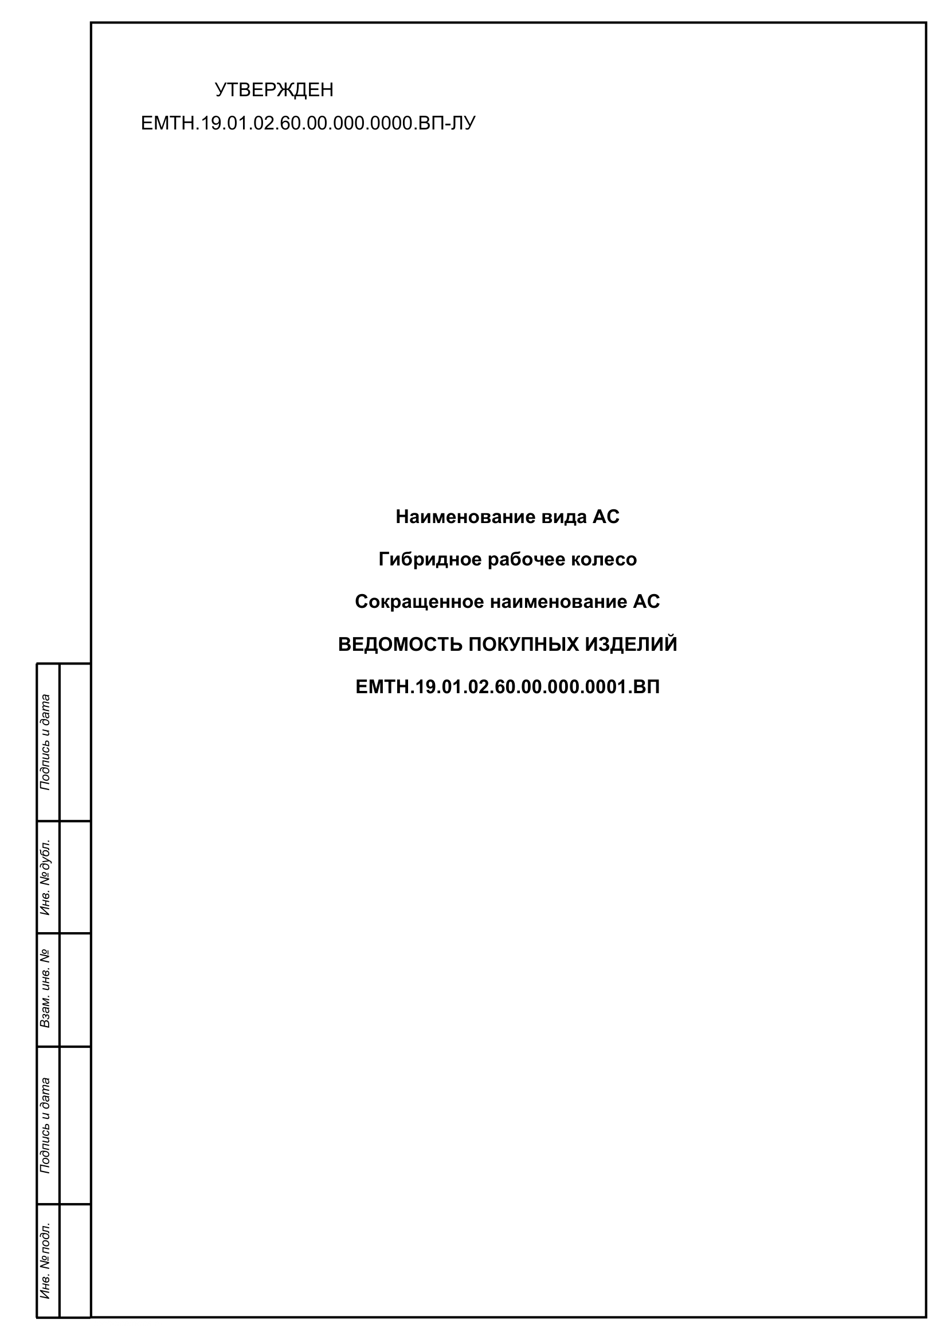
assets/stand/bom-preview.png
