IImasterII/mitk-rk-site/project-materials/Критерии%20оценивания.jpg

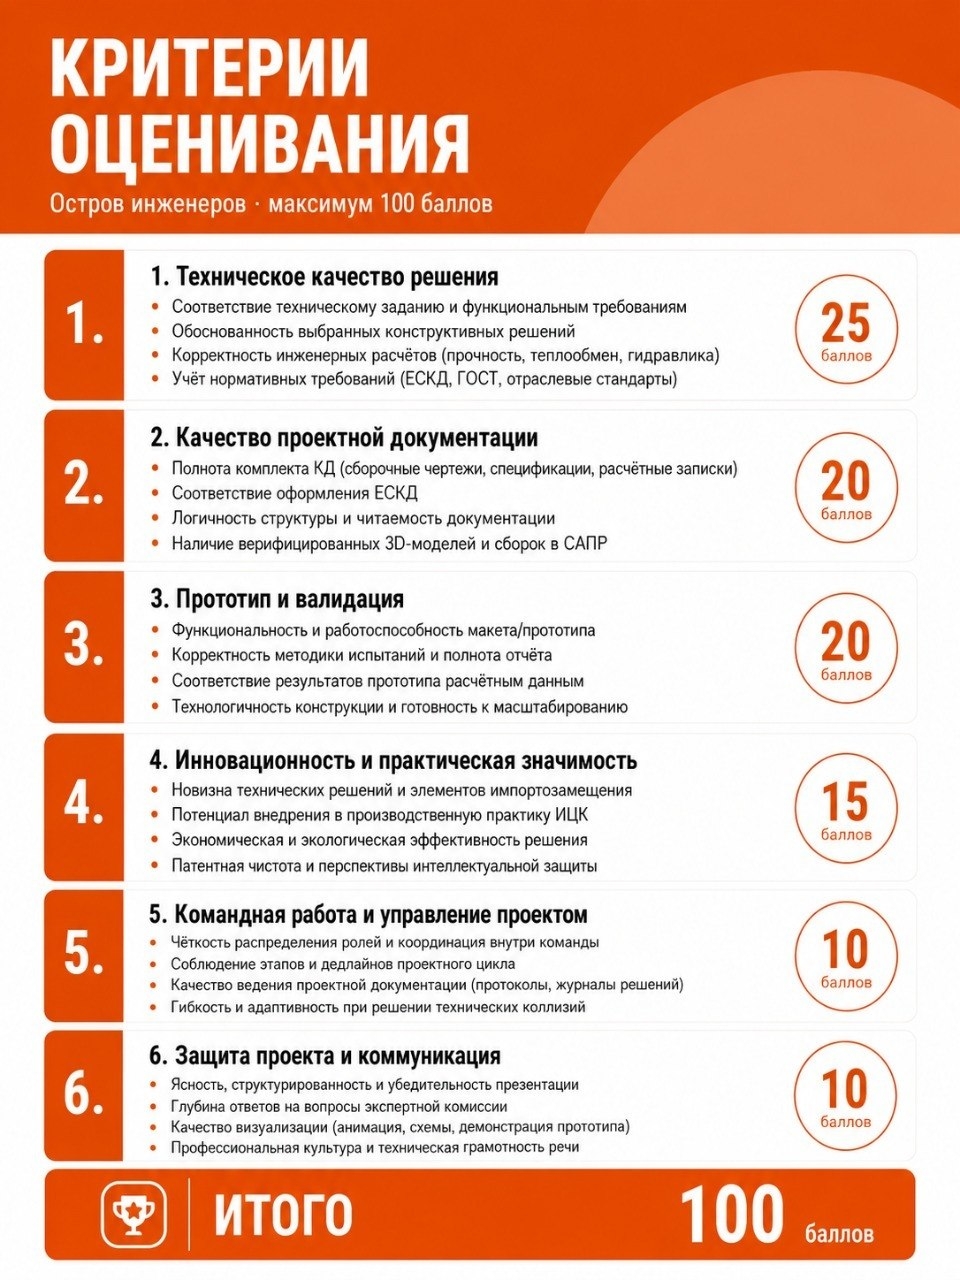
project-materials/Критерии%20оценивания.jpg
