IImasterII/mitk-rk-site/assets/stand/functional-schematic.pdf

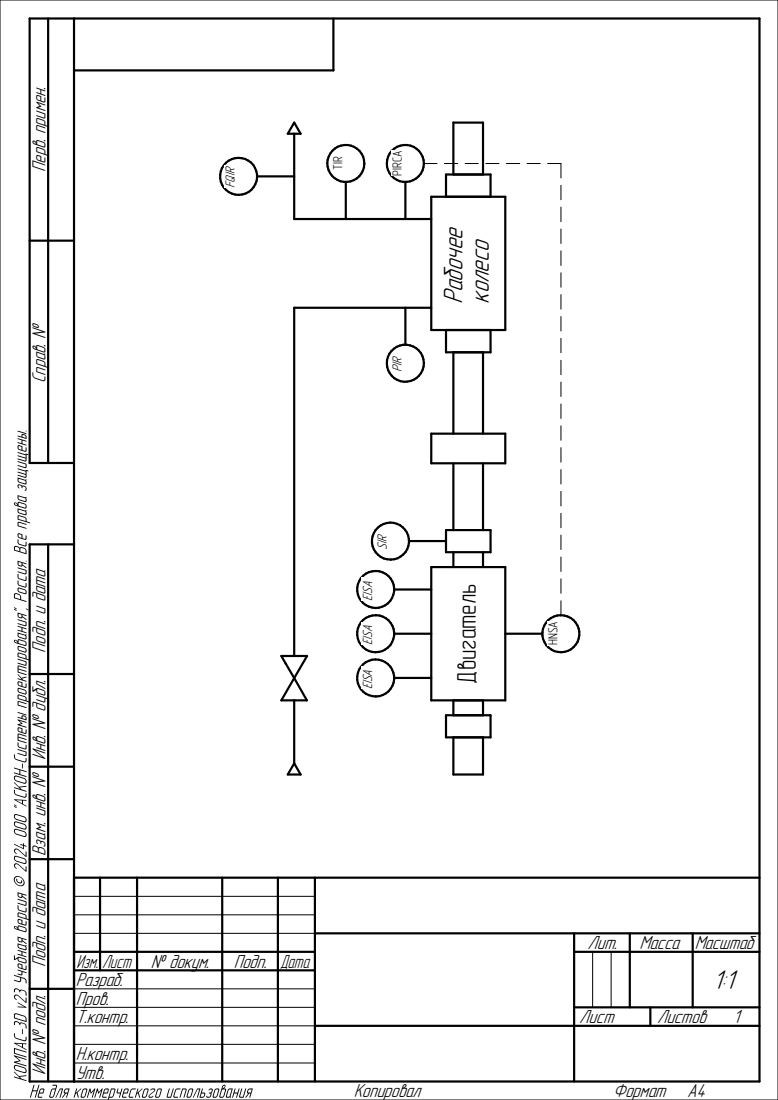
[picture p146: page 1]
Копировал; Формат A4

1 Инв. № подл. Подп. и дата Взам. инв. № Инв. № дубл. Подп. и дата Справ. № Перв. примен.

Двигатель Рабочее колесо EISA EISA EISA SIR PIR FQIR PIRCA TIR HNSA

Лит. | Масса | Масштаб

Изм. Лист | № докум. | Подп. | Дата | | | | | 1:1
Разраб.
Пров.
Т.контр. | | | | Лист | Листов
Н.контр.
Утв.
