IImasterII/mitk-rk-site/documents/brochure.pdf

# МИТК-РК

Команда отвечает за проектирование, расчёт,

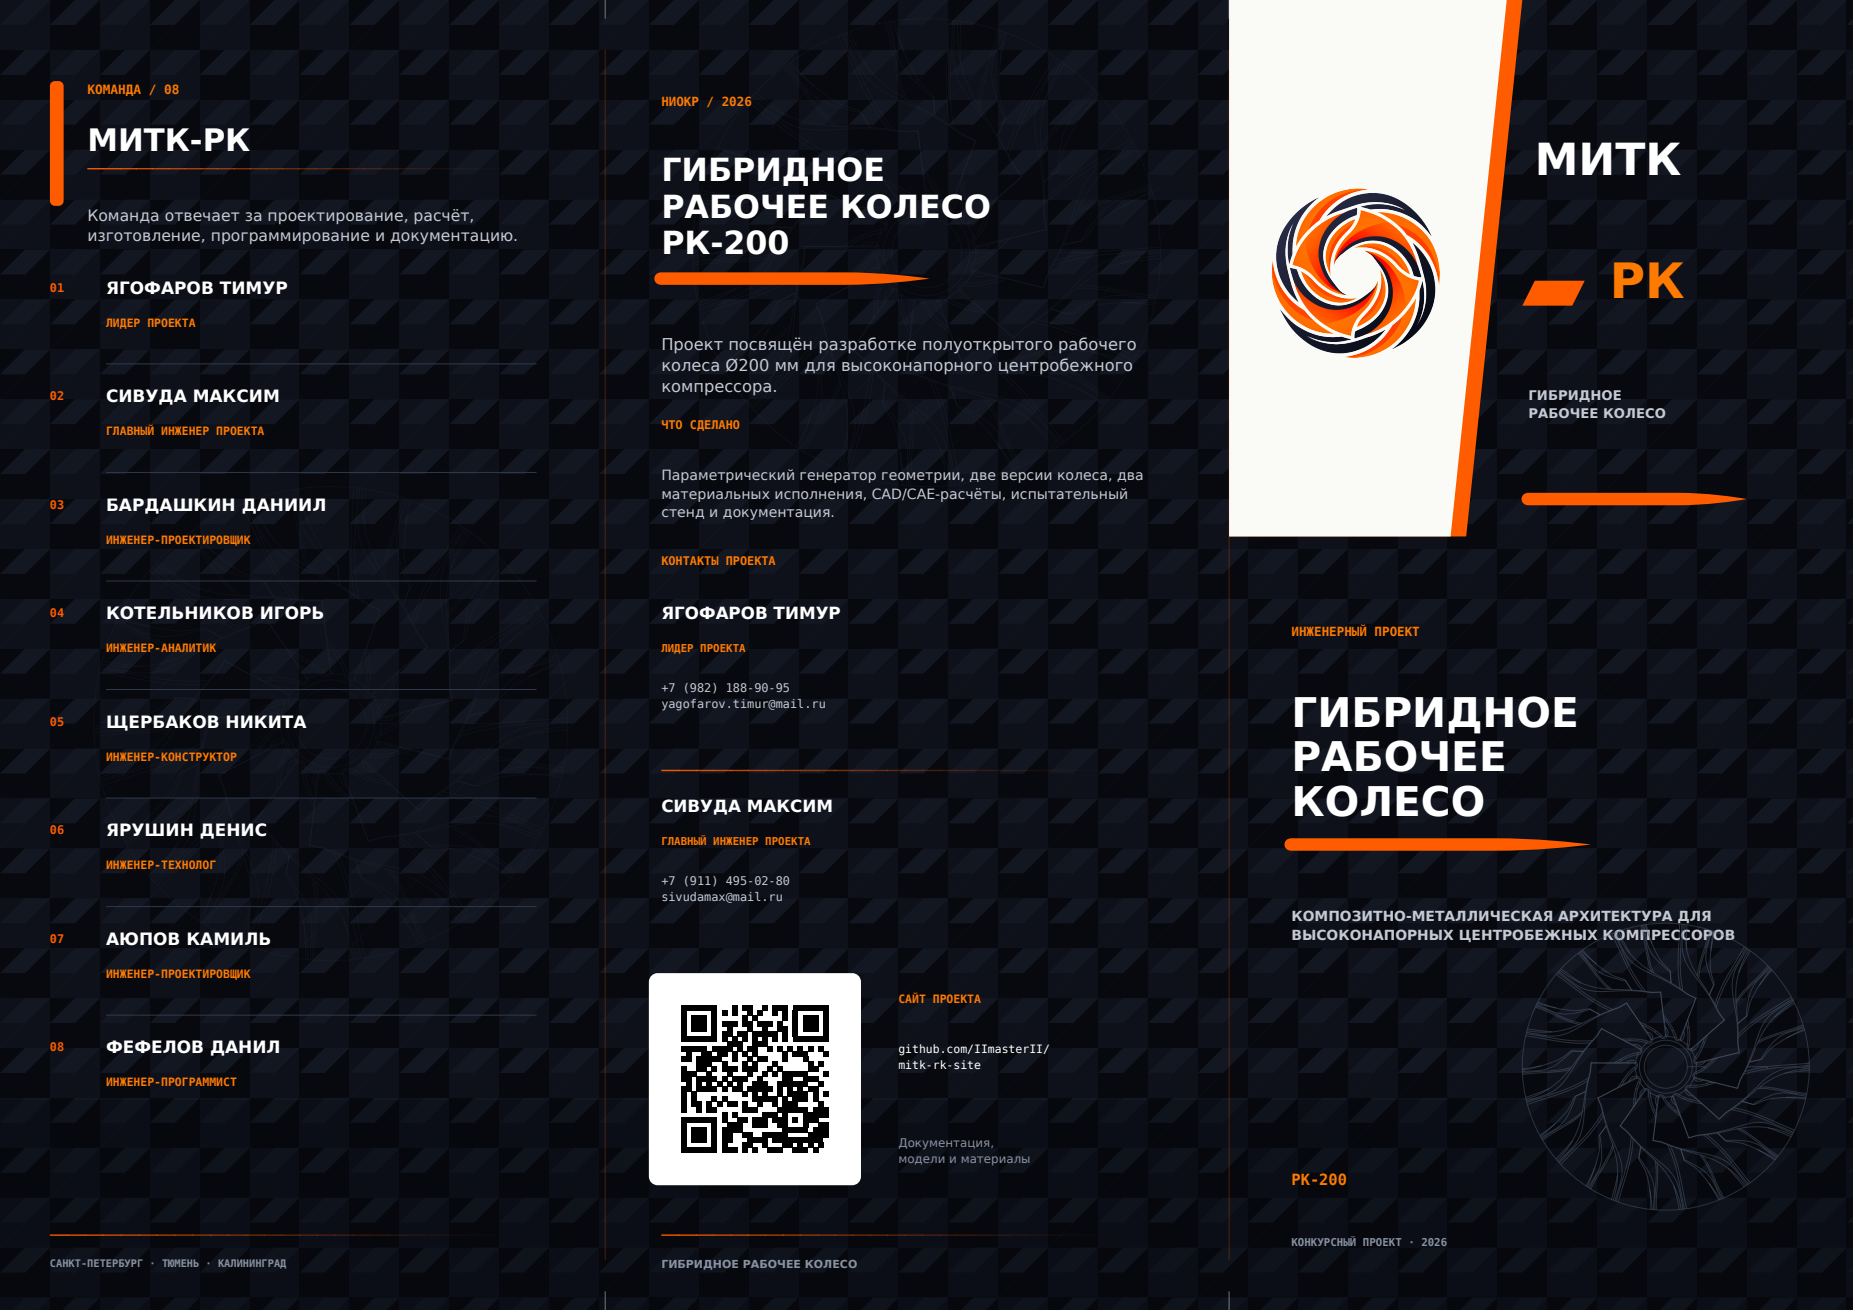
[picture p147: page 1]
КОМАНДА / 08; 01 ЯГОФАРОВ ТИМУР; ЛИДЕР ПРОЕКТА; 02 СИВУДА МАКСИМ; 03 БАРДАШКИН ДАНИИЛ; ИНЖЕНЕР-ПРОЕКТИРОВЩИК; 04 КОТЕЛЬНИКОВ ИГОРЬ; ИНЖЕНЕР-АНАЛИТИК; 05 ЩЕРБАКОВ НИКИТА; ИНЖЕНЕР-КОНСТРУКТОР; 06 ЯРУШИН ДЕНИС; ИНЖЕНЕР-ТЕХНОЛОГ; 07 АЮПОВ КАМИЛЬ; 08 ФЕФЕЛОВ ДАНИЛ; ИНЖЕНЕР-ПРОГРАММИСТ; НИОКР / 2026; ГИБРИДНОЕ РАБОЧЕЕ КОЛЕСО РК-200; ЧТО СДЕЛАНО; КОНТАКТЫ ПРОЕКТА; ЯГОФАРОВ ТИМУР; СИВУДА МАКСИМ; САЙТ ПРОЕКТА; Документация, модели и материалы; МИТК; ГИБРИДНОЕ РАБОЧЕЕ КОЛЕСО; ИНЖЕНЕРНЫЙ ПРОЕКТ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

изготовление, программирование и документацию.

Проект посвящён разработке полуоткрытого рабочего
колеса Ø200 мм для высоконапорного центробежного
компрессора.

ГЛАВНЫЙ ИНЖЕНЕР ПРОЕКТА

Параметрический генератор геометрии, две версии колеса, два
материальных исполнения, CAD/CAE-расчёты, испытательный
стенд и документация.

yagofarov.timur@mail.ru

sivudamax@mail.ru

КОМПОЗИТНО-МЕТАЛЛИЧЕСКАЯ АРХИТЕКТУРА ДЛЯ
ВЫСОКОНАПОРНЫХ ЦЕНТРОБЕЖНЫХ КОМПРЕССОРОВ

github.com/IImasterII/
mitk-rk-site

САНКТ-ПЕТЕРБУРГ · ТЮМЕНЬ · КАЛИНИНГРАД

ГИБРИДНОЕ РАБОЧЕЕ КОЛЕСО

# Что сделано в проекте

## Разработано полуоткрытое рабочее колесо Ø200 мм для

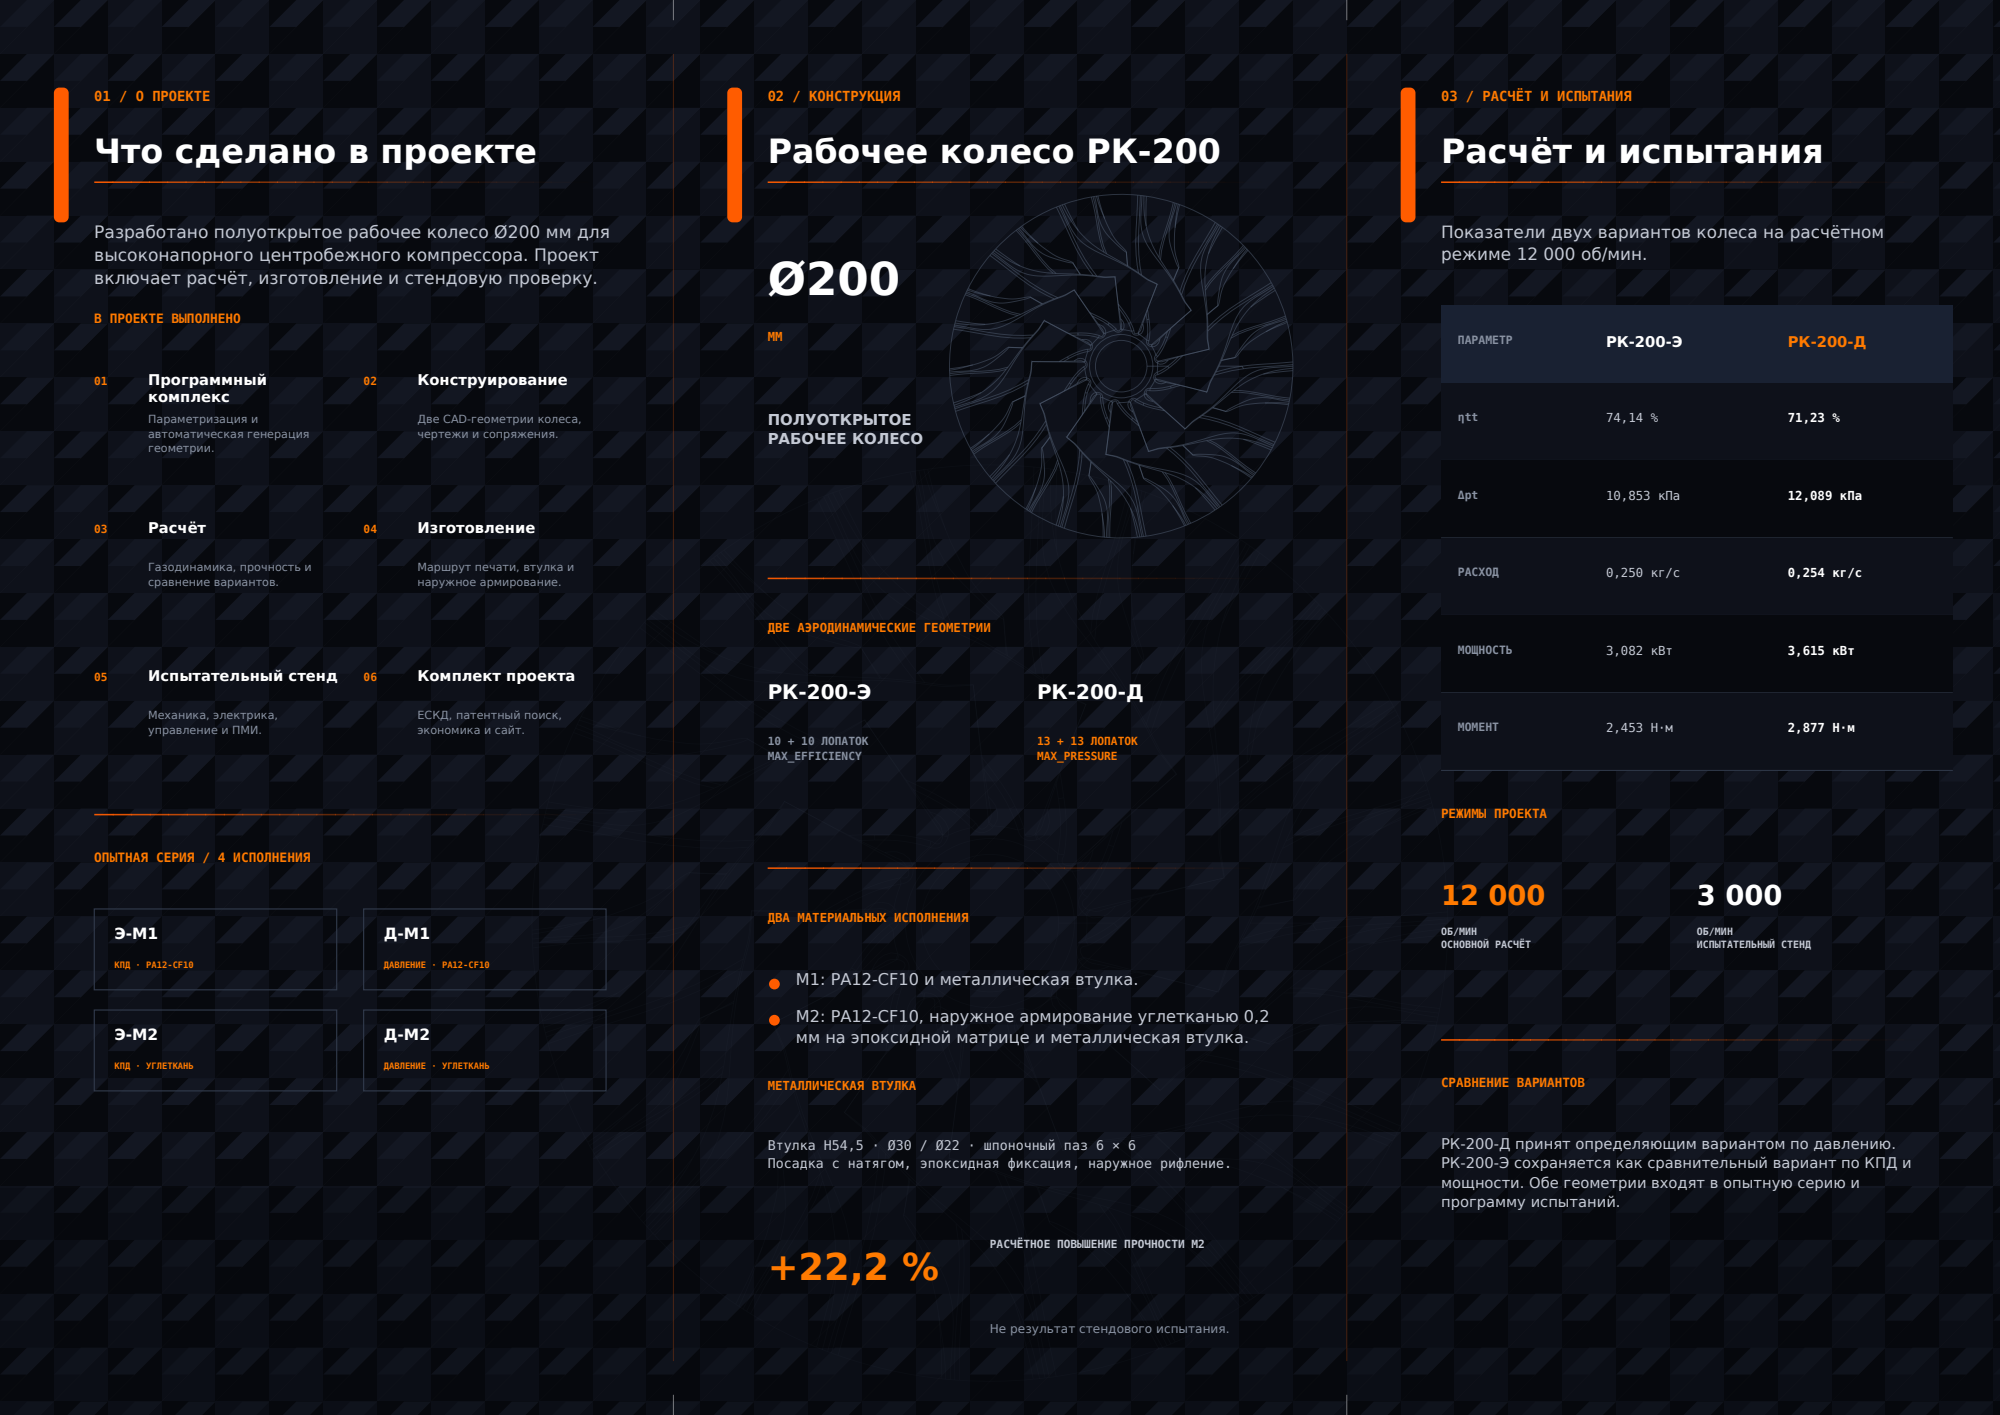
[picture p148: page 2]
01 / О ПРОЕКТЕ; В ПРОЕКТЕ ВЫПОЛНЕНО; 01 Программный комплекс; Параметризация и автоматическая генерация геометрии.; 02 Конструирование; 03 Расчёт; Газодинамика, прочность и сравнение вариантов.; 04 Изготовление; 05 Испытательный стенд; Механика, электрика, управление и ПМИ.; 06 Комплект проекта; КПД · PA12-CF10; ДАВЛЕНИЕ · PA12-CF10; КПД · УГЛЕТКАНЬ; ДАВЛЕНИЕ · УГЛЕТКАНЬ; ПОЛУОТКРЫТОЕ РАБОЧЕЕ КОЛЕСО; 10 + 10 ЛОПАТОК MAX_EFFICIENCY; 13 + 13 ЛОПАТОК MAX_PRESSURE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

02 / КОНСТРУКЦИЯ
Рабочее колесо РК-200

Показатели двух вариантов колеса на расчётном
режиме 12 000 об/мин.

высоконапорного центробежного компрессора. Проект
включает расчёт, изготовление и стендовую проверку.

Две CAD-геометрии колеса,
чертежи и сопряжения.

Маршрут печати, втулка и
наружное армирование.

ДВЕ АЭРОДИНАМИЧЕСКИЕ ГЕОМЕТРИИ

ЕСКД, патентный поиск,
экономика и сайт.

ОПЫТНАЯ СЕРИЯ / 4 ИСПОЛНЕНИЯ

ДВА МАТЕРИАЛЬНЫХ ИСПОЛНЕНИЯ

M2: PA12-CF10, наружное армирование углетканью 0,2
мм на эпоксидной матрице и металлическая втулка.

Втулка H54,5 · Ø30 / Ø22 · шпоночный паз 6 × 6
Посадка с натягом, эпоксидная фиксация, наружное рифление.

РК-200-Д принят определяющим вариантом по давлению.
РК-200-Э сохраняется как сравнительный вариант по КПД и
мощности. Обе геометрии входят в опытную серию и
программу испытаний.

РАСЧЁТНОЕ ПОВЫШЕНИЕ ПРОЧНОСТИ M2

Не результат стендового испытания.
