IImasterII/mitk-rk-site/calculations/Myreport_pressure_12000_bonded_without_vtulka(1).pdf

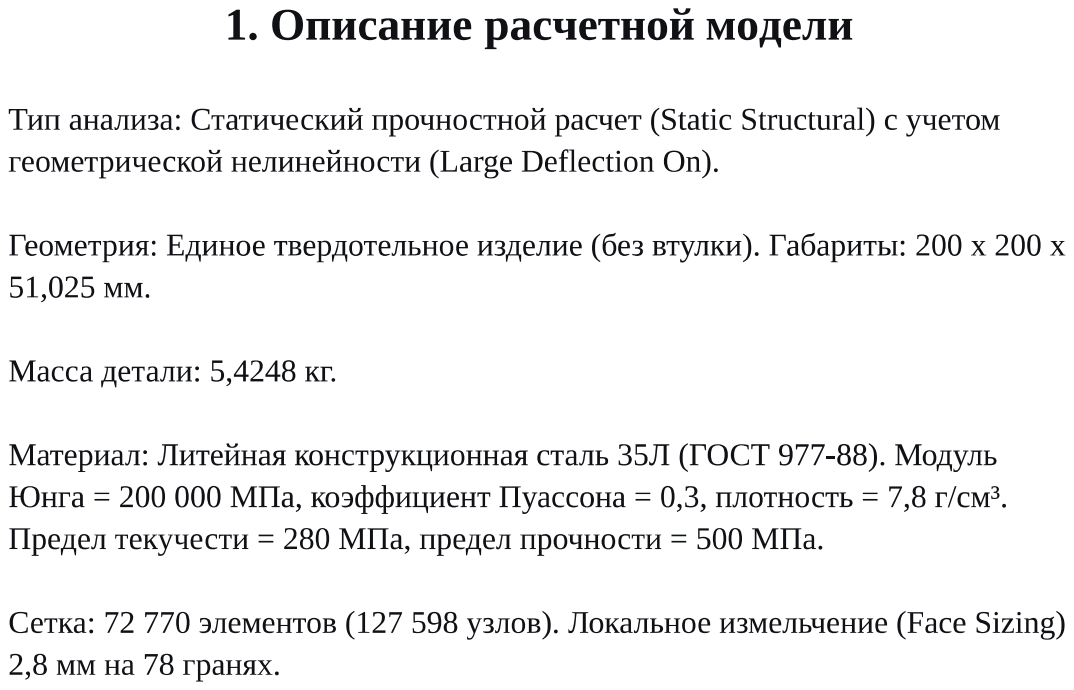
[picture p149: page 1]

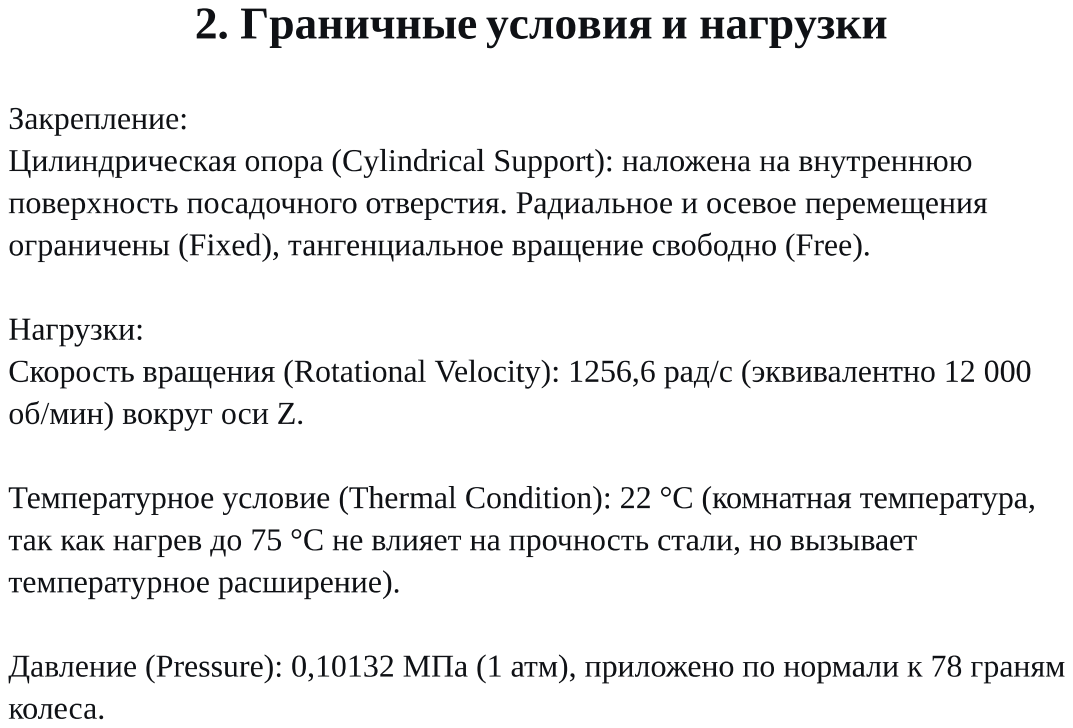
[picture p150: page 2]

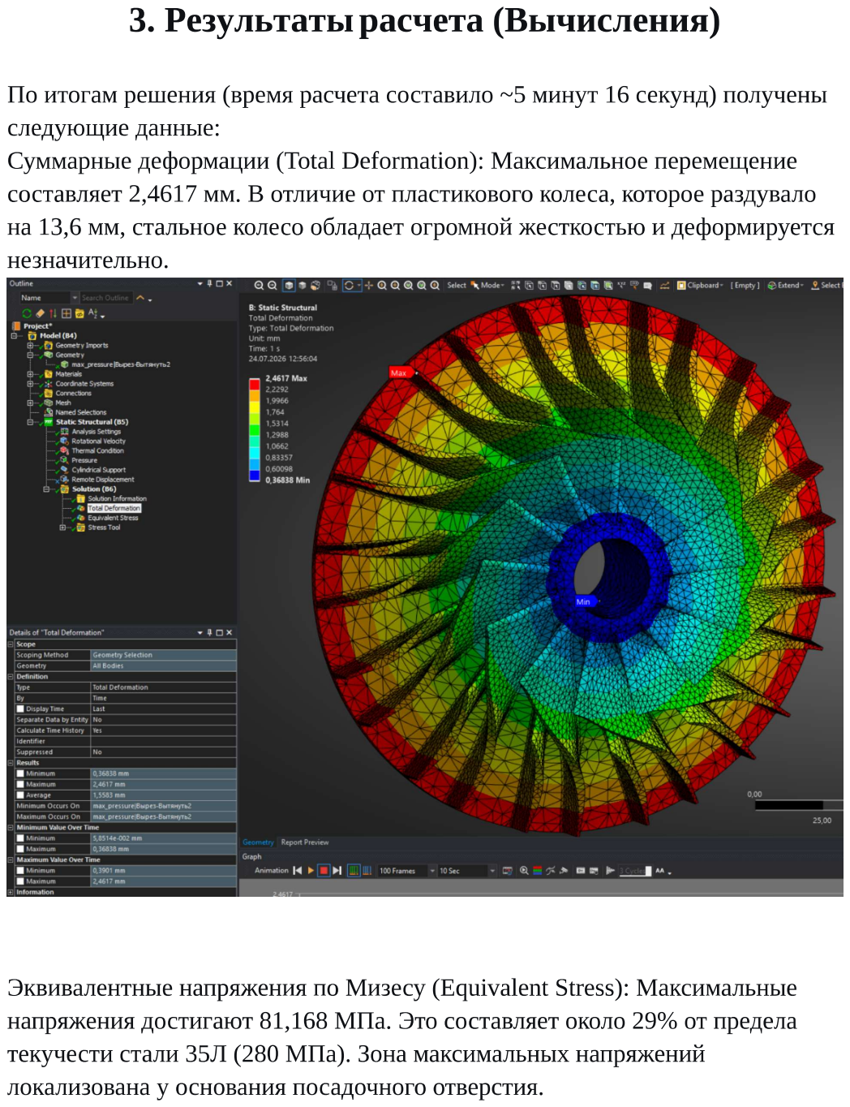
[picture p151: page 3]

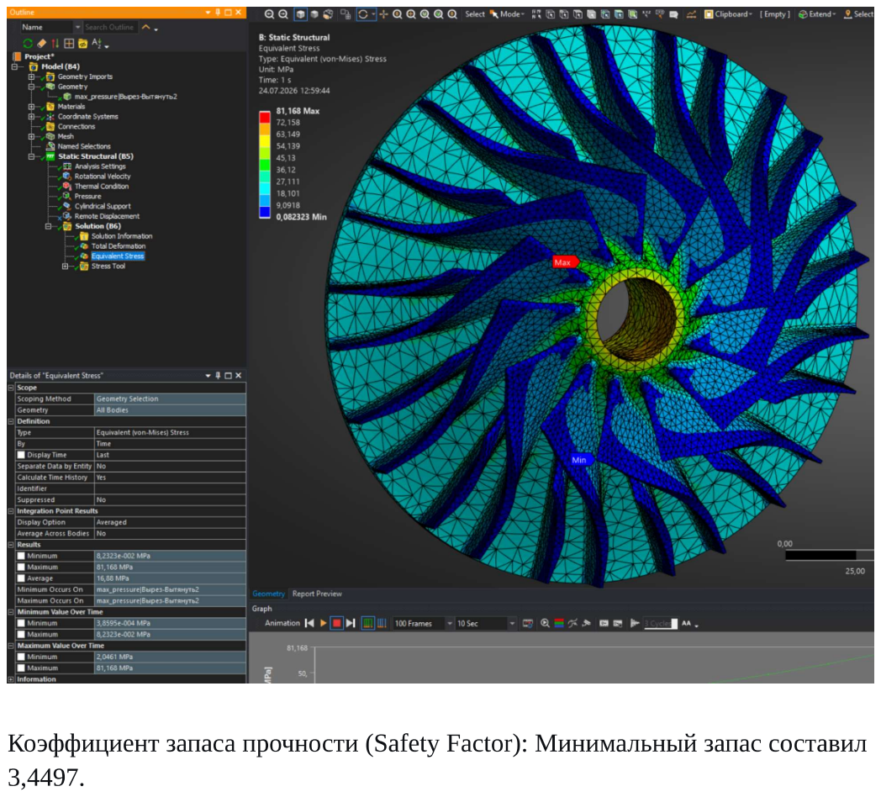
[picture p152: page 4]

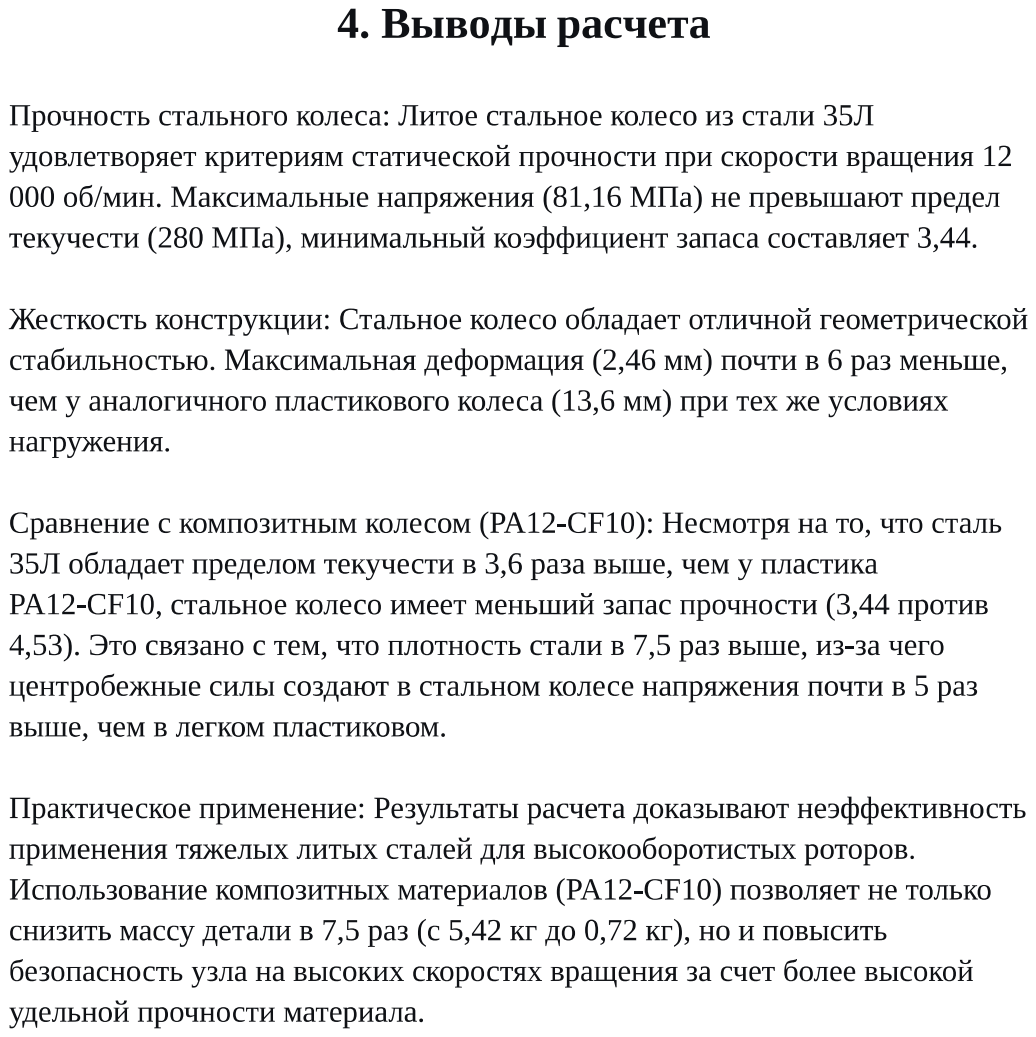
[picture p153: page 5]
